layered-logic/infinity-mirror/docs/Market Analysis Report.md

---
title: Market Analysis Report
type: research
phase: 1
week: 1
date: 2026-04-06
status: complete
tags: [market, competitive, research]
---

# Market Analysis Report: The Infinity Mirror Venture
**Date:** April 6, 2026  
**Subject:** High-Rigor Assessment of Bespoke Infinity Mirrors & Illuminated Art Markets

---

## 1. Executive Summary
The market for infinity mirrors in 2026 is highly bifurcated. It is characterized by extreme price saturation at the commodity level and a growing "quality-first" recalibration at the artisanal and B2B levels. Recent market data indicates that while the "novelty" of the infinity effect has plateaued, its application as a **branding tool** and **wellness-oriented art piece** is expanding. To survive, a venture must move beyond the "maker" aesthetic to address specific 2026 pressures: protocol fragmentation (Matter/Thread), 2026 supply chain volatility, and intensifying "Right to Repair" legislation.

---

## 2. Market Segmentation & Strategic Projections

### **The "Dynamic LED" Pivot**
Industry data for 2026 confirms a decisive shift away from static glass neon and simple RGB strips.
* **Generative Art Demand:** According to the *2026 Art Trends Forecast*, collectors are prioritizing "Materiality" and "New Media" that feels organic. Addressable LEDs (WS2812B/ESP32) allow for non-repeating, generative patterns that static signage cannot replicate.
* **Atmospheric Wellness:** The **$18.4 Billion** smart lighting market now prioritizes "Circadian Integration." Static mirrors are viewed as "passive decor," whereas dynamic mirrors are sold as "active wellness" tools for focus and mood management.

### **Market Quadrants**
| Segment | Est. Price Range | Primary Materials | Key Technology |
| :--- | :--- | :--- | :--- |
| **Bespoke Luxury** | $800 – $5,000+ | Glass, Aluminum, Wood | High-Density LED, Concierge Support |
| **B2B Branding** | $250 – $1,200 | Acrylic, Metal, UV Print | Custom Firmware, SLA Reliability |
| **Sensory/Therapy** | $230 – $4,300 | High-Impact Acrylic | Simplified UI, Pulse-Width Modulation |
| **Lifestyle/Gaming** | $40 – $250 | 3D-Printed, Plastic | 2.4GHz Wi-Fi, App-Heavy |

---

## 3. Risk Assessment

### **A. Market Saturation & "Etsy Erosion"**
A cross-platform scrub of Etsy and Amazon reveals over **1,900 listings** for "Infinity Mirror Logos."
* **The Data:** Listings range from **$3.75 (Digital Files)** to **$7,860 (Large Scale Installations)**.
* **The Risk:** The $50–$120 price bracket is flooded with hobbyist-grade 3D-printed units. In this environment, a professional venture risks "Brand Bleed" if the industrial design does not immediately signal a $200+ value proposition through material weight and finish quality.

### **B. Technical Fragmenting & Hub Fatigue**
* **The Shift:** As of 2026, **Matter-over-Thread** has reached maturity. Apple and Google have largely withdrawn native support for non-Matter Wi-Fi accessories in their newest OS updates.
* **The Risk:** A product relying solely on a proprietary 2.4GHz Wi-Fi app is now classified as **"Technical Debt."** Consumers are increasingly rejecting "one-off" apps in favor of integrated Home Assistant or Matter-certified ecosystems.

### **C. Macro-Economic Discretionary Selectivity**
* **The Data:** The *2026 U.S. Art Market Report* notes that while high-income spending remains robust in the West (California/Washington), "Selectivity" has risen. The number of artists represented at auction dropped by nearly **20% in 2025**, indicating a flight to quality and established craftsmanship.
* **The Risk:** Mid-tier "discretionary" art ($150–$400) is highly vulnerable to current 2026 inflationary pressures compared to the "trophy" market or the $20 impulse market.

### **D. Regulatory & Compliance (FCC Part 15)**
* **The Reality:** Any addressable LED driver is an **unintentional radiator**.
* **The Risk:** FCC enforcement, though budget-constrained in 2026, is utilizing AI-driven monitoring to flag non-compliant electronic sellers. Commercial fines for non-certified intentional/unintentional radiators can exceed **$10,000 per violation**. This is a non-negotiable hurdle for B2B contracts.

### **E. Repairability Liability**
* **The Shift:** 2026/2027 **Right to Repair** legislation (notably the EU Directive and corresponding WA/CA bills) now mandates that electronics must be repairable using "standard tools and parts" for up to 7–10 years.
* **The Risk:** Products designed as "sealed units" are increasingly becoming illegal to sell in major markets. The venture’s "Modular/Toolless" design is not just a feature; it is a **legislative necessity**.

---

## Appendix A: Research Sources
1. **Agora Gallery:** *Top Art Trends for 2026 (Materiality & New Media Focus).*
2. **Merrill Lynch:** *2026 U.S. Art Market Report (Data on Regional Spending & Selectivity).*
3. **Gemini Made:** *2026 Signage Industry Trends (Shift to One-Stop Shops & Dimensional Signs).*
4. **Sunfire Testing:** *2026 FCC Certification Costs & Unintentional Radiator Guidelines.*
5. **Zbotic:** *Zigbee vs. Matter vs. Thread: 2026 Smart Home Protocol Guide.*
6. **Mordor Intelligence:** *Zigbee & Matter Market Share Analysis (2025-2031).*
7. **Taylor Wessing:** *New Repair Obligations for Manufacturers in 2026 (Legislative Brief).*
8. **Etsy Market Data:** *Current Pricing & Saturation Metrics for "Infinity Mirror Logo" Listings.*
9. **LaunchBoom Research:** *2026 Success Rates for Hardware Crowdfunding.*
10. **Waste Dive:** *2026 Update on State-Level Electronic Repairability Laws.*

---

## Appendix B: Product & Competitive Index

### I. Bespoke Luxury & High-End Art
* **6sigmainteriors:** Custom Aluminum Infinity Mirrors ($824.59+).
* **Light Energy Studio:** High-end casino and commercial installations.
* **Yayoi Kusama:** Immersive gallery benchmarks.
* **1stDibs:** Resale value index for Mid-Century and Art Deco Infinity Mirrors.
* **Yayoi Infinity:** Large-scale residential immersion mirrors ($2,000+).

### II. B2B Branding & Commercial
* **IDM Signs & Graphics:** 3D LED Optical Illusion Signs ($100 Deposit model).
* **Luckyneon:** Modular RGB Infinity Channel Letters.
* **Yijiao Sign:** Industrial-scale 3D Acrylic/Metal signage.
* **AOOS:** Custom 3D Tunnel Mirrors for Restaurant/Bar branding.
* **Litasign:** High-volume commercial infinity displays.

### III. Lifestyle & Gaming Decor
* **Maytrix Studio:** Octagon Smart Mirrors with Tuya integration ($222.00).
* **InfiniMini:** 6"x6" Desk Mirror competitor ($44.99).
* **Walmart:** Mass-market Hologram Infinity Mirrors ($89.99).
* **Etsy (Various):** UV-Printed Photo Infinity Boxes ($45.00–$65.00).
* **Gamer-Light:** Niche Twitch/YouTube set decor.

### IV. Sensory & Therapy
* **Enabling Devices:** Sensory Infinity Mirror with Gumball Switch ($230.95).
* **National Autism Resources:** High-durability clinical tunnels ($2,299+).
* **Westminster Tech:** Architectural-scale interactive sensory walls.
* **TFH Special Needs:** Cause-and-effect learning infinity mirrors.
* **Experia USA:** Full-scale Snoezelen-certified sensory room mirrors.

---

## Related

- [Index / MOC](../index.md)
- [Stakeholder Map](stakeholder-map.md) — customer archetypes (§3) cite this report's segments
- [BOM Breakdown](bom-breakdown-basic-6x6.md) — pricing strategy responds to the $50–120 saturation risk flagged here
- [Brand Positioning](brand-positioning.md) — positioning builds on the market bifurcation
- [Sustainability Audit](sustainability-audit.md) — right-to-repair legislation flagged here, validated there
- [Right-to-Repair Philosophy](right-to-repair-philosophy.md) — the pro-consumer posture response to §3.E regulatory context
- [Sprint Plan](../sprint_plan.md)
