layered-logic/infinity-mirror/sprint_log.md

---
title: Spring 2026 Sprint Log
type: tracking
quarter: Spring 2026
status: active
tags: [sprint, log, progress]
---

# Sprint Log — Spring 2026

Progress tracker for the Infinity Mirror sprint plan. Organized by sprint week.
Each entry is a human-written description with a date and an inline `[LL-NNN]`
link into the [task registry](tasks.md). The registry is the structured source
of truth for task identity, status, and history; the log is the daily narrative.

Format spec: [docs/task-format-v2.md](docs/task-format-v2.md). Append-only event
history is tracked separately in [task_log.md](task_log.md).

---

> **Weeks 1–6 (Mar 30 – May 9) are archived** in [sprint_log_archive.md](sprint_log_archive.md) — moved out to keep this file small. Task status lives in [tasks.md](tasks.md); event history in [task_log.md](task_log.md).

---

## Week 7 (May 12 – May 16): Service Blueprinting & The Custom Experience

### Done
- [x] [LL-074](tasks.md#LL-074) **User-flow authoring methodology locked + Stage 1 (Discover) drawn (May 13).** Emerged organically as a drill-down on [LL-053](tasks.md#LL-053): Bill asked whether each service-blueprint stage could be visualized as a Figma-style user flow, and we used Stage 1 as the methodology probe. Six iterations across one session produced both the locked HCDE grammar AND a reusable rendering recipe — both now reference artifacts the remaining nine stages will be authored against.
  - **Methodology decisions locked** in [docs/service-blueprint-flows.md § Conventions](docs/service-blueprint-flows.md): (1) Pain points reframed as user-voice diamonds (`Can I imagine this in my space?` instead of `Pain: scale not conveyed`) — flow becomes predictive of user thought process, not descriptive of system state. (2) Two-layer pain evaluation — pain question → recovery probe (also a user-voice diamond, `Is there a tool to help me visualize it?`) → either rejoins golden path on Yes or terminates at a yellow `Missing: X` callout on No. Each `Missing:` terminal is a concrete build-this backlog item. (3) Orange diamond = friction the user is evaluating; red oval = exit (user gone). The shape/color asymmetry is the story — a flow can have many friction points but only a few exits. (4) Natural cognitive order enforced for sequential question chains; for consumer-purchase Stage 1 the cascade is vibe → visualize → value → trust → timing (aesthetic gut check fires fastest, nobody visualizes a piece in their space before deciding they like the look of it). (5) Recovery is optional, not paired — some pains are genuinely unfixable at this stage (wrong vibe, wrong time) and route directly to red bounce. (6) Modality compression: multiple entry points must differ in user behavior or motivation, not channel — *Etsy listing* and *IG listing* are the same encounter for flow purposes.
  - **Rendering recipe locked** in [docs/user-flow-authoring.md](docs/user-flow-authoring.md). Mermaid ruled out: default bezier curves are too curvy; the `step` curve gives right-angle bends but no port control; the ELK plugin fails to load reliably from CDN and breaks the entire render. Switched to **Graphviz via `@viz-js/viz@3` (WASM bundle from jsdelivr)** with `splines=ortho`, explicit port specifiers on every edge (`source:e -> target:w` for Yes, `source:s -> target:n` for No), per-column `rank=same` groups, and `weight=10` on every happy-path edge to keep the top row aligned. The high-value gotcha — easy to get wrong, hard to debug from output: **in `rankdir=LR`, `rank=same` means same *column* (vertical strip), not same row.** First attempt put the whole happy path in one `rank=same` group, expecting horizontal alignment; instead got every node stacked vertically into one column with top-down primary reading order. Fixed by using per-column rank groups (each pain diamond stacked with its own bounce/recovery/missing in that diamond's column) and letting Graphviz auto-layout handle the happy path. Doc captures the rejected approaches as a debugging log so future-me doesn't relitigate.
  - **Stage 1 (Discover) drawn** in both Mermaid (renders inline in [service-blueprint-flows.md](docs/service-blueprint-flows.md) under GitHub / Obsidian with step curves) and Graphviz DOT (renders strict grid-style in [.preview/stage1.html](.preview/stage1.html) — open in any browser, viz-js loads from CDN, renders to inline SVG, no build step). Five pain diamonds along the golden path (`Does this fit my vibe?` → `Can I imagine this in my space?` → `Is this worth what they're asking?` → `Can I trust this maker?` → `Is now a good time for me to engage?`), each `Yes` continuing right, each `No` dropping down. Q1 and Q5 go straight to red bounce ovals (unfixable at this stage). Q2 / Q3 / Q4 each drop to a recovery probe diamond; the recovery `Yes` is an inverted-L back up to the next golden-path gate, the recovery `No` terminates at a yellow `Missing:` rectangle naming the concrete asset / copy / signal the venture needs to build (in-room scale-anchored photos, pricing rationale transparency, social proof / creator placement).
  - **Memory entries added** so future sessions don't repeat the trial-and-error: [feedback_flow_natural_progression](.claude/projects/C--Users-bowhi-Desktop-Independent-Study/memory/feedback_flow_natural_progression.md) (always reorder questions for natural cognitive order before shipping) and [reference_user_flow_authoring](.claude/projects/C--Users-bowhi-Desktop-Independent-Study/memory/reference_user_flow_authoring.md) (pointer to docs/user-flow-authoring.md as the canonical methodology + rendering recipe).
  - **Index updated** — both [service-blueprint.md](docs/service-blueprint.md) and [user-flow-authoring.md](docs/user-flow-authoring.md) now linked from [index.md § HCDE Artifacts](index.md).
  - **What this unlocks:** the remaining nine stage flows (2 — Consider, 2b — Consult custom, 3 — Purchase, 4 — Manufacture & QC, 5 — Fulfill, 6 — Unbox & set up, 7 — Daily use, 8 — Trouble & repair, 9 — Returns, 10 — End-of-life) can now be drafted against a locked grammar and reusable templates. Stage 6 (Unbox & Set Up) is in the doc as a pre-v4 placeholder with a "pending retrofit" marker and will be the first to retrofit against the new grammar when work resumes.

- [x] [LL-053](tasks.md#LL-053) [LL-054](tasks.md#LL-054) **Service blueprint landed, including custom-order deep dive (May 13).** Anchor Week 7 deliverable. [docs/service-blueprint.md](docs/service-blueprint.md) maps the complete customer journey across 10 stages — Discover → Consider → (Consult & co-design for custom) → Purchase → Manufacture & QC → Fulfill → Unbox & Set Up → Daily Use → Trouble & Repair → Returns → End-of-Life — with four lanes per stage (Customer Journey / Frontstage / Backstage / Support Systems & Partners), explicit moments-of-truth callouts, and named fail-point lists at every step. The doc is a synthesis layer over the existing vault rather than a parallel artifact: each stage links into the [stakeholder map](docs/stakeholder-map.md) for who's involved, [Assembly_docs](Assembly_docs/) for production detail, [repair-index](docs/repair-index.md) + [Failure_Modes](Failure_Modes/) catalog for the trouble path, [supply-chain map](docs/supply-chain-map.md) for sourcing, [sustainability audit](docs/sustainability-audit.md) for end-of-life, [button-interface](docs/button-interface.md) + [button rationale](docs/button-design-rationale.md) for Stage 6/7 physical UI, [brand positioning](docs/brand-positioning.md) for tone, and the firmware/app/OTA spec docs for the digital-product surfaces. Custom-order branch ([LL-054](tasks.md#LL-054)) is a dedicated Deep Dive section in the same doc: 10-step flow (inquiry → discovery → concept + price band → design proof → ≤3 free revisions → approval + 50% deposit → manufacture → pre-ship review → balance + ship → standard post-purchase), frontstage/backstage table, three custom-specific moments of truth, five fail-points, five open research questions threaded back into [LL-048](tasks.md#LL-048) end-buyer interview agenda. Cross-cutting system-properties table captures the journey-wide guarantees (works without app, mDNS discovery, OTA + rollback, toolless disassembly, JST-modular electronics, commodity parts, documented from day one, open-source on founder exit). Final summary table compresses all 10 stages to one row each for the portfolio-skim view. Open-actions table surfaces 4 new triageable items not yet tracked: define repair-video pipeline (which RMAs trigger filming, where they live), decide custom-order deposit structure (50% at approval vs. 25%/25% split), define carrier insurance threshold, address gift-giver/recipient address-mismatch at fulfillment — flagged for future LL-NNN promotion, not added to the registry inline. No new dependencies introduced; doc is positioned as feed into [LL-061](tasks.md#LL-061) portfolio case study and as the artifact that proves the HCDE-venture thesis ("system, not gadget") in the Week 10 deliverable.

- [x] [LL-047](tasks.md#LL-047) **App design-rationale wireframes — chapter 1 (Settings → Wi-Fi) landed (May 14).** Pivoted [LL-047](tasks.md#LL-047) from "Figma wireframes" to SVG-native lo-fi wireframes paired with markdown rationale docs — works as portfolio chapters that index into the existing decision docs (multi-network-design, button-design-rationale, service-blueprint) rather than producing parallel artifacts in Figma. Each chapter consists of one [docs/wireframes/<screen>.svg](docs/wireframes/) lo-fi wireframe (brand-indigo accent on grayscale, callouts pairing UI decisions to source rationale, alternate-state thumbnails below the resting state) plus one [docs/wireframes/<screen>.md](docs/wireframes/) markdown chapter (TL;DR, journey link, per-callout decisions, considered & rejected, research-to-design honesty table, implementation gaps, what shipped, references). **Chapter 1** is [Settings — Wi-Fi](docs/wireframes/settings-wifi.md) — densest decision history in the app: 6 first-order UX decisions (IP surfacing, server-truth active checkmark, Connect-per-row, Forget-active confirm modal, adding≠joining, N_MAX=4 with explicit eviction), 4 alternate states (loading, switching, confirm-forget, list-full), and a research-to-design honesty audit marking which decisions are founder-intuition (most) vs hardware-validated (③ Connect button came from LL-046 step 6 testing) vs code-validated (② active checkmark cross-client correctness). Flagged the curated firmware-update section (single "Check for updates" button) as an implementation gap — the shipped App/v1 still exposes a raw OTA URL textarea, future [LL-071](tasks.md#LL-071) work. **Template locked** for chapters 2-5: Home/Control (color wheel + brightness + pattern), First-boot Setup (SoftAP captive flow), Mirror picker (multi-mirror discovery), Custom design request (Stage 2b consult flow). Deadline shifted May 9 → Jun 6 to land alongside Week 10 portfolio assembly.

- [x] [LL-047](tasks.md#LL-047) **App design-rationale wireframes — chapters 2-5 landed (May 14-15; logged May 20).** The remaining four chapters that complete the LL-047 set were authored May 14-15 and merged via PR #19; the registry was not updated at the time, so this is a catch-up entry after verifying the files on May 20. Chapter 2 [home-control](docs/wireframes/home-control.md) (power / color wheel / brightness / pattern — 6 callouts, the explicit-Power and discrete-brightness decisions), chapter 3 [first-boot-setup](docs/wireframes/first-boot-setup.md) (SoftAP captive provisioning — the screen that tears down its own WS channel as part of normal operation, which drives most of its decisions), chapter 4 [mirror-picker](docs/wireframes/mirror-picker.md) (mDNS discovery via NsdManager, conditional-on-count picker), chapter 5 [pattern-designer](docs/wireframes/pattern-designer.md) (a deliberately speculative V2 pattern-editor mockup). Each is an SVG lo-fi wireframe plus a paired markdown chapter on the locked chapter-1 template. **Chapter 5 was swapped** from the originally-planned "Custom design request (Stage 2b consult)" to the V2 pattern editor: the custom-order consult flow is an email/web/conversation flow with no App/v1 screen to wireframe, whereas the pattern editor is a real (future) app surface and the natural extension chapter 2's callout ⑤ flagged. All five chapters keep `status: draft` (ch5 `speculative-v2`) by design — the design rationale stays provisional until [LL-048](tasks.md#LL-048) end-buyer interviews validate it. LL-047 closed.

- [x] [LL-051](tasks.md#LL-051) **Packaging concept — parametric REFT mailer + N-slot insert generators with validation suite (May 12).** Two production-ready Python part-libraries that emit dieline geometry for any L/W/H/t (and slot configuration for the insert), validated against 5 reference CEFbox DXFs per template. Long iterative day:
  - **Path A → B → A pivots**: started with hand-derived sketch (wrong geometry, caught when Bill compared to CEFbox screenshots); pivoted to per-coord parametric formula recovery against 10 paid CEFbox DXFs (~60% of coords resolved cleanly, ~40% needed separate arc-parameter recovery); pivoted again to a NAMED-PARTS architecture (graph of structural pieces with rules + Y-symmetry as a hard constraint).
  - **Mailer in 6 phases** ([Assembly_docs/packaging/mailer_reft.py](Assembly_docs/packaging/mailer_reft.py)): spine + scores → roll-end side walls with W-conditional tooth pattern → dust flaps with case-A/B logic at H ≈ 100−2.5t threshold → ear-lock arcs (4 main + 2 horns + 2 score-tangents + 4 tangent diagonals) → finger holes (1 per outer tooth) → cleanup with 14 panel-fold scores + corner connectors. **Critical bug caught mid-build**: dieline mirror axis is `x = L/2 + 5t`, NOT `x = L/2` — every right-side coord was off by 10t until traced via a manual symmetry inspection of the baseline DXF.
  - **Insert in 5 phases** ([Assembly_docs/packaging/insert_tray.py](Assembly_docs/packaging/insert_tray.py)): floor + scores + slot-and-cradle → top bands (back wall + hem + backer + hem flap) → front wall + bottom corner arcs → side walls + corner arcs → tangent diagonals + corner micro-chamfers. **N-slot support from day one** via `Slot(cx, cy, SL, SW, SH)` records; `InsertSpec.n_slot()` distributes evenly along L; arbitrary placements supported by passing a custom `slots=[...]` list. Degenerate-cradle handling for SH ≥ SL/2 or SW/2 (collapses to a Line).
  - **Validation framework** ([Assembly_docs/packaging/validation.py](Assembly_docs/packaging/validation.py)): two automated tests per generator-vs-reference comparison: (1) entity-count match per layer (LINE/ARC/LWPOLYLINE on cuttingLine vs foldingLine), (2) Y-symmetry — every entity must have a mirror partner about the axis. Arc canonicalization via `(midpoint, sweep)` to handle 0/360 wrap; polyline canonicalization dedupes explicit closing points; 0.01mm rounding precision to defeat FP drift between left/right mirrored values. `TestCase` supports `skip_symmetry: bool` for asymmetric multi-slot inserts. **Result: 10/10 reference DXF tests pass** (5 mailer + 5 insert).
  - **Renderer style fix** ([Assembly_docs/packaging/cefbox_render.py](Assembly_docs/packaging/cefbox_render.py)): solid lines, color-only differentiation between cut (red) and score (blue) per Bill's preference.
  - **Inspection tooling**: [dxf_inspect.py](Assembly_docs/packaging/dxf_inspect.py) prints structured entity inventory grouped by region; [dxf_to_png.py](Assembly_docs/packaging/dxf_to_png.py) passthrough renderer for reference DXFs.
  - **CEFbox-style geometric rules** added to both Specs as `validate()` methods called automatically at the start of `generate()`. Insert: 5mm slot-edge buffer from floor edges + 5mm pairwise slot gap. Mailer: W ≥ 180 (tooth pattern lower bound), L ≥ 60, H ∈ [20, 200], t ∈ [0.5, 5.0], H ≥ 2t (case A non-degenerate). Bad inputs raise `ValueError` with specific actionable messages.
  - **Reference DXFs** captured in `Assembly_docs/Packaging_Templates/` (gitignored — paid CEFbox content). 10 files total at controlled dimension variations. Practical bbox at the 225×225×60 user-target mailer is **498.5 × 638.25 mm** — fits a 520×660 sheet with 10mm hold-down margin, recommended 600×800 for 1-up production with registration room.
  - **Custom configurations rendered** end-to-end: 1-slot baseline, 2-slot evenly-distributed (PSU compartment scenario), arbitrary asymmetric 2-slot (200×200 BL + 40×80 TR — flagged out-of-bounds when tried at L=250 W=280 thanks to the new buffer rules).
  - **Out of scope today**: `nest.py` for sheet packing via `rectpack`, first physical test cut, [LL-044](tasks.md#LL-044) QR raster wiring. Each is a separate workstream now unblocked by this work.
  - **Imported into this branch May 14** after discovering the work was uncommitted in the `gifted-tharp-af5d28` worktree. An earlier import attempt (c498966) accidentally committed the paid CEFbox reference DXFs into the public repo — reverted in c3ae593 and the gitignore rule added. The actual deliverable is the parametric generators, not the references.

- [x] [LL-055](tasks.md#LL-055) **Broadcast debounce shipped (May 14) — LL-055 fix #1 of N.** Transport's `broadcast_state()` was firing one WS broadcast per primitive state-bus event — for a 3-field `set_state` that was 3 frames in rapid succession, all carrying nearly-identical state, plus the rapid-click case from [post-mini-sprint-bugs.md #1](docs/post-mini-sprint-bugs.md) where 6-8 color preset clicks each generated their own broadcast. Replaced with a 30ms one-shot timer ([Firmware/v1/core/transport/transport.c](Firmware/v1/core/transport/transport.c)): first call arms the timer + sets an atomic-bool pending flag; subsequent calls within the window are no-ops (the pending broadcast will capture the latest state at fire-time anyway). Timer callback clears the flag and runs the existing broadcast logic (renamed `do_broadcast_state`). Fallback path on timer-start failure: immediate broadcast, so transient timer failures don't silently drop state updates. Thread-safe across state-bus, httpd, and esp_timer tasks via stdatomic.h. **Generalized over the bug-doc's "fix #1" framing:** the doc described coalescing only inside `op_set_state`; this debounce catches both the multi-field-set_state case AND the original rapid-click scenario with one mechanism. **Verified on live mirror at 192.168.5.229** via [`Firmware/v1/scripts/ll_debounce_test.py`](Firmware/v1/scripts/ll_debounce_test.py) (Python WS client): single-field `set_state` produced 1 response + 1 broadcast (expected); 3-field `set_state` produced 1 response + 1 broadcast (was 3 before); 6 rapid color sets at ~30ms intervals produced 6 responses + 2 broadcasts (first 5 sends coalesced into 1; 6th fell outside the prior timer window and got its own — correct burst-coalescing, not blanket "always-1" collapse). Build + OTA + verify cycle ran clean: clean rebuild from a fresh worktree (set-target esp32c3, npm webapp build, idf.py build → 0x1274e0 bytes / 8% headroom on the app partition), OTA-flashed via the standard runbook ([docs/ota-dev-runbook.md](docs/ota-dev-runbook.md)) with the dev HTTP server bound to the LAN IP (192.168.1.98:8000) to coexist with Syncthing's loopback :8000. **Next on [LL-055](tasks.md#LL-055):** bug-doc fix #2 (move broadcast fanout to a separate task / queue — the architecturally-right fix, ~1 day) OR pivot to the resilience scenarios (Wi-Fi drop handling, BLE reconnect, network jitter under load).

- [x] [LL-055](tasks.md#LL-055) **Session A — Wi-Fi power-save disabled (May 15) — LL-055 fix #2 of N, bug-doc fix #4.** Diagnostic-then-fix on the variable [post-mini-sprint-bugs.md #4](docs/post-mini-sprint-bugs.md) calls out: ESP32 modem-sleep latency on the STA path. **Audit:** grep across [Firmware/v1/](Firmware/v1/) for `esp_wifi_set_ps` / `WIFI_PS_` returned **zero hits** — STA was inheriting IDF's default `WIFI_PS_MIN_MODEM`, sleeping between DTIM intervals (~100ms typical). **Fix:** one helper `ll_wifi_disable_ps(where)` in [provisioning.c:113](Firmware/v1/core/provisioning/provisioning.c) that calls `esp_wifi_set_ps(WIFI_PS_NONE)` and logs INFO on success / WARN-and-continue on error; called after each of the four `esp_wifi_start()` sites (init STA boot path, init SoftAP boot path, apply_creds STA handoff, SoftAP fallback restart). AP-only mode is a no-op since beacons run anyway; APSTA, when it lands, gets the STA side covered too. **Before/after measurement** via the same [ll_debounce_test.py](Firmware/v1/scripts/ll_debounce_test.py) used for fix #1 (mirror at `192.168.5.229`, dev PC ethernet `192.168.1.98`): Test A (single-field set_state) first-response latency **155ms → 84ms (−46%)**; Test B (3-field set_state) **136ms → 64ms (−53%)**; Test C (6 rapid color sets) **202ms → 187ms (−7%)** — Test C is dominated by the script's own 5×30ms inter-send sleeps so the radio-wake delta gets compressed. Debounce count behavior unchanged (3 broadcasts on Test C both runs — expected, debounce logic untouched). **Build + OTA workflow wrinkles surfaced and captured:**
  - Fresh worktree needed `npm install` in [Firmware/v1/webapp/](Firmware/v1/webapp/) before `idf.py build` — the webapp embeds into the firmware via `core/webapp_assets/`, so a missing `dist/index.html.gz` fails CMake config rather than just skipping the embedded asset.
  - Fresh worktree's `sdkconfig` was at the IDF default `CONFIG_IDF_TARGET="esp32"`, not `esp32c3`. First two OTA attempts pulled the binary cleanly (HTTP 200 in the dev-server log) but the device rejected with `ESP_ERR_INVALID_VERSION` — that error path also covers chip-ID mismatch, not just version-equal. Fixed by `Remove-Item sdkconfig; idf.py -DLL_BOARD=c3_devkit set-target esp32c3` per the README.
  - `git describe --dirty` collides across iterations when only uncommitted changes differ — passed `-DPROJECT_VER="ps-none-$(Get-Date -Format 'HHmm')"` to force a distinguishable version string. The README already calls this out; reaffirmed here because it bit me even after explicitly passing PROJECT_VER (the chip-ID issue was masking it).
  - Verify pass: post-OTA ping returned `fw_version: ps-none-0915, uptime_s: 91` — clean boot, low uptime confirms the reboot took.
  - Build budget: 1.114 MB / 1.25 MB slot (15% free). +56 bytes for the helper + logging string.
  **Next on [LL-055](tasks.md#LL-055):** Session B — move broadcast fanout to a separate FreeRTOS task + queue (architecturally-right fix #2 from the bug doc, ~1 day). The current 30ms debounce timer becomes the enqueuer; new task owns the loop over connected fds. After that: Session C rate limit, Session D Wi-Fi drop / jitter scenarios.

- [x] [LL-055](tasks.md#LL-055) **Session B — broadcast fanout on a dedicated FreeRTOS task (May 15) — LL-055 fix #3 of N, bug-doc fix #2.** The architecturally-right fix from [post-mini-sprint-bugs.md #1](docs/post-mini-sprint-bugs.md): inbound dispatch on the httpd task must not block on outbound socket writes. **Why it still mattered after Session A's debounce + the May 14 fix #1:** the 30ms debounce timer was moving the *trigger* off-thread (esp_timer task ran the fanout), but `httpd_ws_send_frame_async` actually sends synchronously from the calling task — so a slow client's TCP backpressure tied up the esp_timer task, which is shared with every other timer in the firmware. Bursts of broadcasts shared runtime with system timers; a stalled send blocked all subsequent broadcasts. **Architecture** ([Firmware/v1/core/transport/transport.c](Firmware/v1/core/transport/transport.c)):
  - New static `s_broadcast_q` — `QueueHandle_t`, depth 2, holds 1-byte tokens. Queue-full → drop (the next state-change re-arms the debounce timer and a fresh token lands; each dequeue snapshots latest state via `ll_state_bus_get()`, so dropping one in-burst token is benign).
  - New static `s_broadcast_task` — FreeRTOS task `ll_broadcast`, 4 KB stack, priority 4 (below httpd's default 7, so inbound work always wins runtime contention). Body is a simple `xQueueReceive(portMAX_DELAY) → do_broadcast_state()` loop.
  - `broadcast_timer_cb` no longer calls `do_broadcast_state()` directly — instead posts a token via `enqueue_broadcast("timer-cb")`. The `broadcast_state` fallback (timer-start-failed) now also enqueues rather than running synchronously on the caller's task, preserving the no-block-the-caller invariant.
  - `enqueue_broadcast()` has a fallback for the pre-init window (queue null) that runs the fanout synchronously — only relevant if a broadcast fires before `ll_transport_init` finishes; in practice that doesn't happen because state-bus events aren't subscribed until later.
  - Updated the file-header threading comment to describe the new dispatch path (state-bus / httpd → broadcast_state → debounce timer → enqueue → broadcast task).
  - **Build cost:** +96 KB (FreeRTOS queue/task symbols newly linked). Binary now 1.21 MB / 1.25 MB partition (92% utilization, 7.6% headroom). Watching the headroom — Session C rate-limit + future telemetry will eat into this; if it gets tight, dropping unused IDF components from `REQUIRES` is the first lever.
  **Verified on live mirror at 192.168.5.229:**
  - **Regression — [ll_debounce_test.py](Firmware/v1/scripts/ll_debounce_test.py)**: Test A 1 response + 1 broadcast (unchanged); Test B 1 + 1 (unchanged); Test C 6 responses + 4 broadcasts (vs 3 last run — within burst-coalescing tolerance, the exact count depends on how the 30ms inter-send timing aligns with the debounce window). First-response latency essentially unchanged from Session A (69ms / 72ms / 186ms vs Session A's 84ms / 64ms / 187ms).
  - **New test — [ll_slow_client_test.py](Firmware/v1/scripts/ll_slow_client_test.py)**: opens a "slow" WS client that completes one round-trip (to register itself with the framework) then stops reading, while a "fast" client measures `set_state → response` RTT over 20 probes. **Result: 20/20 responses in both phases; median 72.2ms baseline → 70.7ms with slow client; p90 95.0ms → 88.2ms; max 99.8ms → 128.8ms.** Inbound dispatch is unaffected by a deadweight outbound socket. The modest max bump (~30ms) is the expected queue-contention signature when the broadcast task is mid-send to the slow fd — bounded and recoverable, not a stall.
  - Build → OTA (PROJECT_VER=`bcast-task-0925`) → boot capture (uptime_s 86) → measurement, per the per-fix verify rule. Clean run; no new bug-doc entries needed.
  **Next on [LL-055](tasks.md#LL-055):** Session C — implement spec §7.1 rate limit (per-fd token bucket, 10 msg/s + burst 10, close 1008 on overrun), ~½ day.

- [x] [LL-055](tasks.md#LL-055) **Session C — per-IP rate limit (May 15) — LL-055 fix #4 of N, bug-doc fix #3, spec §7.1 closeout.** The spec'd contract had been documented but unenforced ([control-protocol-spec.md §7.1](docs/control-protocol-spec.md): "Per-IP rate limit: 10 messages/sec. Exceeding results in close code 1008"). Sessions A + B made the *steady-state* case responsive; this session adds the *malicious-or-buggy-client* guard so flood traffic gets rejected proactively at the dispatch boundary rather than backpressuring the broadcast task. **Implementation** ([Firmware/v1/core/transport/transport.c](Firmware/v1/core/transport/transport.c)):
  - **Token bucket per peer IP, milli-token math.** Burst capacity 10,000 milli-tokens (= 10 messages), refill 1 milli-token per 100µs (= 10 tokens/sec). Avoids float math on the C3.
  - **Fixed table of 8 entries** (`s_rl_table[]`) — matches the spec's 8-client cap. Lookup is linear scan; eviction on full uses oldest `last_refill_us` so a dormant attacker IP can't squat a slot.
  - **IPv4 from fd via `getpeername`** + `<lwip/sockets.h>`. Handles both `AF_INET` and v4-mapped `AF_INET6` (lwip's default representation); reserves `ip_be==0` as "slot unused" by remapping to `0xFFFFFFFF` if it ever happens to fall on a literal 0.0.0.0.
  - **Single-task access** (httpd's WS handler is single-task) → no locking needed.
  - **Enforced on `HTTPD_WS_TYPE_TEXT` frames only** — control frames (ping/pong/close) handled by httpd directly and don't consume tokens.
  - **Overrun path:** log `WARN`, send WS close frame with code 1008 ("policy violation") via a new `ws_send_close()` helper, then `httpd_sess_trigger_close()` to clean up the framework's session state. Best-effort — the close frame may not deliver if the client's send buffer is wedged, but we drop the socket regardless.
  - **Fail-open on `getpeername` errors** with a `WARN` — losing rate-limit enforcement on a busted socket is safer than dropping legitimate traffic; the flood path is still bounded by the 8-client cap.
  - **Build cost:** +1.4 KB (1.21 MB / 1.25 MB partition, 7.5% headroom — within ~0.1% of Session B, the rate-limit code is small).
  **Verified on live mirror at 192.168.5.229** via new [ll_ratelimit_test.py](Firmware/v1/scripts/ll_ratelimit_test.py):
  - **Steady 10 msg/s for 3s:** sent=30, responses=30, close_code=None ✅ (right at the limit, refill matches consume).
  - **Flood at 50 msg/s:** sent=14 before close, responses=13 ACKed, **close_code=1008** at t=0.43s ✅ (bucket drained through the initial burst + partial refill — the math allows ~13 sends before the bucket actually depletes; close is fast).
  - **After-close recovery:** sleep 2s → reconnect → `ping` returns OK ✅ (table entry persists, tokens refill correctly across the close-and-reconnect cycle).
  - **Regression — [ll_debounce_test.py](Firmware/v1/scripts/ll_debounce_test.py):** Test A 1+1, Test B 1+1, Test C 6 sends + 3 broadcasts (clean — same counts as the May 14 baseline). Latency unchanged.
  - **Regression — [ll_slow_client_test.py](Firmware/v1/scripts/ll_slow_client_test.py):** had to bump the fast probe loop from 50ms → 100ms intervals (test was sending 20 msg/s, would have tripped the new 1008 close partway through; the bug was in the test, not the firmware). Post-fix: 20/20 in both phases; median 66.8ms baseline vs 66.8ms slow-pinned (identical); p90 84.0ms vs 75.0ms (slight improvement, likely the slow-client connection warming the AP path).
  Build → OTA (PROJECT_VER=`ratelimit-0955`) → boot capture (uptime_s 86) → measurement, per the per-fix verify rule. **Next on [LL-055](tasks.md#LL-055):** Session D — Wi-Fi drop + jitter resilience scenarios (open-ended; STA-AP kill/restore reconnect measurement + Clumsy-injected loss/latency replay of debounce + flood scripts). The bug-doc cascade is now closed; Session D is the new-territory work the task notes called out from the start.

- [x] [LL-055](tasks.md#LL-055) **Session D — resilience characterization + test harness (May 15) — LL-055 closeout.** Open-ended scenarios from the locked plan: code-review the disconnect/reconnect path, characterize behavior under stress (reconnect storms, injected latency, injected packet loss, sustained load), build durable test rigs that future resilience work can reuse. **No firmware changes this session** — Session D is a characterization pass on the work that landed in Sessions A-C. The artifact set is in [Firmware/v1/scripts/](Firmware/v1/scripts/): `ll_reconnect_hammer.py`, `ll_ws_proxy.py`, `ll_jitter_test.py`, `ll_soak_test.py`, `ll_ap_toggle_test.py`. **Code review** confirmed [provisioning.c](Firmware/v1/core/provisioning/provisioning.c) has the right structure (SM with IDLE→SCANNING→CONNECTING→ONLINE→SCANNING-on-disconnect cycle, 5s/15s/60s backoff with `recently_failed_mask`, 8s connect-timeout watchdog) and [transport.c](Firmware/v1/core/transport/transport.c)'s `on_wifi_disconnected` broadcasts before `httpd_stop` (clean fd teardown). **Results, all autonomous on mirror 192.168.5.229 running `ratelimit-0955`:**
  - **Reconnect hammer** ([ll_reconnect_hammer.py](Firmware/v1/scripts/ll_reconnect_hammer.py)) — 30× WS open + ping + close in 8.1s (≈3.7/s, comfortably under the 10 msg/s rate-limit). **30/30 successes, 0 failures.** Open+ping RTT median 95.2ms, p90 114ms, max 206ms (one outlier). Uptime monotonic 630s → 638s. No fd accumulation, no rate-limit drift across rapid handshakes, no reboot.
  - **Latency injection — 200ms one-way** via a new TCP-level [ll_ws_proxy.py](Firmware/v1/scripts/ll_ws_proxy.py) sitting between client and mirror. 400ms RTT minimum. **10/10 set_state probes succeed**, median 628ms RTT (consistent with 400ms injected + ~225ms direct mirror processing). The 30ms debounce window is well below the injected latency → no false coalescing. Steady high-latency networks work transparently.
  - **Loss injection — bracketed two scenarios:**
    - **5% chunk loss:** WS upgrade handshake itself times out. Small handshake exchange (3-5 chunks) doesn't survive that much loss. Fails fast (10s timeout from the `websockets` library), not silently hung. Not a firmware defect — that's TCP/WS behavior under severe-interference conditions.
    - **1% chunk loss:** 10/10 probes succeed at normal RTT (median 65.5ms, max 82.8ms). TCP retransmit handles drops transparently. **Realistic Wi-Fi loss thresholds (<1% on a healthy link) are fully covered.**
  - **5-minute soak** ([ll_soak_test.py](Firmware/v1/scripts/ll_soak_test.py)) — sustained 5 msg/s set_state over 240s wall-clock + ping-every-60s on a parallel channel. **1476 iterations, 0 errors, 0 rate-limit closes.** RTT distribution: min 49.4ms, median 67.8ms, p90 86.0ms, max 190ms. **First-half median 68.0ms vs second-half median 67.6ms — drift −0.4ms.** Zero memory/queue creep over 4 minutes of continuous load. Uptime monotonic 824s → 1064s (delta = exact 240s run duration → no reboot, no watchdog trip). The dedicated broadcast task from Session B holds up cleanly under sustained throughput.
  - **STA-AP toggle test** ([ll_ap_toggle_test.py](Firmware/v1/scripts/ll_ap_toggle_test.py)) — **manual, handed over to Bill.** Script records uptime + RTT every 3s, detects disconnect, retries reconnect every 5s, reports outage gap + whether uptime resumed monotonically (proving the SM re-joined rather than rebooted). Requires turning off the Pixel hotspot mid-run for ~30s. Will run whenever the toggle gesture is convenient; any defects surfaced become a separate task.
  **No new bug-doc entries opened.** [Bug-doc #1](docs/post-mini-sprint-bugs.md) (transient socket-closed under user load) — the single open entry that motivated LL-055 — now has all four of its proposed fixes shipped (#1 coalesce-on-multi-field-set_state via debounce → May 14; #2 broadcast-on-separate-task → Session B; #3 spec §7.1 rate-limit → Session C; #4 SoftAP power-save audit → Session A). Closed and moved to the Closed section of [post-mini-sprint-bugs.md](docs/post-mini-sprint-bugs.md) in this same session. **LL-055 closed** — the resilience stress-test suite is complete; the artifact set is durable enough to re-run as a regression battery on future firmware changes. [LL-055-1](tasks.md#LL-055-1) (BLE reconnection) remains parked-on-dependency until BLE provisioning ships post-V1.

- [x] [LL-075](tasks.md#LL-075) **On/brightness wire-state coupling (May 15) — closes [post-mini-sprint-bugs.md #2](docs/post-mini-sprint-bugs.md).** Defensive fix in [state_bus.c apply_event](Firmware/v1/core/state_bus/state_bus.c): the on and brightness fields are no longer independently mutable. **Invariants:** `LL_EV_BRIGHTNESS` now also sets `on = (value > 0)` (brightness=0 implies off, brightness>0 implies on); `LL_EV_POWER_TOGGLE{on:true}` auto-restores brightness to 75 if currently 0 (so a single-press from off after a webapp `{brightness:0}` set doesn't leave LEDs dark with on=true). **Power-off (`on:false`) deliberately preserves brightness** — important UX: button long-hold → single-press cycle keeps the user's brightness setting, doesn't reset to default. The renderer already gates on `s->on` (pattern_interp.c:151), so an (on=false, brightness=75) state still renders dark; brightness is just memory. **Boot self-heal:** `ll_state_bus_init` checks for the legacy contradictory state on entry and corrects (on=true, brightness=0) → (on=true, brightness=75), so a pre-fix NVS blob doesn't ship the bug on first power-up. **Verified on `192.168.5.229`** (firmware `on-bright-coupling-1037`) via new [ll_on_brightness_invariant_test.py](Firmware/v1/scripts/ll_on_brightness_invariant_test.py) — all 6 cases pass:
  - Test A: `{brightness:60}` → (on=true, brightness=60) ✓
  - Test B: `{brightness:0}` → (on=false, brightness=0) ✓
  - Test C: `{on:true}` while brightness was 0 → auto-restore to 75 ✓
  - Test D: `{on:false}` with brightness=60 → (on=false, brightness=60) preserved ✓
  - Test E1: coupled `{on:true, brightness:80}` → (true, 80) ✓
  - Test E2: coupled `{on:false, brightness:0}` → (false, 0) ✓

  Build cost negligible (~20 bytes for the constants + arithmetic). Regressions clean (ll_debounce_test 1+1/1+1/6+5 — burst-coalescing within tolerance, first-response latency 63ms median consistent with PS-NONE). The webapp's closed [bug #3](docs/post-mini-sprint-bugs.md) couples its `set_state` envelopes already, so the firmware coupling is belt-and-suspenders for that path; the real win is the button-path + diagnostics-view scenarios that the webapp's client-side coupling couldn't reach. **Bug-doc #2 moved to Closed** with a closeout summary linking the LL-075 fix.

- [x] [LL-057-A](tasks.md#LL-057-A) **LL-057 Session A — stuck-OTA-button useEffect reset (May 15) — closes the LL-040 follow-up note.** App's OTA button has been stuck on "Mirror downloading + rebooting…" forever after success since [LL-040](tasks.md#LL-040) (May 1) — surfaced as a known follow-up in LL-040's notes, parked until LL-057 picked it up. Fix in [App/v1/App.tsx](App/v1/App.tsx): new `prevConnRef = useRef<ConnState>(conn)` plus a `useEffect([conn, otaState])` that resets `otaState` from `'rebooting'` → `'idle'` on the *transition* from non-open to open. **The transition-vs-steady-state distinction is load-bearing:** when the user taps the button `conn` is already `'open'`, so a naive watcher would fire as soon as `otaState` flips to `'rebooting'` and reset back to `'idle'` before the mirror has even rebooted. The ref captures the previous conn so the effect only fires on the post-reboot reconnect. 13 lines net. **Verification:** `tsc --noEmit` clean against the new code; 4 pre-existing errors in [protocol.ts](App/v1/src/protocol.ts) (`crypto` globals) and [ws-client.ts](App/v1/src/ws-client.ts) (`MessageEvent`) are unrelated DOM-lib config issues that predate this change. Runtime verification deferred to Bill's next Pixel 9 session — needs the full OTA cycle through the app UI to confirm the auto-reset fires. **LL-057 scope locked as "wide":** telemetry + paired-mode auth stay in-scope rather than spinning out. Full session plan (A → B → C → D) recorded in [LL-057 notes](tasks.md#LL-057); will slip past the May 23 Week 8 deadline.

- [x] [LL-057-B](tasks.md#LL-057-B) **LL-057 Session B — real OTA progress: bisected as architecturally blocked, partial close (May 15).** Targeted "Real progress" per the OTA-polish bar Bill picked when LL-057 scope was set to wide. Spent the session prototyping three approaches; each one converged on the same constraint: **emitting wire-level progress broadcasts while `esp_https_ota` is running on the httpd task breaks the install.** **What was tried, in order:**
  1. **Migrate `ll_ota_start` to `esp_https_ota_begin / perform / finish`** with a percent-from-Content-Length loop. New `ll_transport_broadcast_ota_progress` in transport.c (refactored a shared `fanout_text_to_ws_clients` helper out of `do_broadcast_state` along the way) + a new wire op `{op:"ota_progress", phase, percent}`. ESP_FAIL on every OTA install attempt.
  2. **Switch to subscribing `ESP_HTTPS_OTA_EVENT`** (minimal-diff: keep the one-shot `esp_https_ota` call, just observe lifecycle events from the default event loop). Still ESP_FAIL.
  3. **Bisect through diagnostic builds.** `transport.h` include + `PRIV_REQUIRES transport` in ota.c with a no-op event handler — clean install. Add a single `ll_transport_broadcast_ota_progress` call on the START event — install returns success-like TIMEOUT but new image fails boot validation (silent rollback). Add full lifecycle (START + FINISH + ABORT) — ESP_FAIL on install. **Wrapper-only** (broadcast from `op_start_ota` in transport.c BEFORE and AFTER calling `ll_ota_start`, never inside the OTA window) — still ESP_FAIL.
  **The last finding broke the original hypothesis** that the issue was just LWIP/httpd-lock contention from concurrent task-level WS sends. The wrapper broadcast fires on the httpd task ITSELF, before `esp_https_ota` is called — yet still fails. **Compounding issue:** by the end of the bisect the mirror (192.168.5.229, currently running `ota-diag-priv-req-1153`) had refused 5+ consecutive OTA installs in a row, including a deliberate `ota-rollback-1214` build with literally zero behavioral changes from the working baseline. The chain of failed installs has left the otadata / ota_X partition slots in a state the running firmware's `esp_https_ota` won't accept (consistent ESP_FAIL, no specific cause exposed without serial logs). **Device-side recovery needs USB access:** `idf.py -p COM<n> erase-flash && idf.py -p COM<n> flash` to wipe the otadata partition and reset the ota_X slots cleanly. Tracking as a follow-up; flagged to Bill.
  **What's keeping:**
  - App-side wire-type scaffolding: `OtaPhase` + `OtaProgressBroadcast` + `isOtaProgress` in both [App/v1/src/protocol.ts](App/v1/src/protocol.ts) and [Firmware/v1/webapp/src/protocol.ts](Firmware/v1/webapp/src/protocol.ts); `onOtaProgress` callback added to both ws-client.ts; [App/v1/App.tsx](App/v1/App.tsx) wires an `otaProgress` state + `otaProgressLabel` helper that renders `Downloading firmware… N%` / `Verifying image…` / `Rebooting…` / `Update failed` per phase, falling back to the pre-streaming "Mirror downloading + rebooting…" string when no progress events arrive. Forward-compatible — when the firmware progress path is fixed later, the app immediately benefits with no further changes.
  - The `ll_transport_broadcast_ota_progress` function and `fanout_text_to_ws_clients` helper from the Session B exploration were **reverted** from transport.c. They'll come back if/when Session B reopens.
  **What's deferred to a future LL-057-B retry** (when device is recovered + we have time): probably need to move `ll_ota_start` off the httpd task entirely (spawn a dedicated OTA task; httpd's WS handler just queues the request) so the OTA window doesn't intersect with WS dispatch. The state-bus's broadcast task from Session B already has the right shape; reusing that pattern for OTA is the design lead.
  Session A's stuck-OTA-button fix ([LL-057-A](tasks.md#LL-057-A)) still stands and is unaffected by this rollback. Tomorrow: pick up Session C (telemetry).

- [x] [LL-057-C](tasks.md#LL-057-C) **LL-057 Session C — telemetry MVP, end-to-end (May 15).** Built all three layers of the telemetry pipeline per [firmware-spec §4.10](docs/firmware-spec.md): server (Cloudflare Worker), client UI (app + webapp toggles), firmware emission (`core/telemetry/`). End-to-end runtime verify is gated on [LL-076](tasks.md#LL-076) — the mirror's OTA partitions are refusing all installs from this morning's Session B bisect chain — but every layer compiled/typechecked clean independently and the Worker is deployable on its own.

  **1. Cloudflare Worker at `telemetry.layeredlogic.cc/v1/beacon`** ([cloudflare-workers/telemetry/](cloudflare-workers/telemetry/)). New TypeScript project; Wrangler-deployable. POST handler validates a versioned beacon schema (`v=1`, device_id 6-hex, fw_version, uptime_s, heap_free_min, boot_reason, rssi, led_count, optional panic block) — rejects garbage with 400, tolerates forward-compat additions silently. Storage: KV with `beacon:<id>:<unix_ms>` 90-day TTL + a no-TTL `latest:<id>` pointer for O(1) "is device alive?" lookups. Also exposes `GET /v1/healthz` (liveness probe) and `GET /v1/latest/<id>` (admin lookup). [README](cloudflare-workers/telemetry/README.md) documents Bill's first-time deploy steps (kv create, route, dns) + curl mock-beacon tests. Privacy: opt-in, pseudonymous device_id only, no IP retention, no auth on POST for V1 (revisit when paired HMAC lands in [LL-057-D](tasks.md#LL-057-D)). Worker `tsc --noEmit` clean.
  **2. App + webapp settings toggles.** "Share anonymous diagnostics" Switch on [App.tsx](App/v1/App.tsx) Settings page (RN `Switch`, copy explains what's collected + what isn't) + matching checkbox panel on the [webapp settings.tsx](Firmware/v1/webapp/src/pages/settings.tsx). Both wired through the existing `set_state {telemetry_enabled: bool}` op — no new wire op needed. The `telemetry_enabled` field has been in `ll_state_t` + `DeviceState` since [LL-029](tasks.md#LL-029); this just surfaces it. App `tsc --noEmit` shows the same 4 pre-existing errors in protocol.ts/ws-client.ts (DOM lib config, unrelated, predate this work).
  **3. Firmware `core/telemetry/` module** ([Firmware/v1/core/telemetry/](Firmware/v1/core/telemetry/)). Builds the beacon JSON via cJSON, POSTs via `esp_http_client` with TLS verification through the new embedded Mozilla CA bundle (`CONFIG_MBEDTLS_CERTIFICATE_BUNDLE=y` + `_DEFAULT_FULL=y` in [sdkconfig.defaults](Firmware/v1/sdkconfig.defaults)). Cadence: 24h base ± 2h jitter via `esp_random` — first fire 1-5 min after first `LL_EV_WIFI_CONNECTED`, then every 22-26h. Gated on `state.telemetry_enabled` at fire-time (so toggling off mid-cycle stops the next POST without resetting the schedule). Panic capture v0: `esp_reset_reason() == ESP_RST_PANIC` at init flags `g_panic_pending`, cleared after first successful beacon — V1 only includes the reset reason, full `filename:line:task_name` capture (per the spec) deferred to a separate task since it needs an `esp_set_panic_handler` hook. Wired into `variants/standard/main.c` after OTA subscribe, before the SoftAP kick. RSSI gracefully degrades to 0 when not in STA mode (Worker accepts the sentinel; UI can treat 0 as "unknown").
  **Build cost:** firmware grew from ~1.16 MB → **1.23 MB / 1.25 MB partition (98.2% utilization, 1.8% headroom)**. Vast majority is the embedded CA bundle (~70 KB compressed). Flagged for follow-up trimming: `CONFIG_MBEDTLS_CERTIFICATE_BUNDLE_DEFAULT_CMN` (CommonName-only bundle) would halve the cost; CA-pin to CF's specific roots would slim further; or expand the OTA slot size in partitions.csv (breaks OTA-from-old-firmware compat).
  **End-to-end verified on the live mirror later same day** (after [LL-076](tasks.md#LL-076) USB recovery, ~13:40 → ~13:43). Bill deployed the Worker on the new `layeredlogic.workers.dev` account-wide subdomain (took two tries — global "telemetry" was taken). Real beacon arrived at `/v1/latest/b2332c` ~100s after toggling telemetry on: `fw_version=telemetry-fix-1342, uptime_s=103, heap_free_min=163268, boot_reason="OTHER", rssi=-72, led_count=66`. Two real bugs caught + fixed during E2E:
  - **CF Bot Fight Mode rejects library-default User-Agents** (HTTP 403, CF error 1010). Added explicit `User-Agent: ll-mirror/1 esp32c3` in [telemetry.c](Firmware/v1/core/telemetry/telemetry.c)'s `post_beacon()`. **Important catch for future code paths** — any `esp_http_client` POST to a CF-fronted endpoint without a real UA will hit this. Flagged for the production OTA path when `ota.layeredlogic.cc` lands.
  - **`telemetry_enabled` was silently dropped by `op_set_state`** in [transport.c](Firmware/v1/core/transport/transport.c). The field is in `ll_state_t`, the event exists in state_bus, but the WS dispatcher had no branch — so the app/webapp toggle was a no-op. Added the missing branch posting `LL_EV_TELEMETRY`. Pure WS-layer bug, not state_bus or NVS.
  - (Polish) Expanded `reset_reason_str()` for IDF 5.x's added enum values (`ESP_RST_USB / JTAG / EFUSE / PWR_GLITCH / CPU_LOCKUP`), previously all caught by "OTHER". Mirror now correctly reports `boot_reason="USB"` after `idf.py flash` resets.

  Custom domain `telemetry.layeredlogic.cc` was added in the CF dashboard but DNS hadn't propagated to my dev PC during the E2E test (resolved fine on Bill's side). The verification used the workers.dev URL directly; the custom domain works the same way and will pick up automatically once DNS propagates everywhere. Final firmware on-device: `telemetry-final-1346`. **LL-076 closed** (mirror recovered via USB erase-flash + reflash, re-provisioned via SoftAP captive flow, back at same DHCP lease 192.168.5.229).

- [x] [LL-043](tasks.md#LL-043) [LL-043-1](tasks.md#LL-043-1) **Cold outreach campaign engaged + first batch sent (May 14).** [LL-043](tasks.md#LL-043) ("contact list + outreach") had been carrying a stale in-progress status since Apr 28 with the contact list itself never compiled; today consolidated the campaign artifact at [docs/outreach-list.md](docs/outreach-list.md) and sent 5 cold messages against the daily-cadence target Bill set mid-batch (5/day going forward). **Sends:** Reed Kleinman / Smart Home Solver (`reed@smarthomesolver.com`) — Lane A, strongest reply odds; Matt Perks / DIY Perks (`diyperks@gmail.com`) — Lane B, 4.9M-sub story-aligned long shot; Robert Tait / The Hook Up (`smarthomehookup@gmail.com`) — Lane A, found via site contact button; Lewis / Everything Smart Home (form at everythingsmarthome.co.uk/contact) — Lane A, direct competitor coverage; Joe Barnard / BPS.space (`joe@bps.space`) — founder-philosophy lane (not audience-fit), driven by personal resonance with his "afraid to toss old projects" + "personal engineering projects rant" videos. Prototype photo attached to first four; skipped for Joe (founder-philosophy ask, photo would read as pitch sneak-in). **Tone calibration locked** after the first two sends — Bill's actual edits to my drafts established the pattern: cut spec lists to one anchor concept, drop academic taxonomies (no want/need/cool/problematic framework), no LLC signature on cold mail, peer-tone not aspirant. Memory saved as [feedback_cold_outreach_drafts.md](.claude/projects/C--Users-bowhi-Desktop-Independent-Study/memory/feedback_cold_outreach_drafts.md) so future drafts default to the tighter style; cadence captured in [project_outreach_cadence.md](.claude/projects/C--Users-bowhi-Desktop-Independent-Study/memory/project_outreach_cadence.md). **Spun out [LL-043-1](tasks.md#LL-043-1)** for the content-creator branch (originally folded under LL-043 which was scoped to end-buyer + cafes); script variants (streamer / smart-home / maker / press), n8n automation outline, and verified-contact research captured in the same doc. **Name correction surfaced:** my earlier "TheBitWit (Kevin Kennedy)" suggestion was a confabulation — channel doesn't exist; removed from Lane C and replaced with Optimum Tech. **Tomorrow's queue:** TechHut (Brandon Hopkins, `brandon@techhut.tv`), Hardware Haven (`info@hardwarehaven.media`, weaker fit), bitluni (Twitter/Mastodon DM — no email), plus 2 more to hit the daily cadence target.

### In Progress

### Blocked

---

## Week 8 (May 19 – May 23): Sustainability Deep Dive & Legal

### Done

- [x] [LL-043-1](tasks.md#LL-043-1) **Cold outreach — Monday queue drafted + staged (May 20).** The 5-target queue staged email-verified on May 15 is now drafted, ready for Bill to review and send. Each draft is a per-recipient subject + body tuned to its lane: **Hackaday** (`tips@hackaday.com`, Lane D press tip-line, describe-don't-pitch), **iFixit** (`press@ifixit.com`, Lane E, repairability as the lead), **Tested** (`tips@tested.com`, Lane B/D, the solo-build-it-all maker story), **Strange Parts / Scotty Allen** (`scotty@strangeparts.com`, Lane B indie-founder, peer conversation ask), **Hardware Canucks / Dmitry** (`dmitry@hardwarecanucks.com`, Lane C, ambient-lighting-for-setups framing). All drafts staged in [outreach-list.md § Drafted](docs/outreach-list.md#drafted--ready-to-send-wed-may-20-batch). Tone per the outreach memories: one-sentence project description, no spec flexes, no academic want/need/cool framing, no LLC signature, no em dashes, subjects under 8 words. Hedge openers ("realize you probably get a lot of these") on the two creator contacts since there's no verified personalization to cite without risking a confabulated reference. The Variant 3 press template's "documented publicly at {repo}" line was dropped: the codebase is closed-binary (open-source-on-founder-exit), so there's no public repo to link; press contacts get an offer to send docs instead. **Wed May 20 is a valid send day** (Mon–Thu morning window per [feedback_outreach_timing](.claude/projects/C--Users-bowhi-Desktop-Independent-Study/memory/feedback_outreach_timing.md)); sends are pending Bill's review and not yet moved to the Sent table.

- [x] [LL-049](tasks.md#LL-049) **Cafe / showcase-partner contact-list scaffold + outreach script (May 20).** LL-049 (overdue, was May 16) had its interview outline ready since [LL-032](tasks.md#LL-032) but no contact list. Built the scaffold: [outreach-list.md Lane F](docs/outreach-list.md) went from a four-bullet approach to a fillable candidate table (cafe / neighborhood / shows-art-now / familiarity / reach-via / sent / status) with the 5-7-venue sourcing method and the per-conversation data targets spelled out. The named venues stay Bill's to fill from a local Maps walk-through — Seattle cafe names are local knowledge, and guessing them risks a wrong name (the TheBitWit-confabulation lesson from the May 14 batch). New **Variant 4** cafe / showcase-partner script: an in-person spoken opener as the default channel (walk in at a quiet hour, ask for the manager) plus an email / Instagram-DM fallback, both tuned to the owner/manager audience — the ask is "tell me how you decide who goes on the walls," not "cover this," and both keep an explicit "I'm not selling anything" because a stranger asking about wall space reads as a sales pitch by default. Deadline shifted May 16 → May 30 to match the [LL-048](tasks.md#LL-048) end-buyer interview window. The interviews themselves stay pending: Bill conducts them impromptu against the LL-032 outline once the venue list is filled.

- [x] [LL-056](tasks.md#LL-056) **Terms of Service & Warranty policy drafted (May 20).** New 13-section policy at [docs/terms-of-service-and-warranty.md](docs/terms-of-service-and-warranty.md): terms of sale (standard + the custom-order flow with the 50% deposit), a repair-first limited warranty with RMA process and the 7-year parts commitment, returns/refunds (30-day standard window; custom-order deposit forfeiture + proprietary-design scrap rule), closed-binary firmware terms, custom-design buyer-IP attestation, limitation of liability, privacy, and WA governing law. Ships as a **draft, not legal advice** — a banner flags that it needs review against WA consumer law / Magnuson-Moss / FTC guidance by counsel before going live. The three open items were confirmed with Bill the same day: `support@layeredlogic.cc` as the contact email, a 1-year-from-ship warranty (statutory consumer-protection periods overriding where the law mandates), and 50/50 custom-order payment (50% deposit at approval, 50% balance at shipment). All `[CONFIRM]` markers removed from the doc; counsel review is the only remaining gate.

- [x] [LL-077](tasks.md#LL-077) **Mirror Assembly & Teardown Guide written (May 20).** New task — spun out as the operations-track prerequisite LL-042 had been blocked on since Week 4 (the repair guide needs a teardown procedure, and no procedural build/teardown doc existed). [docs/assembly-guide.md](docs/assembly-guide.md) covers tools, the per-unit parts inventory, the three sub-assemblies (frame / LED / controller), the 20-station manufacturing sequence (S01–S20), final assembly, and §7 — the teardown/access procedure the repair guide consumes. Authored from the station-details CSV, the `basic_housing/` scripts, the repair-design-decisions matrix, and the BOM. Open items flagged: assembly times pending the golden-sample build; the housing model is still dimensioned for the old STM8 board.

- [x] [LL-042](tasks.md#LL-042) **User Repair Guide written (May 20).** [docs/user-repair-guide.md](docs/user-repair-guide.md) — customer-facing, first-person LL voice: a repair-first intro, tools/safety, a symptom-finder decision tree, per-component repair procedures covering all 17 failure modes, the recessed-button recovery reference, a parts-sourcing table, and the RMA/contact path. The §2/§3 teardown steps build on LL-077 §7. [repair-index.md](docs/repair-index.md) §6 placeholder replaced with a live link. Surfaced one open item — the front/back panel labels in [acrylic-crack-scratch.md](Failure_Modes/acrylic-crack-scratch.md) appear inverted vs. how an infinity mirror physically works; flagged for reconciliation.

- [x] [LL-057-D](tasks.md#LL-057-D) **Paired-mode auth — Sessions D1–D4 done (May 20).** LL-057's last session, staged D1–D4. Scoping doc skipped — [firmware-security.md §5](docs/firmware-security.md) already locks the design (pre-shared user secret, HMAC-SHA256 envelope, no QR/DH/WPS). **D1:** new `core/auth/` module — `auth_logic.c` (pure-C, host-buildable: SHA-256, HMAC-SHA256, hex, constant-time compare, and the `,"hmac":`-last envelope canonicalization), `auth.c` (`ll_auth` NVS namespace + RAM secret cache + verify), `CMakeLists.txt`, and `tests/core/auth/test_auth_logic.c`. 21 host tests (SHA-256 + RFC 4231 HMAC known-answer vectors + envelope round-trips) all pass; clean `-Wall -Wextra -Wpedantic -Werror` build. The SHA-256/HMAC are vendored pure-C rather than `mbedtls/md.h` so the crypto is host-testable and serves as the byte-exact reference for the app's JS HMAC. **D2:** `core/auth` wired into `variants/standard/main.c` (`ll_auth_init` + `ll_auth_subscribe`) + the variant CMakeLists (`auth` listed last so IDF's `nvs.h` doesn't shadow `core/nvs/nvs.h`). Built clean for esp32c3 (2% partition headroom) and OTA-flashed to the live mirror — `fw_version` `telemetry-final-1346`→`cec5bd3-dirty`, clean boot with no rollback, WS `get_state` green (`auth_mode=open`, uptime 188s). **D3:** the paired-mode auth gate landed in [`transport.c`](Firmware/v1/core/transport/transport.c)'s `handle_envelope()` — HMAC verify, then `ts`/`req_id` presence, then the replay checks, all skipped wholesale in open mode so the live mirror's existing behavior is byte-identical to pre-LL-057-D. New `set_auth_mode` (open↔paired, persists or clears the secret) and `rotate_secret` (old-secret-confirmed in-place change) wire ops. SNTP dropped per Bill's call — with no wall clock, the absolute ±60s `ts` window is replaced by a per-socket monotonic-`ts` guard (8 slots, reset on each WS handshake) plus a 32-entry device-wide `req_id` dedup ring; both run only in paired mode, after a valid HMAC. New `ll_auth_secret_matches()` in `core/auth/` backs the `rotate_secret` confirmation. Built esp32c3 — **1% partition headroom** (16.6 KB free; the LL-057-C telemetry CA bundle is the bulk, flagged for trimming before more features land) — OTA-flashed `d3auth-1349`, clean boot. Verified on the live mirror via new [`ll_auth_test.py`](Firmware/v1/scripts/ll_auth_test.py): **16/16 checks** — open-mode regression (gate dormant), gate (unsigned → `auth_required`, signed accepted, tampered HMAC → `bad_hmac`), replay (duplicate `req_id` and below-last `ts` both → `stale_ts`), `rotate_secret` (old secret stops verifying, wrong `old_secret` → `bad_payload`), and the authenticated unpair. One test-script bug caught mid-verify: the `rpc` helper read unsolicited `{"op":"state"}` broadcasts as responses, desyncing the request/response stream after every state-changing op — fixed by skipping broadcast frames (firmware was correct). [`firmware-security.md`](docs/firmware-security.md) §5.4 rewritten to the recency-based replay model, with the residual replay window stated honestly; [`control-protocol-spec.md`](docs/control-protocol-spec.md) §3.1/§8 updated to match. Mirror left in open mode. **D4:** app-side paired-mode support. New [`hmac.ts`](App/v1/src/hmac.ts) vendors pure-TS SHA-256 + HMAC-SHA256 — Hermes has no dependable WebCrypto and signing can't pull a native dependency. [`ws-client.ts`](App/v1/src/ws-client.ts) gained `setSecret()`, `hmac`-last frame signing (`frameFor()` — the signed region is the envelope JSON minus its closing brace, matching `auth_logic.c`), and the `setAuthMode` / `rotateSecret` ops. [`App.tsx`](App/v1/App.tsx) gained a Settings → Pairing section (require / change / remove a passphrase) and a controls-screen unlock block: a paired mirror the app holds no secret for rejects `get_state`, which flips a `needsSecret` flag and swaps the controls for a passphrase prompt. The secret is in-memory only — not persisted, so a paired mirror re-prompts after an app restart (flagged as a V1 limitation, same posture as the un-persisted mirror URL). `tsc --noEmit` clean save for the 4 pre-existing DOM-lib errors (`crypto` / `MessageEvent`) that predate this work. `hmac.ts` verified byte-exact against Node's `crypto` over 8 cases (SHA-256 KATs, a realistic envelope region, the >64-byte hashed-key path, a Unicode secret + payload) — and since the device matched Python's HMAC in D3 and Python == Node == FIPS, the app's signatures will verify on the mirror. Runtime UI verification (the pairing screens on a real Pixel 9) is deferred to Bill's next session, per the LL-057-A precedent. **LL-057-D is complete (D1–D4), and with it the LL-057 parent** — sessions A, C, D done; B (real-time OTA progress) stays deferred as architecturally blocked ([LL-057-B](tasks.md#LL-057-B), forward-compat scaffolding already shipped app-side). LL-057 landed May 20, inside the Week 8 window — the predicted slip past May 23 didn't happen. LL-057 closed.

- [x] [LL-078](tasks.md#LL-078) **Webapp paired-mode support (May 20).** The webapp counterpart to [LL-057-D](tasks.md#LL-057-D) D4. D4 gave the *mobile app* a pairing UI, but the device-hosted webapp had none and couldn't sign frames — so the moment a user enabled paired mode, the webapp locked itself out. Bill flagged it: he could see `auth_mode: open` in the webapp's diagnostics but had no control to change it. Mirrored the D4 work into [Firmware/v1/webapp/](Firmware/v1/webapp/): a new vendored [`hmac.ts`](Firmware/v1/webapp/src/hmac.ts) (pure-TS SHA-256/HMAC — the webapp is served over plain HTTP, not a secure context, so `crypto.subtle` is unavailable, the same kind of constraint Hermes imposes on the app side); `hmac`-last frame signing + `setAuthMode`/`rotateSecret` in [`ws-client.ts`](Firmware/v1/webapp/src/ws-client.ts); a pairing panel (require / change / remove a passphrase) in [`settings.tsx`](Firmware/v1/webapp/src/pages/settings.tsx); and a needs-secret unlock screen in [`app.tsx`](Firmware/v1/webapp/src/app.tsx). The webapp **persists the secret in `localStorage`** — a deliberate divergence from the app's in-memory-only secret: localStorage works over plain HTTP, and a webpage gets reloaded far more often than an app restarts, so re-prompting every load would be painful. Webapp built clean (`tsc -b` + vite, 13.9 KB gzipped), embedded into firmware **`webauth-1444`**, OTA-flashed to the live mirror at 1% partition headroom. **Browser-verified end-to-end** against the real device-hosted webapp: the pairing panel renders; clicking through require-a-passphrase flips the device to `auth_mode: paired`; a signed `set_state` (color → red) is accepted by the paired device's gate; and a full page reload re-authenticates transparently from the persisted secret with no re-prompt. The `remove passphrase` action uses `window.confirm` (the same pattern as the existing factory-reset button) — fine for a real user, but it blocks browser automation, so the unpair leg was confirmed at the protocol level and the mirror left in open mode. [`firmware-security.md`](docs/firmware-security.md) §5.4's "webapp doesn't sign — known limitation" note was replaced with the now-accurate both-clients-sign description. Tracked as new task [LL-078](tasks.md#LL-078).

- [x] [LL-079](tasks.md#LL-079) **Proto SoftAP fallback when no saved network is reachable (May 20).** Demo-blocker fix — Bill hit it in a test session: on an unexpected network with none of the mirror's saved Wi-Fi networks in range, the device sat in the connection state machine's backoff loop indefinitely (no SoftAP, no reachable surface), and with no recessed button on the C3 proto there was no factory-reset escape hatch either — the app couldn't find the device and nothing was demoable. [`provisioning.c`](Firmware/v1/core/provisioning/provisioning.c) now layers the open `LL-Mirror-<MAC>` SoftAP onto the still-running STA (APSTA) after the SM fails ~2 backoff cycles (`ensure_ap_fallback_up()`, ~30s): the device is reachable at 192.168.4.1 — drivable over the AP or re-provisionable from /setup — while the STA side keeps scanning and reconnects if a saved network reappears. A STA drop while APSTA is suppressed from the downstream "offline" signal so the AP-side HTTP server survives. Deliberately overrides the locked "RF minimal / no broadcast without a gesture" stance — **authorized by Bill as a proto-only stopgap**; V2 (ships with prod) gates AP fallback behind a button gesture. Built `demofix-1714` (clean esp32c3, 1% partition headroom; host suite 140/140). **Flashed + verified on the live mirror:** the WebSocket OTA path failed — `ESP_FAIL` inside `esp_https_ota` *after* a successful download (the same otadata symptom as [LL-076](tasks.md#LL-076)) — so it was recovered via USB `idf.py flash` to COM3, which also rewrites `ota_data_initial.bin` and clears the otadata state. Clean boot confirmed: `fw_version: demofix-1714`, `uptime_s` 68, `get_state` green, STA reconnected to "IoT". **AP fallback then verified live on the hardware** — with no reachable saved network the device broadcasts its SoftAP as designed.

- [x] [LL-080](tasks.md#LL-080) **Single-button factory-reset combo (May 20).** Companion to LL-079 — the C3 proto has no recessed button (`LL_PIN_BUTTON_RESET = -1`), so the recessed 10s-hold factory reset is physically unreachable and a locked-out device had no recovery gesture. New `factory_combo_step()` recognizer in [`button_logic.c`](Firmware/v1/core/button/button_logic.c): the deliberately unlikely sequence **5s hold → short press → 5s hold**, each step required within a 3s gap or the sequence resets. [`button.c`](Firmware/v1/core/button/button.c) feeds it the same primary-button edge stream as the existing gesture machine and posts `LL_EV_FACTORY_RESET` on completion — the same event the recessed hold posts, so the pattern_interp red/green confirmation cue and the provisioning teardown fire unchanged. Normal primary gestures are suppressed once the combo is past its first hold, so the middle tap and final hold don't fire stray power toggles / colour changes. 8 new host tests in [`test_gesture.c`](Firmware/v1/tests/core/button/test_gesture.c); full suite 140/140, clean `-Werror` build. Shipped in the same `demofix-1714` USB flash as LL-079 (disjoint subsystem); clean boot verified on silicon. **The combo was then verified live on the hardware** — the 5s-hold / short-press / 5s-hold sequence triggers the factory reset. Known gap: no in-progress LED cue during the two 5s holds (the recessed hold has a blue-blink progress cue) — acceptable for a dev/proto escape hatch, flagged for V2.

- [x] [LL-081](tasks.md#LL-081) **LED count board-default stamp (May 20).** Bug Bill caught right after verifying [LL-080](tasks.md#LL-080): the single-button factory reset, exercised for the first time on the dev mirror, left it reporting `led_count: 32` — the 6×6 production value, wrong for the 12×12 / 66-LED prototype. Root cause is pre-existing — `state_bus_defaults.c` hardcodes `.led_count = 32` (it's pure-C, can't see `board.h`), and a factory reset resets live state to those compiled defaults; the C3 proto simply never had a factory-reset path before LL-080 to surface it. Fix in [`state_bus.c`](Firmware/v1/core/state_bus/state_bus.c): a `stamp_board_led_count()` helper writes `led_count` from `LL_LED_COUNT_DEFAULT` (board header — 66 for `c3_devkit`) on every path that seeds or resets `g_state`, so the count is always the board's hardware value regardless of NVS or the pure-C defaults — which also self-corrects a device whose NVS holds a stale count. Shipped `ledfix-1833`, OTA-flashed (the OTA succeeded this time — the otadata reset by the prior USB flash cleared the earlier `ESP_FAIL`); **verified on hardware, `get_state` reports `led_count: 66`.** Should have been caught when LL-080 landed — building a factory-reset trigger without checking the post-reset state on this board was the miss.

### In Progress

### Blocked

---

## Week 9 (May 26 – May 30): Marketing Storytelling & Assets

### Done

- [x] [LL-082](tasks.md#LL-082) **IM_SVG_Maker — custom-mirror fab-file generator landed (May 26).** New Python CLI at [Assembly_docs/IM_SVG_Maker/](Assembly_docs/IM_SVG_Maker/) that turns a monochrome black SVG (or a raster line-art image via the included potracer preprocessor) into the four fabrication files for one Kintsugi-style mirror tile: `laser.svg` + `laser.dxf` for the 150×150 mm acrylic cut (red-hairline stroke convention), and `plug.3mf` + `plug.stl` for the two-layer clear-PETG plug (3 mm inset that drops flush into the laser cutout, 1 mm base behind the mirror that bridges every island into one supporting piece). Pipeline is `svgelements → shapely → trimesh` with `manifold3d` for the union; all tunables in [variables.json](Assembly_docs/IM_SVG_Maker/variables.json). Architecture, geometry math, and every non-obvious decision are documented in [Assembly_docs/IM_SVG_Maker/PLAN.md](Assembly_docs/IM_SVG_Maker/PLAN.md) (kerf-as-mm-offset-not-scale, round joins everywhere, nozzle rounding via open-then-close, the `max(min + (N-1)*per_island, bridge_factor * gap/2)` base-offset formula). Demo runs on `demo_W_black.svg` (W extracted from the Washington Huskies halo) and on `fox.jpg` via the raster preprocessor both produce clean output — confirmed by [cut_lines_preview.png](Assembly_docs/IM_SVG_Maker/cut_lines_preview.png) and [fox_preview.png](Assembly_docs/IM_SVG_Maker/fox_preview.png); Bill confirmed the fox case looks correct in both the preview *and* the rendered STL, and the tool runs without a virtual environment (plain `pip install -e .` is sufficient).
  - **Position in the ordering / assembly flow.** This is the geometry-engine half of the custom-manufacturing track that runs parallel to the [LL-051](tasks.md#LL-051) packaging dielines. Intended user-facing pipeline: a customer arrives at **billwhite.me/infinity**, tests their logo against a live preview on the site, the site exports the agreed black SVG straight into IM_SVG_Maker, and the tool emits the four fab files into `out/<order>/`. Downstream the same per-order package can hand off to (a) the 3D printer queue (3MF straight into the slicer or a Bambu/Prusa farm API), (b) the laser controller (DXF or SVG into LightBurn / job queue), and eventually (c) the LL-051 packaging dieline generator parameterised on the order's mirror dimensions — so a single customer SVG fans out into laser job + print job + branded mailer dieline with zero per-order CAD work. Same automation pattern as the packaging side: parametric generators feeding queueable machine jobs from a single canonical input. The pipeline maps onto service-blueprint Stage 2b (custom consult) and Stage 4 (Manufacture & QC) cleanly.
  - **Same-day extensions:** rolled the two parked follow-ups into this session.
    - **Size-floor thresholds in the raster preprocessor.** New `raster_min_island_area_mm2` and `raster_min_feature_width_mm` in [variables.json](Assembly_docs/IM_SVG_Maker/variables.json), surfaced as `--min-island-area-mm2` / `--min-feature-width-mm` CLI flags on [scripts/raster_to_black_svg.py](Assembly_docs/IM_SVG_Maker/scripts/raster_to_black_svg.py). Default 0 = disabled, so existing runs are byte-identical. Decided to put these in the raster preprocessor (not the main pipeline) because that's where speckles and hairline-thin geometry actually enter the system — a hand-authored or color-extracted black SVG is already clean. First implementation tried "morphologically open everything below width" (erode then dilate); on the fox at width=2.5mm this *fractured* the islands at every thin neck and the count went 5 → 34 — the opposite of "drop thin junk." Switched to erosion-as-predicate: `island.buffer(-w/2)` empty → drop the whole island; otherwise keep the *unmodified* island. Clean drop-or-keep, no reshaping, no fracturing. Verified on fox.jpg: area floor of 20mm² drops 2 of 5 islands, width floor of 5mm wipes everything (the fox is all line work), the filtered SVG re-parses through the main pipeline (`load_cut_polygon`) cleanly. PLAN.md Alternatives section flipped from parked to done, plus a Learnings entry for the opening-vs-erosion call.
    - **Color-SVG → black-SVG converter.** New [im_svg_maker/color_select.py](Assembly_docs/IM_SVG_Maker/im_svg_maker/color_select.py) + CLI wrapper [scripts/color_svg_to_black.py](Assembly_docs/IM_SVG_Maker/scripts/color_svg_to_black.py). Originally framed as "out of scope here — that lives at billwhite.me/infinity," but a CLI version is exactly what the on-site tool will eventually wrap, and it's needed to push *existing* multi-color logos through the pipeline today without hand-recoloring. Uses svgelements' `SVG.parse(..., reify=True)` for CSS / inheritance / transform-resolved fill matching — solid fills only (gradients and `fill="none"` strokes are skipped, deliberately, as the "which color is the cut" UX problem only has a clean answer for solids). Two modes: list (no `--color`) prints distinct fills with element count + summed bbox area ranked by visual presence; extract (`--color "#hex"`, repeatable, with `--tolerance N` for fuzzy matching and `--invert` to drop a background) emits a flat black SVG with one `<path fill="#000000" fill-rule="evenodd"/>` per kept element, in the exact format `svg_parse.py` already reads via XOR. **End-to-end verification on `Washington_Huskies_logo.svg`:** list mode finds the two known fills (`#E8D3A2` gold halo, `#33006F` purple W) ranked by bbox area; `--color "#E8D3A2"` extracts the gold and the full pipeline produces a 100×68.88mm 1-island plug (matching the hand-extracted `demo_W_black.svg` baseline). Multi-color union (`--color "#E8D3A2" --color "#33006F"`) also produces a valid plug. Caught and fixed two small bugs during verification: a `≠` glyph in the CLI's "kept" status line crashed Windows cp1252 stdout (swapped to ASCII `NOT matching` / `matching` wording), and `pyproject.toml` was missing `potracer` + `Pillow` from `dependencies` even though `raster.py` imports both — added both.
  - **Repo state:** still untracked in git as of session end. Memory note at [project_im_svg_maker.md](.claude/projects/C--Users-bowhi-Desktop-Independent-Study/memory/project_im_svg_maker.md) updated to reflect the new color-tool surface and the printer/laser-queue handoff remaining as the only major parked follow-up.

- [x] [LL-083](tasks.md#LL-083) **Visualizer-port — chunk 1 of 6 (May 26): scoping doc + parity harness landed (red baseline).** Bill asked whether the IM_SVG_Maker preprocessing could land inside the existing [infinity_mirror_visualizer](https://github.com/bowbikes/infinity_mirror_visualizer) so users can upload a JPG (the format they actually have) instead of needing a pre-prepped SVG, with the 3D preview reflecting the *manufacturable* art (post-binarize, post-trace, post-size-floor, post-nozzle-round). Spun this out as its own multi-chunk task ([LL-083](tasks.md#LL-083)) with the full scoping doc in [Assembly_docs/IM_SVG_Maker/INTEGRATION_PLAN.md](Assembly_docs/IM_SVG_Maker/INTEGRATION_PLAN.md): boundary (JS port covers binarize/dilate/trace/color-pick/size-floors/nozzle-round; Python stays canonical for kerf/inset/base/extrude/laser-export, run at order time on Bill's machine), library choices (`potrace.js` for the same potracer algorithm family; `clipper-lib` for the exact `shapely.buffer(round_join)` equivalent; Canvas `ImageData` for binarize+dilate; Three.js `SVGLoader` already in the repo for path sampling; DOM `getComputedStyle` for fill resolution — no new lib needed there since the browser does CSS/inheritance natively), and a six-chunk plan each independently shippable.
  - **Chunk 1 — JS module skeleton + parity harness — done same day.**
    - **IM_SVG_Maker side (Independent_Study repo):** new [tests/fixtures/](Assembly_docs/IM_SVG_Maker/tests/fixtures/) with the 3 existing fixtures copied in (W, fox, Huskies); new [tools/regenerate_canonicals.py](Assembly_docs/IM_SVG_Maker/tools/regenerate_canonicals.py) runs the Python pipeline on each fixture and writes a sibling `.canonical.svg` (passthrough for already-black SVGs; raster pipeline for JPGs; color_select w/ `#E8D3A2` for the Huskies extract). Three canonicals generated cleanly (`5 islands, -0 thin, -0 small` for fox; `1 path kept` for Huskies; passthrough for the W).
    - **Visualizer side (separate `infinity_mirror_visualizer` repo, on Desktop):** added [`vitest`, `jsdom`, `clipper-lib`, `potrace`] to package.json (vitest as dev; the rest are runtime); enabled vitest in `vite.config.js` with `environment: 'jsdom'`; created `src/preprocess/{index,raster,colorSelect,manufacturability}.js` as pass-through stubs with API surfaces and JSDoc-typed signatures that match the Python CLI entries one-to-one (each carries an explicit `STATUS: chunk N stub` and `TODO chunk N: ...` markers for the upcoming work); created `scripts/sync-fixtures.mjs` that copies from `../Independent_Study/Assembly_docs/IM_SVG_Maker/tests/fixtures/` into `src/preprocess/__tests__/fixtures/` (no submodule, plain copy; `IM_SVG_MAKER_PATH` env var overrides the source path); created [src/preprocess/__tests__/parity.test.js](https://github.com/bowbikes/infinity_mirror_visualizer) with four metrics per fixture (existence, island count, total area within 2%, viewBox within 0.5mm) plus a `.todo` for the symmetric-difference check (chunk 5) and three `.todo` placeholders for the future-chunk fixtures (tiny_specks, hairline, nested_holes).
    - **`npm install` ran cleanly** (192 packages added, 11 vulns flagged by audit — punted, not blocking). `npm run sync-fixtures` copied the 6 files in. **`npm test` reports the intended red baseline: 5 failed / 7 passed / 6 todo across 18 tests.** Failures all carry concrete diff messages (`island count drift (actual=0 vs canonical=5)`, `area drift 100.0% (actual=0.0 vs canonical=2005200.1)`, `viewBox drift dw=1900 dh=1900 (actual={"x":0,"y":0,"w":100,"h":100} vs canonical={"x":0,"y":0,"w":2000,"h":2000})`). Passes are the three existence checks + the four self-passthrough demo_W_black checks (the passthrough stub trivially matches its own canonical). Todos are the symmetric-difference metric per fixture (chunk 5) and the three new fixtures (chunks 3 + 5).
  - **What this unlocks.** Chunk 2 (port `color_select.py`) is the next chunk; it'll turn the two Huskies failures green via DOM walk + `getComputedStyle(el).fill` matching — no math libs, mostly an XML walk, easiest of the modules. Then chunk 3 svg_parse helpers via Three.js SVGLoader, chunk 4 raster via potrace.js + Canvas, chunk 5 size-floors + nozzle-rounding via Clipper.js (closes all `.todo`s), chunk 6 UI wire-up.
  - **Repo state.** Both repos still untracked at session end. Independent_Study has new untracked: `Assembly_docs/IM_SVG_Maker/tests/`, `tools/regenerate_canonicals.py`, `INTEGRATION_PLAN.md`, plus the modified tasks.md/sprint_log.md/task_log.md from chunk 1's record-keeping pass. The sibling visualizer repo has modified package.json, vite.config.js + new package-lock.json + new `src/preprocess/`, `scripts/`, and the fixtures-mirror directory. Bill hasn't asked for either commit yet.

- [x] [LL-083](tasks.md#LL-083) **Visualizer-port — chunks 2-6 of 6, end-to-end (May 26 same session).** Continued the cross-repo work from the chunk-1 entry above and landed the remaining five chunks back-to-back. Each chunk leaves the unit-test suite green; final count is 37/37 active tests, zero todos, zero failures.
  - **Chunk 2 — `color_select.py` → `colorSelect.js`.** DOM walk + manual SVG-spec fill inheritance (inline `style` > attribute > parent inheritance > `#000000` default; `getComputedStyle` doesn't reliably resolve SVG fill under jsdom). Transform composition: leaf→root walk, reversed + joined as an SVG transform string, fed to `svgpath.transform()` (avoided `DOMMatrix` because jsdom doesn't ship it). Shape support for `<path>`, `<rect>`, `<circle>`, `<ellipse>`, `<polygon>`, `<polyline>` — each converts to a d-string before transform-baking. CSS Color Module Level 3 named-color table inlined (~150 entries) so no extra dep. New `svgpath` dep. Also fixed the parity test's `approxPathBboxArea` helper from "match every number in d-string" (broken — relative-command deltas lie about extent) to a proper endpoint-only walk via `SvgPath.abs().iterate()`. **Result:** all 4 Huskies tests green; counts went 5/7/6 → 3/9/6.
  - **Chunk 3 — `svg_parse.py` → `svgParse.js`.** Hybrid: Three.js `SVGLoader` does the curve flattening, clipper-lib's `pftEvenOdd` does the XOR/shell-hole-assembly (replaces Python's `shapely.symmetric_difference`). Three.js's `path.toShapes(false)` uses winding-direction heuristics rather than pure evenodd; using clipper-lib for the XOR gives byte-faithful parity on nested holes. New `nested_holes.svg` fixture (concentric arcs) — Python and JS both yield 2 islands (big disc-with-hole + inner solid disc) with theoretical areas matching within Bézier-sampling tolerance. Inverse helper `polygonsToSvg` round-trips polygons → SVG → polygons preserving structure. New `svgParse.test.js` covers W, nested_holes, Huskies-canonical, viewBox preservation, empty SVG handling, ring/polygon area helpers. **Result:** counts 3/9/6 → 3/18/6 (fox still red, chunk-4 territory).
  - **Chunk 4 — `raster.py` → `raster.js`.** Pipeline: Jimp grayscales + thresholds (`threshold({max})` matches Python's `arr < threshold`); a hand-rolled min-filter dilation (`dilateForeground`) spreads black pixels by `thicknessMm * pixelsPerMm` (foreground=0/background=255 means morphological dilation = min-filter, mirroring PIL's `MaxFilter` on the inverted binary); post-dilate bitmap re-serialized to PNG and passed to the npm `potrace` package (which can't consume Jimp instances directly — needs Buffer); potrace's single-`<path>`-many-subpaths output flows through `svgParse` for shell/hole assembly; `polygonsToSvg` re-emits one `<path>` per island matching `fox.canonical.svg`. Switched test input from broken jsdom `Blob` to `Uint8Array` (jsdom v24's Blob is missing `arrayBuffer()`/`stream()`); production `toBuffer()` covers Buffer / ArrayBuffer / Uint8Array / Blob / File. New `jimp` dep (explicit; was transitive). **Result:** all 3 fox tests green; counts 3/18/6 → 0/21/6.
  - **Chunk 5 — size floors + nozzle rounding → `manufacturability.js`.** Clipper-lib `ClipperOffset` with round joins = the `shapely.buffer(d, join_style='round')` equivalent. Order mirrors Python: nozzle round (open-then-close, `cut.buffer(-r).buffer(+r).buffer(+r).buffer(-r)`) → width floor (erosion-as-predicate, drop polygons whose `buffer(-w/2)` is empty — matches the May-26 IM_SVG_Maker decision) → area floor (`polygonArea < threshold`). All thresholds operate in SVG-unit space converted from mm via `longestSide / maxLogoDimMm` (matching `pixels_per_mm` in raster.py). Added `tiny_specks.svg` + `hairline.svg` fixtures. New `manufacturability.test.js` with 10 focused tests (area floor drops 4 specks but keeps the square, width floor drops the hairline but keeps the square, nozzle adds vertices to rounded square, threshold composition + warnings + idempotence). Symmetric-difference metric implemented in parity test via clipper-lib `ctXor`; tolerance set at **35% regression bound** (not strict-match — Python `svgelements` applies an implicit viewport-to-viewBox transform on top of the explicit matrix while JS `svgpath` bakes only the explicit; Python `potracer` vs npm `potrace` produce different vector approximations of the same binarized pixels; algorithm correctness is verified by the focused unit tests). The 3 future-chunk fixtures get passthrough parity checks instead of `.todo`s. **Result: 0 failed / 37 passed / 0 todo.** The full preprocessing pipeline is feature-complete.
  - **Chunk 6 — UI wire-up.** New [PreprocessPanel.jsx](https://github.com/bowbikes/infinity_mirror_visualizer) — self-contained section component the visualizer's `App.jsx` injects into `ControlsPanel` via a new `topSection` prop (less invasive than splitting the sidebar into two scrolling panels; ControlsPanel keeps its own panel chrome). State machine has three stops — `idle` (no file), `picking` (multi-color SVG awaiting color selection), `ready` (preprocessing complete; sliders re-run `applyManufacturability` against a cached intermediate SVG without re-tracing). File input accepts `.jpg/.jpeg/.png/.svg`; the dispatch branches: JPG → `preprocessRaster`; multi-fill SVG → `listColors` + color-swatch grid + `selectByColor` on pick; single-fill SVG → passthrough; all land in the intermediate. Threshold sliders: nozzle diameter (0–2mm), min island area (0–200 mm²), min feature width (0–5mm), max logo dim (50–150mm). Warnings + drop counts render inline. `npm run build` passes (1003 modules transformed in 5.83s; bundle ~713 KB gzipped). 37/37 unit tests still green after the UI work.
  - **Open follow-up — browser-runtime potrace verification.** Vite logs `module externalized for browser compatibility` warnings for `util`/`stream`/`fs`/`zlib`/`assert` imported by `potrace`'s transitive deps (`pngjs`, `gifwrap`, `strtok3`). The build doesn't fail but the JPG-trace path may hit a runtime stub in the browser. **Needs Bill to run `npm run dev`, upload a JPG, and confirm the trace produces a black SVG end-to-end.** If it breaks, the fix is either a vite Node-polyfill plugin (e.g. `vite-plugin-node-polyfills`) or swapping `potrace` for the pure-JS `potracer` package. Color-pick and manufacturability paths don't use potrace and should work regardless.
  - **What's next.** All six chunks of [LL-083](tasks.md#LL-083) are done. The remaining post-port follow-ups recorded in [INTEGRATION_PLAN.md](Assembly_docs/IM_SVG_Maker/INTEGRATION_PLAN.md): Netlify → Vercel migration (separate task; standard Vite preset, repoint Cloudflare DNS) and the new UX modes Bill mentioned (pending his enumeration so we can sanity-check module boundaries). Both repos still untracked in git at session end.

- [x] [LL-084](tasks.md#LL-084) **Visualizer cleanup pass + post-port bug fixes (May 26–27).** Continuation work after [LL-083](tasks.md#LL-083) shipped to Vercel. Bill asked for a broad code review of the visualizer; spun out 19 small tracked work items (some quick wins, some non-trivial perf/correctness), then iterated through several rounds of bug-fix pushes informed by what he saw live on the deploy. Final state: dog / cold-snowflake / cage / space-needle torture-tests all render correctly through the preprocessing pipeline; tests stayed 37/37 the whole way through; the Vercel deploy now serves the cleaned-up bundle from `main`.

  **Headline correctness wins** (each shipped as its own small commit):
  - **The merge-step bug in `SvgIcon`** that mattered most. `THREE.ShapeGeometry` produces INDEXED triangle buffers; the merge step concatenated `.position` arrays without expanding or remapping the indices, so every multi-island custom SVG (dog ring, snowflake, anything past one path) rendered as a garbage triangle salad. This was the cyan-triangle-spike artifact Bill kept seeing. Fix expands each indexed geometry into a flat triangle list before concatenating; single-geometry case still short-circuits.
  - **`SvgIcon` swapped from Three.js `path.toShapes(false)` to our `parseSvgToPolygons`** (clipper-lib `pftEvenOdd` XOR). Three.js's `toShapes` uses winding-direction heuristics that fail on multi-subpath SVGs whose author didn't follow the heuristic — dog and Huskies-halo–shaped art rendered as filled silhouettes instead of as rings. clipper XOR is winding-independent, so the outer+holes structure is correct.
  - **`listColors` default fill** changed from `#000000` to `null`. The snowflake's `fill:none` was declared via a `<style>` CSS class (`.cls-1`); my DOM-walk `resolveFill` didn't parse `<style>` blocks, so it fell through to the SVG spec default of `#000000` and reported the snowflake as a single-fill SVG, which routed it to fill passthrough where its stroke-only polylines became degenerate triangles. Null-fill SVGs now route through `strokesToBlackSvg` (vector stroke-to-fill via Clipper `etOpenRound`, preserving the source 1.92px stroke widths exactly) as intended.
  - **Browser-runtime fixes for the JPG-trace path.** Vite was externalizing potrace's transitive deps' Node modules to empty stubs (`util`/`stream`/`fs`/`zlib`/`assert`), so preprocessing died silently. Added `vite-plugin-node-polyfills` (scoped to non-test mode so vitest still uses real Node `path`/`fs` for fixture loading), plus a `define: { __dirname, __filename }` stub for the CJS globals the polyfill plugin doesn't synthesize. Build now emits zero externalization warnings; JPG and stroke-only-SVG paths actually run in the browser.

  **Security honesty.** Removed the client-side "cryptographic signature for tamper detection" theater in `exportUtils.js` — the hardcoded `INFINITY_MIRROR_V1` secret was baked into the JS bundle, so anyone with the page could re-sign any modified config. Swapped for a SHA-256 integrity checksum and corrected the copy in ExportModal + the export README ("catches accidental corruption, not tampering"). `validateImportedConfig` accepts legacy `signature` field name for back-compat. Manufacturer endpoint moved from a hardcoded placeholder URL to `import.meta.env.VITE_MANUFACTURER_ENDPOINT`; when unset, ExportModal hides the "Send to manufacturer" radio entirely so production can't silently POST to a fake endpoint.

  **UX cleanup.** Render mode collapsed from three (fill / outline / stroke) to one (flat fill matching the laser cut). Custom Art preprocessing panel gated on preset = "Custom Upload" so there's never both an unrelated upload box AND the preset dropdown visible at once; renders directly under the Icon section. File-input label replaced with a styled `<label>` + hidden input — the native "No file chosen" never appears, the label always shows the actual current filename. `mirrorSpacing` state renamed to `frameDepthMm` across App / ControlsPanel / Scene / Box / exportUtils so the state variable matches the user-visible slider label. Deleted a lot of dead files (empty `visualizer.js`, `test_svgs/`, `test-heart.svg`, `verify-export.html`, three overlapping doc files).

  **Performance.** Module-level SVG parse cache in `SvgIcon` so the N reflection layers each pay one parse cost, not N. `THREE.Color` scratch reuse in `ReflectionLayers` (was allocating per layer per render). `frameBounds` array stabilized via `useMemo`; per-layer `localFrameBounds` baked into the layer memo; SvgIcon wrapped in `React.memo` — camera-tick re-renders no longer rebuild geometry. Preprocessing chunk lazy-loaded via dynamic `import()` in PreprocessPanel — initial gzipped bundle dropped from **713 KB → 331 KB** for visitors who only browse the presets. SvgIcon dropped from 634 → ~330 lines (clip helpers + emissive intensity extracted to `src/utils/`).

  **Validation workflow.** Wired up the `mcp__Claude_Preview__*` browser-automation tools against the local dev server. Switched from "push and hope" to "spin up the local preview, programmatically inject each torture-test SVG via DataTransfer, screenshot, compare to expected, only push when renders match." Caught two of the three rendering bugs above this way before they shipped. The local-validation contract carries forward to [LL-085](tasks.md#LL-085).

  **Hosting moved to Vercel.** Bill set up the project pointing at `bowbikes/infinity_mirror_visualizer` main. Merged `bug_fixes` → `main` so production deploys carry the cleanup. Both branches kept in sync throughout; tests 37/37; build always clean.

  **Deferred.** `Rainier.svg` (an Inkscape mountain illustration: 1 path, 61 subpaths) produces ~348K triangles after evenodd XOR + triangulation; ShapeGeometry / earcut handles each polygon individually but at this density the renderer outputs visible dots rather than a solid fill. Polygon simplification (Douglas-Peucker or clipper's `CleanPolygons`) before triangulation would fix it. Bill called Rainier "the REAL torture test" and explicitly deferred. Not in scope of LL-084.

- [x] [LL-085](tasks.md#LL-085) **Visualizer controls UX pass — 16 commits, sidebar reworked top-to-bottom (May 27).** Opened with a survey of `ControlsPanel.jsx` + `PreprocessPanel.jsx` and a four-tier prioritized list (polish → PreprocessPanel collapse/debounce → modal wizard / presets / mobile drawer → small polish items); Bill picked tier 1, most of tier 2, all of tier 4. After those shipped he greenlit the big tier-3 items too, plus a couple of his own asks that surfaced from using the result.

  **Validation workflow held end-to-end.** Same `mcp__Claude_Preview__*` loop as LL-084: dev server live, programmatic DOM interaction, snapshot text + behavioral asserts, only push when the assertion passes. Tests stayed 37/37 through every commit; `npm run build` always clean. `main` and `bug_fixes` kept in sync via `git push home_pc <branch>` + ff-only merge per the established pattern.

  **Manufacturability + Custom Art tuning (Bill's specific asks):**
  - **f71a377** — Nozzle diameter became a six-button discrete picker `[off, 0.25, 0.40, 0.60, 0.80, 1.00]`. Min island area default = ⌈π·(d/2)² × 10⌉/10 mm². Min feature width default = nozzle diameter. Both follow the nozzle chip until the user moves them, at which point the override sticks. Yellow "the finished product will not be as fine as the rendered preview" warning under any threshold set to zero. `maxLogoDimMm` slider removed.
  - **d5ae16a** — **Edge Thickness now actually does something for custom SVGs** (it was previously dead for uploads — only affected preset shapes). The slider dilates the parsed polygons by `edgeThickness / 2` in scene-space via `offsetPolygons` (promoted from internal to a public preprocess export). Thin lines get thicker, solid shapes grow outward. Slider min lowered from 0.05 → 0. Thumbnail got a Hide/Show toggle.
  - **d396772** — Edge Thickness step 0.05 → 0.01 (finer dial-in); Edge Thickness × Scale interaction deliberately kept proportional (matches manufacturing reality: scaling up the cut makes the cut lines physically thicker); Frame Depth label respects the unit toggle (was always `mm` regardless of in/mm); Bloom Effect toggle moved out of the floating canvas overlay into Frame Controls next to Auto-orbit.

  **Tier 1 polish (4cf258d):** `Reset all` button at the top of the panel (snaps every control to DEFAULTS; custom-art uploads preserved); double-click any slider's label to reset just that slider; numeric input next to every slider (clamps to [min, max] on commit); Units chooser became a `mm | in` button toggle; hex color text inputs validate on blur with a red border on bad input.

  **Tier 2 PreprocessPanel (4851556):** Manufacturability tuners moved behind a default-closed `▸ Advanced (manufacturability)` toggle so the basic flow is upload → done. 150ms debounce on the manufacturability re-run effect (was running the full Clipper pipeline on every slider tick — instantly visible lag on dense art). Inline thumbnail of the processed black SVG at the top of the ready stage.

  **URL hash + named presets:**
  - **1907b91** — All config knobs serialize to `window.location.hash` as `#cfg=<base64-json>` via `history.replaceState` (no Back-button pollution). Restored once on mount via the `useState` lazy initializer so the encode-on-change effect can't clobber the inbound hash with default state. `Copy share link` button in the Export section flashes "Link copied!" for 1.5s.
  - **635e368** — `PresetsSection` at the top of the panel: inline naming input → saves the current `SHARED_KEYS` snapshot into `localStorage["imv:presets"]` as `{name, cfg, savedAt}[]`. Saved presets shown as name buttons with × delete affordances. Same-name save overwrites. Custom-art SVGs intentionally NOT included (too big to fit in a hash or preset, fast to re-upload).

  **Mobile drawer (ce05461):** `ControlsLayout.css` handles the responsive layout. Above 900px the panel is a normal 320px flex child (existing desktop layout); below 900px it becomes a fixed-position drawer pinned to the right edge, translated offscreen by default. Hamburger button in the top-right toggles. Dark scrim overlay with tap-to-close.

  **Tier 4 polish (b451db4):** Multi-color picker (toggle swatches with a ✓ marker, then `Apply (N colors)` button — single-tap-and-go was lossy for art whose cut spans several near-black fills). Auto-orbit checkbox folded into Frame Controls. Export note rewritten to "Bundles the configuration with a SHA-256 integrity hash for the manufacturer to verify against." Edge Thickness moved under a new "Appearance" subsection inside Icon Transform.

  **Custom Art modal wizard (840a8e0).** The crown jewel of this session. Pulled the upload + color-pick + manufacturability flow out of the sidebar into a `CustomArtModal` that wraps `PreprocessPanel`. Picking Custom Upload from the preset dropdown auto-opens the modal on the first pick. Sidebar gets a compact summary card (64x64 thumbnail + filename + Edit button) when art is uploaded, or a single "Upload custom art…" CTA when not. Modal stays mounted after first open (hidden via `display:none` while closed) so `PreprocessPanel`'s internal state — file, picked colors, slider positions, Advanced collapse — survives close+reopen. Hitting Edit puts the user back exactly where they left off without re-uploading.

  **Light + emission perceptual uniformity (Bill's biggest single ask):**
  - **8a46e4e** — Preload preprocess module on `PreprocessPanel` mount (was lazy on first file upload — moving it earlier lets the ~200 KB-gzipped import happen while the user is in the OS file picker). `Canvas frameloop="never"` while the Custom Art modal is open (Three.js continuous rendering was eating enough main-thread time that the OS file dialog lagged after clicking Choose file — a small but real issue Bill noticed). Preview caption text fixed to "black = illuminated segments, white = mirror base."
  - **a382470** — `Light Intensity` slider (0–3×, default 1.0, step 0.05) threads through Scene → Box → ReflectionLayers → SvgIcon and multiplies the per-hue emissive intensity. Joins the URL hash / presets / Reset all.
  - **8a8a08f** — **Replaced the six-constant hand-tuned Gaussian curve with a principled inverse-luminance formula** `emission = BASELINE / intrinsic_luminance^POWER` (POWER=1.0 gives mathematically exact perceived uniformity across the entire hue circle; BASELINE=3.4 tuned so default cyan emission matches the previous curve's output). Every hue lands at perceived=3.40 under this formula.

    Tried first to do the per-hue uniformity measurement programmatically — enabled `preserveDrawingBuffer: true` on the GL context, then iterated 64 hues, read canvas pixels, compute Rec.709 luminance — but the headless preview's `requestAnimationFrame` appears paused so the canvas readback returns whatever was last manually drawn (cleared red from my test), not Three.js's rendered output. After confirming this is a fundamental headless-mode limitation, switched strategies: derived the formula from first principles (inverse-luminance compensation with Rec.709 weights). Documented this in the commit message so the assumption is explicit. Visual verification by Bill in a real browser is the missing step.
  - **b739ebb** — Default `lightIntensity` 1.0 → 0.5 (the new uniform formula lands brighter than the old hand-tuned curve under bloom; 0.5 gives the previous overall feel as the baseline; slider still goes to 3.0).

  **Brand corner (f61a57b, 9b7ecaa):** `InfoPopover` pinned top-left with one-paragraph description + four-bullet how-to + "Built by Layered Logic — light that layers." footer linking to layeredlogic.cc. Italic Berkeley Mono per [`project_brand_locked_decisions.md`](https://github.com/bowbikes/Independent_Study/tree/master) brand decisions. Dismissable, closed state collapses to a small ⓘ button, dismissal sticky via `localStorage["imv:info-dismissed"]`. The initial Unicode ⓘ glyph rendered as a low-res emoji bitmap on Bill's machine; swapped for a hand-drawn inline SVG (outer circle + vertical stem + dot) — vector now, sharp at any DPR.

  **Stale-dev-server gotcha worth recording.** While testing the InfoPopover SVG-icon fix the dev server got into a state where Vite was serving a stale `App.jsx` without my `InfoPopover` import despite the on-disk file having it. `npm run build` was clean (proving it wasn't a code issue); `fetch('/src/App.jsx')` from the running page returned the old content. Resolved by `preview_stop` + `preview_start`. If this recurs, check the Vite cache first.

  **Notes carried forward for future iterations** (not in scope here): Bill should visually verify the emission uniformity by scrubbing hues with Bloom on; if bloom over-amplifies bright hues in practice, bump `POWER` above 1.0 (or expose it as a slider). The inverse-luminance formula and the Light Intensity slider give the right tunables.

### In Progress

### Blocked

---

## Week 10 (Jun 2 – Jun 6): Portfolio Construction

### Done

- [x] [LL-086](tasks.md#LL-086) **IM_SVG_Maker batch sheet-nesting + new input preprocessors (Jun 4).** Turned the single-tile fab engine into a batch-order workflow that maximizes each physical cut sheet: `tile_sheet.py` nests four `laser.dxf` tiles into a 2×2 grid on one 300×300 mm acrylic sheet (per-tile layers, `--gap`/`--sheet` params, `--squares-only` mode for blank frames, footprint-overhang warning). Processed two new logos for the first real multi-logo sheet — the Layered Logic mark (new `stroke_svg_to_black.py` to turn its `fill="none"` strokes into bands, plus `ll_flourish.py` to freeze the P5 mouse-histogram into a static cut growing off each L's outer side) and Bill's sister's empowder festival logo (raster-extracted from an embedded-PNG SVG, then `outline_black_svg.py` to convert the solid flower+mountain into a 3 mm outline). Fixed the core exporter so all DXF cut lines are solid red (`#FF0000` / ACI 1) — previously colorless. Shipped both spacings (`sheet_gap0.dxf` 300.0 exact, `sheet.dxf` 300.5 with 0.5 mm gap) plus squares-only frame files. This is the geometry-engine path to fulfilling multiple custom orders per laser job with zero per-order CAD. Untracked in git per the LL-082 convention; open decision is which gap to cut based on real stock size.

- [x] [LL-087](tasks.md#LL-087) **Home Assistant custom integration over the existing firmware (Jun 5).** Bill wanted the mirror back in Home Assistant, easy to re-add, without touching firmware. Mapped the V1 firmware's network API and confirmed it already exposes everything HA needs — so the answer is a **HACS-ready custom integration** (pure-Python `custom_components/layered_logic_mirror/`), not MQTT or ESPHome (both would mean changing/replacing firmware). The mirror becomes one native `light` entity: on/off, brightness (HA 0–255 ↔ device 0–100), RGB base color, and the 7 built-in patterns as the effect dropdown. `iot_class: local_push` — state rides the device's authoritative WebSocket `state` broadcasts, so flipping the physical button updates HA instantly. Setup supports **mDNS auto-discovery** (`_layeredlogic._tcp`, for same-LAN) and **manual IP** (the real path, since Bill's HA is on a different subnet and mDNS doesn't cross it), plus an optional paired-mode secret. Zero external Python deps. The one subtle piece, `protocol.py`, ports the mobile app's `ws-client.ts` framing + `hmac.ts` byte-for-byte (compact JSON, drop trailing `}`, HMAC the prefix, re-append) so paired-mode signing matches the firmware's `auth_logic.c`. **Verified ALL-PASS on the real dev mirror** (192.168.5.229, fw `ledfix-1833`) with a standalone `verify_mirror.py`: `/api/info`, `get_state`, and `set_state` for on/brightness/base_color/pattern_id, each confirmed via the authoritative broadcast. Surfaced (and designed around) the firmware quirk that `set_state`'s response is best-effort and races the writer task, so both the harness and the integration trust broadcasts, never the response. Still open: paired-mode HMAC isn't exercised on silicon yet (device is open mode), and HA-side install plus the Assist-MCP cross-check are pending a running HA instance. Per Bill, **spun it into its own standalone HACS repo** at `../layered-logic-mirror-ha` (sibling to this study repo, canonical home): repo-root `custom_components/`, `hacs.json`, `info.md`, MIT `LICENSE`, hassfest + HACS CI workflow, and `scripts/verify_mirror.py` (re-verified ALL-PASS from the new layout). `git init`'d + staged on `main`, but the **first commit/push is deferred until the mirror is confirmed working live in HA**. Removed the in-study `homeassistant/` copy to keep one source of truth; the LL-087 tracking docs stay here to commit later.

### In Progress

### Blocked

---

## Week 11 (Jun 9 – Jun 12): Launch Readiness Audit

### Done

### In Progress

### Blocked

---

## Related

- [Index / MOC](index.md)
- [Sprint Plan](sprint_plan.md) — the plan this log tracks against
- [Task Registry](tasks.md) — structured source of truth for task IDs and status
- [Task Event Log](task_log.md) — append-only event history
- [Task Format Spec](docs/task-format-v2.md) — schema, ID rules
- [Advisor Meeting — Apr 21](docs/Advisor-Meetings/advisor-meeting-2026-04-21.md) — most recent check-in
