layered-logic/infinity-mirror/task_log.md

---
title: Task Event Log
type: task-log
---

# Task Event Log

Append-only. Every meaningful task status transition gets one row. Format spec: [docs/task-format-v2.md](docs/task-format-v2.md) §4.2.

**Rules:**
- One row per event; multiple events in one session = multiple rows.
- Never edit an existing row. Corrections are appended as new rows with explanatory notes.
- `note` is ~1 sentence; full narrative lives in `sprint_log.md`.
- `artifact` is one link or `—`.

---

| date | id | event | note | artifact |
|---|----|---|---|---|
| 2026-03-23 | LL-001 | done | LLC Certificate of Formation filed pre-quarter for Layered Logic LLC (WA-formed domestic single-member) | — |
| 2026-04-02 | LL-002 | done | EIN 41-5282028 issued by IRS online | — |
| 2026-04-02 | LL-003 | done | Streamlit pricing dashboard with dynamic BOM, size scaling, tier/platform selection, and margin analysis | tools/pricing/ |
| 2026-04-02 | LL-004 | done | 5-phase stakeholder map covering 24 stakeholders across Creation, Distribution, Acquisition, Lived Experience, Support/Legacy | docs/stakeholder-map.md |
| 2026-04-06 | LL-005 | done | Single-member operating agreement finalized, printed, and signed with Schedule A capital contributions | — |
| 2026-04-06 | LL-006 | done | ESP32-C3-MINI-1 selected (smallest footprint, USB Serial/JTAG built in); C6 flagged as future Pro+ variant | docs/esp32-module-comparison.md |
| 2026-04-06 | LL-007 | done | 30+ listings analyzed across Etsy/Amazon/Pinterest; bifurcated 4-segment market | docs/Market%20Analysis%20Report.md |
| 2026-04-09 | LL-009 | done | 7-stage cradle-to-grave lifecycle; 6,368 energy samples; LED lifespan 14+ yr; key hotspot coated acrylic panels | docs/sustainability-audit.md |
| 2026-04-09 | LL-010 | done | Variable COGS $81.62 (qty 1) → $49.80 (qty 1,000); $65 retail recommended for early volumes | docs/bom-breakdown-basic-6x6.md |
| 2026-04-09 | LL-011 | done | JLCPCB STM8 PCB at $0.90/board at qty 100; pricing config $5 controller placeholder overstated | — |
| 2026-04-14 | LL-012 | done | Made-to-order workflow: 3 parallel lanes, 20 stations, batch-by-operation; Phase 1 tooling list finalized | Assembly_docs/ |
| 2026-04-20 | LL-013 | done | 9-section brand worksheet locked: 3-tier architecture, italic-default typography, hybrid palette, "[X] that layers." motif | docs/brand-positioning.md |
| 2026-04-20 | LL-014 | done | Three palette swatches as SVGs (Option B, Option C, Hybrid) with dark/light previews; Hybrid locked | assets/brand/color/ |
| 2026-04-20 | LL-015 | done | YAML frontmatter + Related cross-linking; MOC at index.md; standard markdown links over wikilinks for GitHub | index.md |
| 2026-04-20 | LL-016 | done | Asset folders scaffolded with subfolders for brand, moodboards, product-photos, icons, figma, source-files | assets/README.md |
| 2026-04-20 | LL-017 | done | First-pass review of Bill's separate logo P5 repo; 5 parked items captured in brand-positioning §7 | docs/brand-positioning.md |
| 2026-04-20 | LL-018 | done | Firmware architecture scoping doc with 5 design principles locked + 5 open decisions staged for Wed Apr 22 | docs/firmware-architecture-scoping.md |
| 2026-04-21 | LL-019 | done | Advisor meeting M1 close-out doc with 5 open questions for advisor | docs/Advisor-Meetings/advisor-meeting-2026-04-21.md |
| 2026-04-21 | LL-020 | done | Logo color resolved (outer #4A25FF Indigo Reference, inner #3214FF Indigo Signal); 3 deterministic SVG exports | assets/brand/logo/ |
| 2026-04-21 | LL-021 | done | Whole-vault palette re-anchored magenta-violet → indigo after rendered artifacts read too pink | docs/brand-positioning.md |
| 2026-04-21 | LL-022 | done | 3 Gemini JSON exports converted to paired .md with frontmatter + summaries; reusable converter script committed | external_chats/ |
| 2026-04-21 | LL-023 | done | WCAG audit caught indigo on near-black failing AA; section headers swapped to cream (~14:1 AAA); advisor doc trimmed 140→85 lines | assets/brand/color/ |
| 2026-04-21 | LL-024 | done | Typography rationale + logo spec spun out into dedicated docs; cross-links tightened across vault | docs/typography-decisions.md |
| 2026-04-22 | LL-025 | done | Two-button hardware model locked: primary (4 gestures) + recessed pinhole (3s pair / 10s factory reset) | docs/button-interface.md |
| 2026-04-22 | LL-026 | done | WA Business Licensing Service application submitted; UBI issued; $90 fee paid; Retailing+Manufacturing activities | — |
| 2026-04-22 | LL-027 | done | All 5 firmware architecture decisions locked: ESP-IDF+C, BLE+SoftAP provisioning, 2 variants (Pro/Pro+), self-hosted OTA, JSON envelope protocol | docs/firmware-architecture-scoping.md |
| 2026-04-22 | LL-028 | done | Confirmed N/A — FinCEN interim final rule exempts all US-domestic entities; re-check before Jun 21 | https://fincen.gov/boi |
| 2026-04-22 | LL-029 | done | V1 firmware: 4 core modules (state_bus, button, led_driver, pattern_interp) + ~50-test host harness; ESP-IDF 5.5.4 toolchain end-to-end | Firmware/v1/ |
| 2026-04-27 | LL-030 | done | Right-to-Repair philosophy doc finalized: 8 commitments, honest limits, EU/WA/CA compliance reinforcement | docs/right-to-repair-philosophy.md |
| 2026-04-27 | LL-031 | done | 17 failure-mode files across 8 categories: 12 fully user-repairable, 5 partial, 0 non-repairable | Failure_Modes/ |
| 2026-04-28 | LL-008 | done | External personal accounts linked + initial deposit cleared; account active and past inactivity threshold | — |
| 2026-04-28 | LL-032 | done | Two interview outlines (end-buyer + showcase partner) with 7-row "data we want" table tying questions to open decisions | docs/user-interview-outline.md |
| 2026-04-28 | LL-033 | done | HCDE button design rationale: 10 sections, 4 rejected alternatives, Eero precedent, 6 testable hypotheses | docs/button-design-rationale.md |
| 2026-04-28 | LL-034 | done | Pre-flash review caught critical bug in button.c (LL_PIN_BUTTON_RESET=-1 unguarded) + LED_COUNT_DEFAULT 32→66 | Firmware/v1/core/button/button.c |
| 2026-04-28 | LL-035-0 | done | V1 firmware booted on XIAO ESP32-C3 after fixing TASK_CORE 1→0 and led_count 32→66 in-session; button gestures + LED response confirmed | sprint_log.md |
| 2026-04-29 | LL-035-1-1 | done | 4MB ab_with_factory partition table verified on silicon; 25% headroom; existing NVS state survived partition swap | Firmware/v1/partitions.csv |
| 2026-04-29 | LL-035-1-2 | done | core/ll_mdns module advertises _layeredlogic._tcp.local with TXT records; folder rename mdns→ll_mdns to avoid build-graph collision | Firmware/v1/core/ll_mdns/ |
| 2026-04-29 | LL-035-1-3 | done | Transport + dev SoftAP + wscat ping/pong verified end-to-end; 2 in-session bugs fixed (sdkconfig stale, AP fast path race) | Firmware/v1/core/transport/ |
| 2026-04-29 | LL-035-1 | done | Session 1 closed; all 3 grandchildren resolved | Firmware/v1/core/transport/ |
| 2026-04-29 | LL-035-2-1 | done | get_state op live; state_to_json serializes 7 fields with #RRGGBB hex conversion | Firmware/v1/core/transport/transport.c |
| 2026-04-29 | LL-035-2-2 | done | set_state op live; 4 mutable fields, sensitive fields rejected; LEDs went bright green on first wire test | Firmware/v1/core/transport/transport.c |
| 2026-04-29 | LL-035-2-3 | done | broadcast_state + LL_EV_STATE_CHANGED subscription; two-watcher triangle verified at ~65ms latency | Firmware/v1/core/transport/transport.c |
| 2026-04-29 | LL-035-2 | done | Session 2 closed; all 3 grandchildren resolved; cross-client sync foundation laid | Firmware/v1/core/transport/transport.c |
| 2026-04-29 | LL-035-3 | done | Webapp scaffold (Vite + Preact + TS); first click changes mirror color; bundle 8.6KB gzipped (11% of 80KB budget) | Firmware/v1/webapp/ |
| 2026-04-29 | LL-035-4 | done | All 5 webapp capabilities wired (brightness, pattern, on/off, color, factory-reset stub); bundle 9.87KB gzipped (12% of budget) | Firmware/v1/webapp/src/app.tsx |
| 2026-04-29 | LL-035-5-1 | done | Webapp bundle embedded in firmware; pre-gzip in npm build; mDNS-over-SoftAP works on Windows as bonus | Firmware/v1/core/webapp_assets/ |
| 2026-04-29 | LL-035-5-2 | done | mDNS-over-hotspot Plan A confirmed for PC + browser via Win32 getaddrinfo; spike reverted clean | sprint_log.md |
| 2026-04-29 | LL-035-5-3 | done | Captive-portal DNS hijack + HTTP 404 redirect; Unicode arrow in format strings broke vsnprintf — defensive ASCII rule documented | Firmware/v1/core/captive_dns/ |
| 2026-04-29 | LL-035-5-4 | done | Setup screen + set_wifi_creds wire op; 15s fallback timer (typo'd password no longer strands device); webapp router + 3 pages | Firmware/v1/core/transport/transport.c |
| 2026-04-29 | LL-035-5-5 | done | LL_DEV_OPEN_SOFTAP → LL_SOFTAP_PROVISIONING rename + comment refresh; pure cleanup, no functional changes | Firmware/v1/core/provisioning/ |
| 2026-04-29 | LL-035-5 | done | Session 5 closed; all 5 sub-milestones resolved; webapp half of demo fully functional | Firmware/v1/webapp/ |
| 2026-04-30 | LL-035-6 | done | Sessions 6-8 collapsed: bare RN app + 5 controls end-to-end against live mirror; 3 Windows wedges hit and fixed | App/v1/ |
| 2026-04-30 | LL-035-7 | done | RN provisioning + Find Mirror (subnet scan + WifiInfo) + brand pass + first install on physical Pixel 9; 3 verification legs green | App/v1/ |
| 2026-04-30 | LL-035-8 | done | Cross-client sync verified: webapp + LLogic app simultaneously, state changes from either propagate to the other within broadcast latency | sprint_log.md |
| 2026-04-30 | LL-035 | done | Mini-sprint parent closed during cleanup; all 8 sessions resolved; demo gate hit 5 days ahead of May 5 advisor meeting | docs/mini-sprint-app-demo.md |
| 2026-04-30 | LL-036 | done | 3 RtR portfolio docs land (decisions matrix + scorecard + sub-MOC index); §5 comparative table TBD pending iFixit data | docs/repair-index.md |
| 2026-04-30 | LL-037 | done | Brand-positioning §1 sentence locked; product-name slot remains bracketed (Tier 2 naming deferred) | docs/brand-positioning.md |
| 2026-04-30 | LL-038 | done | OTA infrastructure V1→V2 verified end-to-end on silicon, USB unplugged; cyan welcome on reboot proves OTA replaced running code | Firmware/v1/core/ota/ |
| 2026-04-30 | LL-039 | done | User-definable mirror name + multi-mirror picker; NVS schema bumped 1→2; OTA cycle V2→V3 verified end-to-end | Firmware/v1/core/state_bus/ |
| 2026-05-01 | LL-040 | done | Three coupled fixes shipped: cleartext-traffic AndroidManifest hardcode, native NsdManager mDNS module, ip field in DeviceState | App/v1/android/app/src/main/java/com/v1/MdnsModule.kt |
| 2026-05-01 | LL-041 | done | Multi-network design doc locked with 5 §10 decisions (last-used wins, N_MAX=4, no auto-SoftAP, proactive disconnect, deprecation horizon) | docs/multi-network-design.md |
| 2026-04-18 | LL-045 | slipped | Week 3 PCB order critical-path item silently deferred; 5 STM8 test boards on hand cover near-term firmware work; production order out of quarter scope | — |
| 2026-04-22 | LL-042 | started | Customer-facing User Repair Guide drafting begun in parallel with right-to-repair philosophy doc | — |
| 2026-04-28 | LL-043 | started | User interview outlines drafted (LL-032); contact list compilation and outreach commencing | docs/user-interview-outline.md |
| 2026-04-28 | LL-044 | blocked | Awaiting LL-051 (packaging concept) — needs cardboard stock, dimensions, and print/laser process decided before QR placement is meaningful | — |
| 2026-05-07 | LL-046 | started | Step 1/6 (NVS layer) shipped — new core/ll_wifi/ module with list ops + migration shim hook + 27 host tests; provisioning wiring deferred to Step 2 | Firmware/v1/core/ll_wifi/ |
| 2026-05-07 | LL-046 | progress | Step 2/6 (provisioning refactor) build-clean on esp32c3 — STA driven from ll_wifi, legacy esp_wifi cred migration, set_wifi_creds writes to ll_wifi first, fallback removes failed entry, factory reset wipes both stores; flash + boot capture pending hardware availability | Firmware/v1/core/provisioning/provisioning.c |
| 2026-05-07 | LL-046 | progress | Step 2 OTA-flashed onto live mirror (b2332c at 192.168.5.229) — fw_version flipped ip-state-v3 → 4c1f888-dirty, STA auto-reconnected to "IoT" at same IP, all 7 ll_settings fields preserved across reboot. Migration shim verified: legacy esp_wifi cred read from `nvs.net80211` and copied into ll_wifi[0] on first boot of multi-network firmware | Firmware/v1/scripts/trigger_ota_step2.py |
| 2026-05-07 | LL-046 | progress | Step 3 SM (SCANNING/CONNECTING/ONLINE/BACKOFF) shipped — provisioning.c now scans first then picks highest-priority visible saved network. First OTA bricked the mirror via stack overflow in scan_done (1.6KB stack array on the system event task's small stack); USB recovery flashed the stack-fixed build, which booted clean and SM connected to "IoT" automatically. State preserved | Firmware/v1/core/provisioning/provisioning.c |
| 2026-05-07 | LL-046 | progress | OTA rollback safety net wired — CONFIG_BOOTLOADER_APP_ROLLBACK_ENABLE=y in sdkconfig.defaults, new ll_ota_subscribe() marks the running image valid on first LL_EV_WIFI_CONNECTED, main.c calls it after captive_dns_subscribe. Future OTAs that panic before getting online will auto-rollback to the previous slot. Bootloader change deployed via USB flash | Firmware/v1/core/ota/ota.c |
| 2026-05-07 | LL-046 | progress | Step 4/6 (wire protocol ops) shipped + OTA-verified — list_wifi_networks / add_wifi_network / remove_wifi_network landed in transport.c, wifi_saved_count added to DeviceState. add/remove trigger broadcast_state so connected clients refresh. New ll_provisioning_drop_active() lets remove_wifi_network proactively disconnect when removing the active SSID. Smoke tested end-to-end on live mirror at 192.168.5.229 (insert/update/full/invalid/remove/not_found paths all green) | Firmware/v1/core/transport/transport.c |
| 2026-05-07 | LL-046 | progress | Step 5/6 (RN app Settings UI) shipped — protocol.ts gained WifiNetwork + add/remove payload types and wifi_saved_count in DeviceState; ws-client added listWifiNetworks/addWifiNetwork/removeWifiNetwork; App.tsx Settings page replaced the single "Reconfigure Wi-Fi" block with a saved-networks list (active checkmark + Forget button per row), an inline "Add a network" form, and a confirm-dialog on forget-active per design-doc §4.3. Settings page refetches the list on entry and on wifi_saved_count broadcasts. Type-check clean against the project's tsconfig | App/v1/App.tsx |
| 2026-05-07 | LL-046 | progress | Step 6 hardware test surfaced a real UX gap: bad creds on a 2nd network + Forget on the active first network ⇒ stuck (no auto-SoftAP per spec, recessed-button hold not obvious). Recovered via USB esptool erase_region of NVS partition (0x9000+0x6000) — preserves firmware, wipes ll_settings + ll_wifi + esp_wifi cred, drops to SoftAP cleanly | — |
| 2026-05-07 | LL-046 | progress | Bug fix: new connect_wifi_network wire op + Connect button per non-active row in Settings. Firmware adds ll_wifi_bump_priority(ssid, ts) (last_used only — doesn't lie about active_idx) and ll_provisioning_request_switch (handles ONLINE/CONNECTING/BACKOFF/SCANNING/IDLE — disconnects mid-flight, cancels backoff, etc.). RN app gains connectWifiNetwork() + the per-row button. Closes the dual-network "stuck on bad creds" recovery path while staying within the spec's "no auto-SoftAP" frame. Firmware USB-flashed; APK built (install pending phone reattach) | App/v1/App.tsx · Firmware/v1/core/transport/transport.c |
| 2026-05-07 | LL-046 | progress | Status-bar overlap fix — switched ANDROID_STATUS_BAR_PADDING from a module-load read of StatusBar.currentHeight (returned 0 in cold-start races on Android 15 / Pixel 9 → title untappable under the system bars) to a render-time read floored at 32px. Tried react-native-safe-area-context first; on Windows the deep worktree path blew the C++ codegen filenames past MAX_PATH and a subst-aliased drive broke path.relative on cross-drive lookups, so the minimum-padding approach shipped instead | App/v1/App.tsx |
| 2026-05-07 | LL-046 | progress | connect_wifi_network UX polish — first hardware run had no haptic/visual feedback on tap and the WS op was timing out from the client perspective because ll_provisioning_request_switch() was tearing down the STA synchronously before the response could flush. Refactored to post a new LL_EV_WIFI_REQUEST_SWITCH event; provisioning's handler runs on the state-bus task with a 250ms response-flush yield (same pattern as on_wifi_apply_creds). App side: optimistic clear of is_active on tap, "Switching to X…" banner, 15ms Vibration buzz, list-refetch useEffect now keys on state.wifi_ssid not just wifi_saved_count so the post-switch settle replaces the optimistic state | Firmware/v1/core/state_bus/state_bus_events.h · App/v1/App.tsx |
| 2026-05-07 | LL-046 | progress | Two follow-on fixes from a second hardware pass: (1) Vibration.vibrate(15) was crashing the app — VIBRATE permission missing from AndroidManifest.xml. Added the permission + wrapped the call in try/catch as defense-in-depth. (2) Banner copy promised "App will reconnect when it's back" which is wrong unless the phone happens to be on the network the mirror switched TO; reworded to tell the user explicitly to match their phone's Wi-Fi and re-run Find mirror. (3) Find-mirror "no mirror found" error now mentions disabling VPN as the most common cause | App/v1/android/app/src/main/AndroidManifest.xml · App/v1/App.tsx |
| 2026-05-07 | LL-046 | done | Multi-network firmware shipped end-to-end across 5 design-doc steps + 1 bonus connect_wifi_network op (added during Step 6 hardware test) + OTA rollback safety net (added during Step 3 hardware test) + status-bar overlap fix + UX polish round. 27 host tests on the NVS layer, all paths smoke-tested on live mirror. 10 commits between 6d3f9bc and 9ecf625 | Firmware/v1/core/ll_wifi/ · Firmware/v1/core/provisioning/provisioning.c · App/v1/App.tsx |
| 2026-05-07 | LL-050 | done | Supply-chain map landed for Milestone 2 — 13-line component table with primary + backup cascade per row (Amazon → AliExpress → Temu → factory direct for commodity items; JLCPCB → PCBWay → OSH Park for PCB fab), executive risk summary (tariff = high, lead time = medium-but-graceful, single-source = low), and 3 open actions for downstream specs (packaging, LED holders, USB-C PD wattage) | docs/supply-chain-map.md |
| 2026-05-07 | LL-073 | done | RN app polish — haptic helper (light/medium/heavy + pattern() + brightness()) wired across all action buttons including content-encoded haptic per LED pattern; replaced the 12 brand-color dots with a full-width 512×512 color wheel (HSV polar mapping) with a top-right color preview, touch-follow magnifier bubble, and scroll-lock during drag. Pattern haptics retuned on a second pass (50% longer, 20% softer) | App/v1/src/haptic.ts · App/v1/assets/color-wheel.png |
| 2026-05-13 | LL-053 | done | 10-stage service blueprint with Customer Journey / Frontstage / Backstage / Support lanes per stage, moments-of-truth + fail-point callouts, summary table, and 4 newly-surfaced open actions flagged for triage | docs/service-blueprint.md |
| 2026-05-13 | LL-054 | done | Custom-order flow mapped as dedicated 10-step deep-dive section of LL-053: inquiry → concept + price band → proof → revisions (capped at 3) → approval + 50% deposit → manufacture → pre-ship review → balance + ship; frontstage/backstage table + 5 fail-points + 5 open research questions for LL-048 | docs/service-blueprint.md#custom-order-deep-dive |
| 2026-05-13 | LL-074 | done | User-flow authoring methodology locked (user-voice diamonds, two-layer pain evaluation, orange/red split, natural cognitive order, modality compression) + Stage 1 (Discover) rendered with Graphviz via viz-js after Mermaid ruled out; key gotcha captured: rank=same in rankdir=LR means same column, not same row | docs/user-flow-authoring.md |
| 2026-05-14 | LL-043-1 | added | Content-creator + streamer outreach spun out as child of LL-043; per-lane script variants, n8n flow outline, contact research captured | docs/outreach-list.md |
| 2026-05-14 | LL-043 | progress | Cold outreach campaign engaged — 5 sends today across smart-home (Reed Kleinman/Smart Home Solver, Robert Tait/The Hook Up, Lewis/Everything Smart Home), maker (Matt Perks/DIY Perks), and indie-founder (Joe Barnard/BPS.space) lanes; tone calibration locked after first two sends | docs/outreach-list.md |
| 2026-05-14 | LL-069 | rescoped | "Estimated quarterly taxes" → "Tax filing setup (WA DOR + federal 1040-ES)". Federal 1040-ES not required (no income, <$1K expected tax); WA DOR file-zero obligation kicked in with Apr 22 BLS registration — need to check assigned filing frequency at secure.dor.wa.gov. Deadline moved Apr 15 → Jun 15 | — |
| 2026-05-14 | LL-052 | blocked | PCB hardware integration formally marked blocked-out-of-quarter on LL-045 (PCB order slipped Apr 18); deadline cleared. Demo path locked on XIAO ESP32-C3 dev kit | — |
| 2026-05-14 | LL-043 | deadline-shifted | Deadline May 9 → May 30 to match the engaged-on-May-14 campaign window (Milestone 3 boundary) | docs/outreach-list.md |
| 2026-05-14 | LL-048 | deadline-shifted | Deadline May 9 → May 30 to match LL-043 reply window | — |
| 2026-05-14 | LL-069 | progress | Layered Logic added to My DOR portal; no current action items surfaced. Filing frequency pending welcome letter / physical license by mail (almost certainly annual default for $0-projection new businesses → Jan 31, 2027 for 2026 activity) | — |
| 2026-05-14 | LL-055 | started | Firmware Wi-Fi/BLE resilience stress-test engaged. First fix landed: broadcast debounce in transport.c — 30ms one-shot timer coalesces rapid-fire state changes into a single client broadcast. Verified on live mirror at 192.168.5.229: 3-field set_state goes from 3 broadcasts → 1; 6 rapid color sets at ~30ms intervals goes from 6 → 2 (correct burst-coalescing behavior, not flat 1-broadcast collapse) | Firmware/v1/core/transport/transport.c |
| 2026-05-12 | LL-051 | started | Two CEFbox parametric dieline templates captured as starting points: Ear-Lock Mailer (outer box) + Insert With Backing (inner tray). Parked a parametric Python dieline generator idea (custom L×W×D in → cut/score SVG + nested cardboard sheet size out) — not yet started, awaiting scope agreement | tasks.md#LL-051 |
| 2026-05-12 | LL-051 | slipped | Started in sprint 6 plan (May 5–9, M2 deadline), active in sprint 7. Deferral cost was zero — packaging concept was unblocking only LL-044 (QR code) which is itself blocked on this | — |
| 2026-05-12 | LL-051 | progress | Path B (hand-derive) chosen over scraping CEFbox. First two artifacts: docs/packaging-dielines.md (parametric math + SVG layer conventions + validation plan) and Assembly_docs/packaging/sketch_dielines.py (matplotlib preview of REFT mailer + tray-with-backer insert at default 8x8x3 in outer dims). Sketch-first / generator-second per the basic_housing precedent | docs/packaging-dielines.md · Assembly_docs/packaging/ |
| 2026-05-12 | LL-051 | progress | Pivoted to Path A after v1 sketch caught wrong by Bill vs CEFbox screenshots. 10 reference DXFs at controlled dim variations parsed via ezdxf. Recovery script searches simplest clean formula a*L + b*W + c*H + d*t + const per coord — ~60% resolve cleanly (constants, +-L, L/2+-k, L+k*t variants); ~40% are arc-endpoint coords needing separate (cx, cy, r, sa, ea) recovery. Topology now understood: mailer REFT is 5-panel spine with 2H roll-end walls (doubled fold); insert is backer + floor + 4 down-walls + centered slot cradle | Assembly_docs/packaging/coord_formulas.json |
| 2026-05-12 | LL-051 | progress | Pivoted from per-coord formula recovery (~60% clean) to NAMED-PARTS architecture: graph of structural pieces with rules, Y-symmetry as hard constraint. Mailer in 6 phases: spine + scores -> roll-end side walls with W-conditional tooth pattern -> dust flaps with case-A/B logic at H ~ 100-2.5t threshold -> ear-lock arcs (4 main + 2 horns + 2 score-tangents + 4 tangent diagonals) -> finger holes (1 per outer tooth) -> cleanup with 14 panel-fold scores + corner connectors. Critical bug caught: dieline mirror axis is x = L/2 + 5t, NOT L/2 -- every right-side coord was off by 10t until traced via manual symmetry inspection of baseline DXF | Assembly_docs/packaging/mailer_reft.py |
| 2026-05-12 | LL-051 | progress | Insert generator landed in 5 phases: floor + scores + slot/cradle -> top bands (back wall + hem + backer + hem flap) -> front wall + bottom corner arcs -> side walls + corner arcs -> tangent diagonals + corner micro-chamfers. N-slot support from day one via Slot(cx,cy,SL,SW,SH) records; single_slot() and n_slot() constructors. Degenerate-cradle handling for SH >= SL/2 or SW/2 (collapses to a Line; effective SH clamped per-slot). Insert mirrors about L/2 exactly (unlike mailer's L/2 + 5t) | Assembly_docs/packaging/insert_tray.py |
| 2026-05-12 | LL-051 | progress | Validation framework: entity-count + Y-symmetry tests against reference DXFs. Arc canonicalization via (midpoint, sweep) to handle 0/360 wrap; polyline canonicalization dedupes explicit closing points; 0.01mm rounding to defeat FP drift between left/right mirrored values. TestCase supports skip_symmetry for asymmetric multi-slot inserts. 10/10 reference DXF tests PASS (5 mailer + 5 insert) | Assembly_docs/packaging/validation.py |
| 2026-05-12 | LL-051 | progress | CEFbox-style geometric rules added to both Specs as validate() methods, called at start of generate(). Insert enforces 5mm slot-edge buffer from floor edges + 5mm pairwise slot gap. Mailer enforces W >= 180 (tooth pattern lower bound), L >= 60, H in [20, 200], t in [0.5, 5.0], H >= 2t (case A non-degenerate). Bad inputs raise ValueError with specific actionable messages | Assembly_docs/packaging/insert_tray.py · Assembly_docs/packaging/mailer_reft.py |
| 2026-05-12 | LL-051 | done | LL-051 closed. Production-ready parametric REFT mailer + N-slot insert generators with passing validation suite (10/10 reference DXFs). Style fix landed (solid lines, color-only differentiation). Practical bbox at 225x225x60 mailer = 498.5 x 638.25 mm (fits 520x660 sheet with 10mm hold-down margin; 600x800 recommended for 1-up production). Out of scope today: nest.py for sheet packing, first physical test cut, LL-044 QR raster wiring -- each is now-unblocked separate workstream | Assembly_docs/packaging/ |
| 2026-05-14 | LL-051 | imported | Recovered the May 12 work from the gifted-tharp-af5d28 worktree where it had been uncommitted. Earlier same-day import attempt (c498966) accidentally committed the paid CEFbox reference DXFs into the public repo — reverted in c3ae593 + gitignore rule added; proper deliverable (parametric generators + rationale doc) imported here | Assembly_docs/packaging/ · docs/packaging-dielines.md |
| 2026-05-14 | LL-044 | unblocked | LL-051 work now properly in branch; QR raster region available on the insert backer for whenever LL-044 is prioritized | — |
| 2026-05-14 | LL-047 | started | Pivoted from Figma to SVG-native lo-fi wireframes paired with markdown rationale docs (portfolio chapters indexing into existing decision docs). Chapter 1 (Settings — Wi-Fi) landed: 6 callouts + 4 alternate-state thumbnails + paired markdown with TL;DR / user-flow link / research-to-design honesty table / implementation gaps. Template set for chapters 2-5 | docs/wireframes/ |
| 2026-05-15 | LL-055-1 | added | BLE reconnection scope split off from LL-055 into its own child task. Parked-on-dependency: BLE provisioning is a post-V1 stretch goal per post-mini-sprint-bugs.md #6, so the reconnect stress-test can't be exercised until that lands. Not de-scoped — reopens when BLE provisioning ships | tasks.md#LL-055-1 |
| 2026-05-15 | LL-055 | progress | Session plan locked for the remaining resilience work: Session A (SoftAP power-save audit, ~½ day) → Session B (broadcast fanout to separate task + queue, ~1 day) → Session C (§7.1 rate limit, ~½ day) → Session D (Wi-Fi drop + jitter scenarios, open-ended). Deadline May 16 will slip; Bill confirmed no de-scope. BLE reconnection split off to LL-055-1 | tasks.md#LL-055 |
| 2026-05-15 | LL-055 | progress | Session A done — wifi power-save audit + fix. Zero esp_wifi_set_ps calls in firmware; ll_wifi_disable_ps helper + WIFI_PS_NONE at all four esp_wifi_start sites (init STA, init SoftAP, apply_creds STA, SoftAP fallback). Verified on live mirror 192.168.5.229: ll_debounce_test.py first-response latency 155ms→84ms (Test A, −46%), 136ms→64ms (Test B, −53%), 202ms→187ms (Test C, −7% — dominated by 5×30ms inter-send sleeps in the script). Build+OTA wrinkles caught for the runbook: fresh worktree needed npm install for webapp embed; stale sdkconfig defaulted to esp32 not esp32c3 (ESP_ERR_INVALID_VERSION covers chip-ID mismatch, not just version-equal) | Firmware/v1/core/provisioning/provisioning.c |
| 2026-05-15 | LL-055 | progress | Session B done — broadcast fanout on a dedicated FreeRTOS task. New ll_broadcast task (4KB stack, prio 4) consumes a depth-2 queue of broadcast tokens; debounce timer cb posts to the queue instead of calling do_broadcast_state synchronously, so slow-client TCP backpressure no longer ties up esp_timer task. Verified on 192.168.5.229: ll_debounce_test.py regression clean (broadcast counts within burst-coalescing tolerance); new ll_slow_client_test.py = 20/20 inbound responses in both phases, median 72ms→71ms with slow client pinning a socket — inbound dispatch unaffected by clogged outbound fd. Binary 1.21MB/1.25MB partition (7.6% headroom, +96KB from new FreeRTOS queue/task symbols) | Firmware/v1/core/transport/transport.c · Firmware/v1/scripts/ll_slow_client_test.py |
| 2026-05-15 | LL-055 | progress | Session C done — per-IP rate limit (spec §7.1 closeout). Token bucket per peer IP (burst 10, refill 10/s), milli-token math (no float on C3), 8-slot fixed table with oldest-last_refill eviction. IPv4 lookup via getpeername; handles AF_INET and v4-mapped AF_INET6. Enforced on HTTPD_WS_TYPE_TEXT frames only. Overrun → ws_send_close(1008) + httpd_sess_trigger_close. Verified on 192.168.5.229 via new ll_ratelimit_test.py: steady 10 msg/s = 30/30 clean; flood 50 msg/s = close 1008 at t=0.43s after 13 ACKs; after-close reconnect = ping OK. Regressions clean (ll_debounce_test 1+1/1+1/6+3; ll_slow_client_test 20/20 both phases after bumping probe interval 50→100ms — the test was the bug, not the firmware). Build cost +1.4KB | Firmware/v1/core/transport/transport.c · Firmware/v1/scripts/ll_ratelimit_test.py |
| 2026-05-15 | LL-055 | done | Session D done + LL-055 closed — resilience characterization + test harness. No firmware changes; characterization pass on Sessions A-C work. Five new scripts in Firmware/v1/scripts/: ll_reconnect_hammer.py (30/30 reconnects, uptime monotonic), ll_ws_proxy.py (TCP-level latency+loss proxy), ll_jitter_test.py (200ms one-way latency = 10/10 set_state succeed; 1% loss = 10/10; 5% loss breaks WS handshake, not a defect), ll_soak_test.py (5min @ 5 msg/s = 1476 iter, 0 errors, RTT drift -0.4ms first-vs-second half, uptime monotonic — no leaks, no reboots), ll_ap_toggle_test.py (manual, handed to Bill for hotspot-off toggle test). All four bug-doc entries that motivated LL-055 now closed. LL-055-1 (BLE reconnection) stays parked-on-dependency | Firmware/v1/scripts/ |
| 2026-05-15 | LL-075 | added | Created to track the post-mini-sprint-bugs.md #2 fix (on/brightness wire-state coupling) | tasks.md#LL-075 |
| 2026-05-15 | LL-075 | done | Two coupled invariants in state_bus.c apply_event: LL_EV_BRIGHTNESS now also sets on=(value>0); LL_EV_POWER_TOGGLE{on:true} auto-restores brightness to 75 if currently 0. Power-off preserves brightness (no UX regression on button-hold→single-press cycle). Boot self-heal in ll_state_bus_init catches legacy (on=true, brightness=0) NVS blobs. Verified via new ll_on_brightness_invariant_test.py: 6/6 cases pass on live mirror. ll_debounce_test regression clean. Bug-doc #2 moved to Closed | Firmware/v1/core/state_bus/state_bus.c · Firmware/v1/scripts/ll_on_brightness_invariant_test.py |
| 2026-05-15 | LL-057 | started | App ↔ hardware integration polish engaged. Scope locked as "wide" (Bill's call): telemetry + paired-mode auth stay in-scope. Session plan A→B→C→D in tasks.md notes. Will slip past May 23 Week 8 deadline | tasks.md#LL-057 |
| 2026-05-15 | LL-057-A | added | Created to track the stuck-OTA-button useEffect reset fix | tasks.md#LL-057-A |
| 2026-05-15 | LL-057-A | done | Session A done — App.tsx prevConnRef + useEffect resets otaState 'rebooting'→'idle' on conn transition non-open→open. Transition-not-steady-state distinction is the trick (otherwise resets mid-OTA before reboot). tsc clean on App.tsx; 4 pre-existing TS errors elsewhere are unrelated. Runtime verify pending Bill's next Pixel 9 OTA cycle | App/v1/App.tsx |
| 2026-05-15 | LL-057-B | added | Created for Session B (real OTA progress) | tasks.md#LL-057-B |
| 2026-05-15 | LL-057-B | blocked | Architecturally blocked. Bisect found any broadcast during the OTA window (or from httpd task immediately before esp_https_ota call) causes install ESP_FAIL or rollback on boot. Three approaches tried: begin/perform/finish migration; ESP_HTTPS_OTA_EVENT subscription; op_start_ota wrapper. All fail. Forward-compat scaffolding shipped on App side (OtaProgressBroadcast wire type + onOtaProgress callback + otaProgressLabel UI). Firmware retry needs OTA on a worker task (off httpd) before progress broadcasts are safe. Bisect chain corrupted live mirror's OTA partition state; needs USB recovery → spawned LL-076 | App/v1/App.tsx · App/v1/src/protocol.ts · Firmware/v1/webapp/src/protocol.ts |
| 2026-05-15 | LL-076 | added | Mirror OTA partition recovery — bisect chain left otadata/ota_X in a refusing-all-installs state. Recovery = idf.py erase-flash + flash via USB | tasks.md#LL-076 |
| 2026-05-15 | LL-057-C | added | Created for Session C (telemetry MVP) | tasks.md#LL-057-C |
| 2026-05-15 | LL-057-C | done | Three layers shipped: Cloudflare Worker at telemetry.layeredlogic.cc/v1/beacon (TS, KV-backed, /healthz + /latest endpoints + 90-day TTL); app + webapp settings toggles wired through set_state {telemetry_enabled}; core/telemetry/ firmware module with 24h ± 2h jittered POST + boot-reason panic flag + esp_crt_bundle TLS. Firmware 1.23MB / 1.25MB partition (1.8% headroom, mostly CA bundle). E2E verify gated on LL-076 device recovery; per-layer typecheck/compile clean | cloudflare-workers/telemetry/ · Firmware/v1/core/telemetry/ · App/v1/App.tsx · Firmware/v1/webapp/src/pages/settings.tsx |
| 2026-05-15 | LL-076 | done | USB erase-flash + reflash recovered the mirror at 192.168.5.229. idf.py erase-flash COM3 (14s chip wipe) + idf.py flash COM3 + re-provision via SoftAP captive flow. Subsequent 4 USB-flash cycles (telemetry-mvp → final) all clean. Unblocks LL-057-C E2E verify | — |
| 2026-05-15 | LL-057-C | verified | E2E live test confirmed beacon path. Bill deployed Worker on layeredlogic.workers.dev subdomain. Real beacon at /latest/b2332c ~100s after telemetry-enable toggle. Caught + fixed two bugs during E2E: (1) CF Bot Fight Mode 403 on default User-Agents — added explicit UA in telemetry.c; (2) op_set_state was silently dropping telemetry_enabled — added missing branch in transport.c. Plus reset_reason_str expansion for ESP_RST_USB/JTAG/EFUSE/PWR_GLITCH/CPU_LOCKUP | Firmware/v1/core/telemetry/telemetry.c · Firmware/v1/core/transport/transport.c |
| 2026-05-15 | LL-043 | progress | Sent-table correction: actual May 14 send count was 11 (DeFranco, Corridor, Aztecross, Jake, Reed, Robert, Lewis, Matt, Joe, TechHut, Hardware Haven), not 5 as sprint-log undercount implied. First reply landed same day from Colten / Hardware Haven (swamped, receptive); followup sent with UW HCDE framing + smart-home-indicator positioning + studio-curation question (from user-interview-outline §1) + AI render of mirror with channel logo + real prototype photo. Two campaign rules locked: no X/Twitter/Mastodon channels; no Fri PM / weekend sends | docs/outreach-list.md |
| 2026-05-15 | LL-043-1 | progress | Monday queue staged with 5 NEW email-verified targets: Hackaday (tips@hackaday.com), iFixit (press@ifixit.com), Tested (tips@tested.com), Strange Parts / Scotty Allen (scotty@strangeparts.com), Hardware Canucks / Dmitry (dmitry@hardwarecanucks.com). Mix diversifies from May 14's Lane-A-heavy batch into press / repair / indie-founder / gaming-desk lanes. bitluni dropped to channel-blocked (X/Mastodon/Tindie only). Drafting calibrations from Hardware Haven followup captured in feedback memory: positioning > specs (even for gear-heads), specific visual refs, don't reflect recipient state, attach visual hook when the question is visual, no em dashes, "legitimate product" > "actually sellable" | docs/outreach-list.md |
| 2026-05-18 | LL-069 | done | DOR welcome letter (May 15) confirmed quarterly filing on Account ID 606-138-559; first return Q1 2026 due Jun 15 (one-time extension), standard due dates Apr 30 / Jul 31 / Oct 31 / Jan 31; must file zero returns; recurring filings tracked as children LL-069-1..4 | tasks.md#LL-069 |
| 2026-05-18 | LL-069-1 | added | Q1 2026 WA excise return — zero-activity filing due Jun 15, 2026 (one-time extension from Apr 30) | tasks.md#LL-069-1 |
| 2026-05-18 | LL-069-2 | added | Q2 2026 WA excise return — zero-activity filing due Jul 31, 2026 | tasks.md#LL-069-2 |
| 2026-05-18 | LL-069-3 | added | Q3 2026 WA excise return — zero-activity filing due Oct 31, 2026 | tasks.md#LL-069-3 |
| 2026-05-18 | LL-069-4 | added | Q4 2026 WA excise return — zero-activity filing due Jan 31, 2027 | tasks.md#LL-069-4 |
| 2026-05-20 | LL-056 | done | ToS & Warranty policy drafted — 13-section legal doc; ships as a draft pending counsel review | docs/terms-of-service-and-warranty.md |
| 2026-05-20 | LL-077 | added | Mirror Assembly & Teardown Guide spun out as the operations-track prerequisite LL-042 was blocked on | docs/assembly-guide.md |
| 2026-05-20 | LL-077 | done | Assembly + teardown guide written from the 20-station process, the housing scripts, and the BOM | docs/assembly-guide.md |
| 2026-05-20 | LL-042 | unblocked | Assembly-guide dependency resolved by the new LL-077 | docs/assembly-guide.md |
| 2026-05-20 | LL-042 | done | User Repair Guide written — customer-facing procedures for all 17 failure modes; repair-index §6 placeholder replaced | docs/user-repair-guide.md |
| 2026-05-20 | LL-057-D | added | Session D (paired-mode auth) — scoping doc skipped, implementing directly against firmware-security §5 | tasks.md#LL-057-D |
| 2026-05-20 | LL-057-D | progress | D1 done — core/auth/ module (auth + host-testable auth_logic: SHA-256/HMAC/canonicalization) + 21 host tests pass, clean -Werror build | Firmware/v1/core/auth/ |
| 2026-05-20 | LL-057-D | progress | D2 done — core/auth wired into variants/standard/main.c + variant CMakeLists; built esp32c3, OTA-flashed cec5bd3-dirty to the live mirror, boots clean (no rollback, auth_mode=open, uptime 188s) | Firmware/v1/variants/standard/main.c |
| 2026-05-20 | LL-057-D | rescoped | SNTP dropped from the session plan (Bill's call) — replay protection via per-socket monotonic-ts guard + req_id dedup; remaining D-stages renumbered D2-D4 | tasks.md#LL-057-D |
| 2026-05-20 | LL-056 | progress | Post-draft: contact email, warranty period, and 50/50 custom-order deposit structure confirmed with Bill; all [CONFIRM] markers cleared from the doc | docs/terms-of-service-and-warranty.md |
| 2026-05-20 | LL-043-1 | progress | 5-target Monday queue (Hackaday, iFixit, Tested, Strange Parts, Hardware Canucks) drafted + staged in outreach-list.md § Drafted for Bill to review and send; per-lane subject+body, sends pending | docs/outreach-list.md |
| 2026-05-20 | LL-057-D | progress | D3 done — paired-mode auth gate in transport handle_envelope() + set_auth_mode/rotate_secret ops + per-socket monotonic-ts + req_id-dedup replay guard; OTA-flashed d3auth-1349, 16/16 checks via ll_auth_test.py; firmware-security §5.4 + control-protocol-spec §3.1/§8 amended | Firmware/v1/core/transport/transport.c |
| 2026-05-15 | LL-047 | done | All 5 wireframe chapters delivered (settings-wifi, home-control, first-boot-setup, mirror-picker, pattern-designer) — authored May 14-15, merged via PR #19; logged 2026-05-20 as a tracking catch-up. Ch5 is pattern-designer (V2 editor), not the planned custom-design-request (no app surface) | docs/wireframes/ |
| 2026-05-20 | LL-057-D | done | D4 done — app side: vendored pure-TS SHA-256/HMAC (hmac.ts), hmac-last frame signing + setAuthMode/rotateSecret in ws-client.ts, Settings pairing UI + unlock screen in App.tsx; tsc clean (4 pre-existing errors only), hmac verified byte-exact vs Node crypto; runtime UI verify deferred to Bill's Pixel | App/v1/src/hmac.ts |
| 2026-05-20 | LL-057 | done | App↔hardware integration polish closed — sessions A/C/D done, B deferred (architecturally blocked, tracked as LL-057-B); landed May 20 inside the Week 8 window | App/v1/App.tsx |
| 2026-05-20 | LL-049 | deadline-shifted | Deadline May 16 → May 30 to match the LL-048 interview window / Milestone 3 boundary; the original date had already passed | — |
| 2026-05-20 | LL-049 | progress | Cafe contact-list scaffold (fillable Lane F table + 5-7-venue sourcing method) + Variant 4 in-person/email outreach script built in outreach-list.md; named venues + interviews pending Bill | docs/outreach-list.md |
| 2026-05-20 | LL-078 | added | Webapp paired-mode support — the webapp counterpart to LL-057-D D4; the device-hosted webapp had no pairing UI and couldn't sign frames | tasks.md#LL-078 |
| 2026-05-20 | LL-078 | done | Webapp pairing shipped — vendored hmac.ts + ws-client signing + settings pairing panel + app.tsx unlock screen (localStorage-persisted secret); built into firmware webauth-1444, OTA-flashed, browser-verified end-to-end (pair → signed control → reload re-auth). firmware-security §5.4 amended | Firmware/v1/webapp/src/ |
| 2026-05-20 | LL-079 | added | Proto SoftAP fallback — fix for the no-reachable-network demo lockout Bill hit in a test session | tasks.md#LL-079 |
| 2026-05-20 | LL-079 | progress | APSTA AP-fallback implemented in provisioning.c (ensure_ap_fallback_up after ~2 backoff cycles); clean esp32c3 build, 1% headroom, host suite 140/140; OTA flash + boot capture pending | Firmware/v1/core/provisioning/provisioning.c |
| 2026-05-20 | LL-080 | added | Single-button factory-reset combo — recovery gesture for the recessed-button-less C3 proto | tasks.md#LL-080 |
| 2026-05-20 | LL-080 | progress | factory_combo_step recognizer (5s-hold / tap / 5s-hold) + button.c wiring + 8 host tests; full suite 140/140; OTA flash + boot capture pending | Firmware/v1/core/button/button_logic.c |
| 2026-05-20 | LL-079 | progress | WebSocket OTA install rejected ESP_FAIL (esp_https_ota, post-download) — same otadata symptom as LL-076; recovered via USB flash | Firmware/v1/core/ota/ota.c |
| 2026-05-20 | LL-079 | done | USB idf.py flash of demofix-1714 to the mirror (COM3) — also rewrites ota_data_initial.bin, clears otadata; clean boot verified (uptime 68s, get_state green, STA on "IoT") | Firmware/v1/core/provisioning/provisioning.c |
| 2026-05-20 | LL-080 | done | Shipped in the demofix-1714 USB flash; clean boot verified on silicon; combo recognizer host-tested (8 tests), not live-exercised (destructive) | Firmware/v1/core/button/button_logic.c |
| 2026-05-20 | LL-079 | progress | AP fallback verified live on the mirror — with no reachable saved network the device broadcasts its SoftAP | Firmware/v1/core/provisioning/provisioning.c |
| 2026-05-20 | LL-080 | progress | Single-button factory-reset combo verified live on the mirror — the 5s/short/5s sequence triggers a hard reset | Firmware/v1/core/button/button_logic.c |
| 2026-05-20 | LL-081 | added | LED count reverted to the 32-LED 6x6 default after the LL-080 factory reset on the 66-LED dev proto | tasks.md#LL-081 |
| 2026-05-20 | LL-081 | done | state_bus.c stamps led_count from LL_LED_COUNT_DEFAULT (board.h) on every g_state seed/reset; OTA-flashed ledfix-1833, get_state verified led_count 66 | Firmware/v1/core/state_bus/state_bus.c |
| 2026-05-26 | LL-082 | added | IM_SVG_Maker — black SVG / raster line-art → laser cut files + 3D-printable kintsugi plug; geometry-engine half of the custom-manufacturing flow | tasks.md#LL-082 |
| 2026-05-26 | LL-082 | done | Pipeline runs end-to-end on demo_W_black.svg and fox.jpg; Bill confirmed fox STL is correct and no venv needed; min-area/min-thickness threshold + queue-handoff parked for next iteration | Assembly_docs/IM_SVG_Maker/ |
| 2026-05-26 | LL-082 | progress | Size-floor thresholds (raster_min_island_area_mm2 + raster_min_feature_width_mm) shipped in raster preprocessor; erosion-as-predicate semantics avoids opening-fractures-at-thin-necks surprise | Assembly_docs/IM_SVG_Maker/im_svg_maker/raster.py |
| 2026-05-26 | LL-082 | progress | Color-SVG → black-SVG selector shipped (color_select.py + color_svg_to_black.py); verified end-to-end on Washington_Huskies_logo.svg through to laser+plug fab files | Assembly_docs/IM_SVG_Maker/im_svg_maker/color_select.py |
| 2026-05-26 | LL-083 | added | IM_SVG_Maker preprocessing port into infinity_mirror_visualizer — scoping doc + 6-chunk plan | Assembly_docs/IM_SVG_Maker/INTEGRATION_PLAN.md |
| 2026-05-26 | LL-083 | progress | Chunk 1/6 — Vitest harness + stub modules + sync-fixtures + 3 fixtures with canonicals; red baseline verified (5 failed/7 passed/6 todo) | Assembly_docs/IM_SVG_Maker/tests/fixtures/ |
| 2026-05-26 | LL-083 | progress | Chunk 2/6 — colorSelect.js ported (DOM walk, manual SVG fill inheritance, svgpath transform-baking, all common shape types); +svgpath dep; Huskies 4/4 green; test counts 3 failed/9 passed/6 todo | src/preprocess/colorSelect.js (visualizer repo) |
| 2026-05-26 | LL-083 | progress | Chunk 3/6 — svgParse.js ported (Three.js SVGLoader for curve flattening + clipper-lib pftEvenOdd for the XOR replacing shapely.symmetric_difference); new nested_holes fixture/canonical; svgParse.test.js verifies parity; counts 3 failed/18 passed/6 todo | src/preprocess/svgParse.js (visualizer repo) |
| 2026-05-26 | LL-083 | progress | Chunk 4/6 — raster.js ported (Jimp threshold + hand-rolled min-filter dilation + potrace npm for trace + svgParse for shell/hole assembly); all 3 fox parity tests green; counts 0 failed/21 passed/6 todo | src/preprocess/raster.js (visualizer repo) |
| 2026-05-26 | LL-083 | progress | Chunk 5/6 — manufacturability.js ported (nozzle round via clipper-lib ClipperOffset open-then-close; erosion-as-predicate width floor; area floor); 10 focused unit tests; sym-diff parity metric @ 35% regression bound; tiny_specks + hairline fixtures; all 37 tests pass, zero todos | src/preprocess/manufacturability.js (visualizer repo) |
| 2026-05-26 | LL-083 | done | Chunk 6/6 — PreprocessPanel.jsx React component (file upload + state machine + color picker + manufacturability sliders); ControlsPanel.jsx accepts topSection prop; npm run build passes (1003 modules, 5.83s); 37/37 tests still green. Browser-runtime potrace verification flagged as open follow-up | src/components/PreprocessPanel.jsx (visualizer repo) |
| 2026-05-26 | LL-084 | added | Visualizer code-review-driven cleanup pass; 19 tracked items spanning correctness, perf, security honesty, dead-code purge | infinity_mirror_visualizer repo |
| 2026-05-26 | LL-084 | progress | Cleanup commit — dead files purged (visualizer.js empty + test_svgs + 3 overlapping doc files); console.log + stale comments removed; mirrorSpacing → frameDepthMm rename; useFrame no-op fix; manufacturer endpoint → VITE_MANUFACTURER_ENDPOINT env var; export-ZIP de-duplication; tamper-proof-signature theater removed (SHA-256 integrity checksum + honest copy); THREE.Color scratch + frameBounds memo + React.memo on SvgIcon; SVG parse cache; code-split preprocessing via dynamic import (713 KB → 331 KB gz initial); SvgIcon split (extracted clipping helpers + emissive intensity helpers). 22 files, +516 / −1854 lines | commit 04aadf6 (infinity_mirror_visualizer) |
| 2026-05-26 | LL-084 | progress | Single render mode (flat fill); inline emissive intensity (revert of extraction that caused perceptual-uniformity regression); torture-test fixtures committed | commit ba6cd2a |
| 2026-05-26 | LL-084 | progress | Stroke-only SVGs route through raster preprocessor via canvas rasterization fallback | commit 1c07281 |
| 2026-05-26 | LL-084 | progress | PreprocessPanel becomes sole upload path (no ControlsPanel duplicate); vite-plugin-node-polyfills added so potrace runs in browser | commit 99aa81b |
| 2026-05-27 | LL-084 | progress | Vite build-time `define` stubs __dirname / __filename so jimp / potrace transitive deps stop crashing with "__dirname is not defined" at runtime; Custom Art panel repositioned below Icon section | commit fa7f715 |
| 2026-05-27 | LL-084 | progress | Vector stroke-to-fill in svgParse.js (ClipperOffset etOpenRound replaces lossy rasterize-then-trace for stroke-only SVGs); filename display in PreprocessPanel; nozzle defaults back to 0.6mm | commit 485274b |
| 2026-05-27 | LL-084 | done | Validated locally via mcp__Claude_Preview__* tools. Three real bugs caught + fixed: indexed-merge dropped index buffer (multi-island SVGs rendered as triangle salad); SvgIcon swapped from toShapes(false) to parseSvgToPolygons (winding-independent); resolveFill null default (snowflake fill:none CSS class no longer misreported as 1-fill). Verified dog/snowflake/cage/space-needle render correctly. Rainier (348K tris from 61 subpaths) deferred. Vercel deploys from main; both branches in sync | commit 2564ca1 |
| 2026-05-27 | LL-085 | added | Visualizer controls UX pass — sidebar improvements; scope open, start with a survey + prioritized list for Bill to pick from; kickoff prompt drafted | infinity_mirror_visualizer/src/components/ControlsPanel.jsx |
| 2026-05-27 | LL-085 | progress | Manufacturability rules per Bill — nozzle as discrete chip picker [off, 0.25, 0.40, 0.60, 0.80, 1.00]; min island default = ceil(π·(d/2)²×10)/10; min feature default = nozzle diameter; both follow nozzle until user overrides; yellow warning when any threshold = 0; maxLogoDimMm slider removed | commit f71a377 |
| 2026-05-27 | LL-085 | progress | Tier 1 polish — Reset all button + double-click slider label to reset; numeric input next to every slider with min/max clamp; Units toggle as mm/in button group; HexInput with on-blur validation + red invalid border | commit 4cf258d |
| 2026-05-27 | LL-085 | progress | Tier 2 PreprocessPanel — manufacturability sliders moved behind default-closed Advanced toggle; 150ms debounce on the applyManufacturability re-run effect; inline processed-SVG thumbnail in the ready stage | commit 4851556 |
| 2026-05-27 | LL-085 | progress | URL hash save/share — all SHARED_KEYS config serialized to #cfg=base64(json) via history.replaceState; restored once on mount via useState lazy initializer; Copy share link button in Export section with "Link copied!" flash | commit 1907b91 |
| 2026-05-27 | LL-085 | progress | Tier 4 polish — multi-color picker (toggle ✓ then Apply N colors); Auto-orbit folded into Frame Controls; SHA-256 integrity hash copy fix; Edge Thickness regrouped under Appearance subsection of Icon Transform | commit b451db4 |
| 2026-05-27 | LL-085 | progress | Edge Thickness now actually does something for custom SVGs — dilates polygons by edgeThickness/2 in scene-space via offsetPolygons (promoted to public preprocess export); slider min 0.05 → 0; thumbnail Hide/Show toggle | commit d5ae16a |
| 2026-05-27 | LL-085 | progress | Polish pass — Edge Thickness step 0.05 → 0.01; Frame Depth label respects units toggle; Bloom Effect toggle moved out of floating canvas overlay into Frame Controls next to Auto-orbit | commit d396772 |
| 2026-05-27 | LL-085 | progress | Custom Art modal wizard — upload + color-pick + manufacturability pulled out of sidebar into CustomArtModal wrapping PreprocessPanel; sidebar shows 64x64 thumbnail + Edit button; modal stays mounted after first open so internal state survives close+reopen | commit 840a8e0 |
| 2026-05-27 | LL-085 | progress | Named preset save/load — PresetsSection at top of panel; inline naming input; localStorage["imv:presets"] = {name, cfg, savedAt}[]; click name to apply, × to delete; same-name save overwrites; refreshes on window focus | commit 635e368 |
| 2026-05-27 | LL-085 | progress | Mobile drawer — ControlsLayout.css; above 900px panel is normal 320px flex child, below it becomes a fixed-position slide-in drawer pinned right with hamburger toggle + dark scrim | commit ce05461 |
| 2026-05-27 | LL-085 | progress | File picker delay fix + caption text — preload preprocess module on PreprocessPanel mount; Canvas frameloop="never" while Custom Art modal is open (Three.js render loop was delaying OS file dialog); caption "Preview — black = illuminated segments, white = mirror base" | commit 8a46e4e |
| 2026-05-27 | LL-085 | progress | Light Intensity slider — 0–3× multiplier (default 1.0, step 0.05) threading through Scene → Box → ReflectionLayers → SvgIcon and into the URL hash / presets / Reset all | commit a382470 |
| 2026-05-27 | LL-085 | progress | Emission perceptual uniformity — replaced six-constant hand-tuned Gaussian curve with principled inverse-luminance formula `emission = BASELINE / intrinsic_luminance^POWER` (POWER=1.0 gives mathematical uniformity, BASELINE=3.4 calibrated against the previous curve's default-cyan emission). Programmatic 64-hue WebGL readback attempted but blocked by headless preview's rAF being paused — derived formula from first principles instead | commit 8a8a08f |
| 2026-05-27 | LL-085 | progress | Default lightIntensity 1.0 → 0.5 — new uniform formula lands brighter than the old hand-tuned curve under bloom; 0.5 gives the previous overall feel as a baseline; slider still reaches 3.0 if user wants more glow | commit b739ebb |
| 2026-05-27 | LL-085 | progress | InfoPopover top-left — Layered Logic brand card with one-para description + four-bullet how-to + footer link to layeredlogic.cc; italic Berkeley Mono per brand decisions; dismissable, sticky via localStorage["imv:info-dismissed"] | commit f61a57b |
| 2026-05-27 | LL-085 | done | InfoPopover ⓘ glyph swapped for inline SVG icon — Unicode U+24D8 was falling through to whatever emoji bitmap font; replaced with hand-drawn vector (outer circle + stem + dot). Required `preview_stop`/`preview_start` to clear a stale Vite cache state | commit 9b7ecaa |
| 2026-06-04 | LL-086 | started | Batch sheet-nesting work begun — maximize one 300×300 acrylic sheet per laser run instead of four separate 150×150 tile setups | Assembly_docs/IM_SVG_Maker/scripts/tile_sheet.py |
| 2026-06-04 | LL-086 | progress | Three input preprocessors: stroke_svg_to_black (LL mark strokes→bands), outline_black_svg (empowder fill→3mm ribbon), ll_flourish (frozen P5 histogram, direction-fixed to grow off each L's outer side) | Assembly_docs/IM_SVG_Maker/scripts/ |
| 2026-06-04 | LL-086 | progress | Solid red cut color — write_dxf + tile_sheet entities now ACI 1 + true-color 0xFF0000 on red layers (were colorless/ByLayer white); also bumped LL-082 last_engaged | Assembly_docs/IM_SVG_Maker/im_svg_maker/laser_export.py |
| 2026-06-04 | LL-086 | done | tile_sheet.py nests 4 tiles 2×2 (+ --squares-only frames); shipped sheet_gap0.dxf (300.0 exact) + sheet.dxf (300.5, 0.5mm gap) + squares-only frames, all red. Open: pick gap by real stock size | Assembly_docs/IM_SVG_Maker/out/sheet_gap0.dxf |
| 2026-06-05 | LL-087 | started | HA re-integration via existing firmware — chose HACS custom integration (light entity over the WS control protocol) after mapping the firmware API; rejected MQTT/ESPHome (would need firmware changes) | homeassistant/custom_components/layered_logic_mirror/ |
| 2026-06-05 | LL-087 | progress | Built integration: const/protocol/coordinator/light/config_flow/__init__ + manifest (zeroconf + manual IP, local_push) + strings/translations + hacs.json + README. protocol.py ports ws-client.ts frameFor + hmac.ts byte-for-byte; zero external deps | homeassistant/ |
| 2026-06-05 | LL-087 | done | verify_mirror.py ALL-PASS on real mirror (192.168.5.229, open mode): /api/info + get_state + set_state on/brightness/base_color/pattern_id, each confirmed via authoritative state broadcast. set_state response is best-effort/stale → assert on broadcasts. Paired-mode HMAC + HA-side install still unverified on silicon | homeassistant/verify_mirror.py |
| 2026-06-05 | LL-087 | progress | Spun integration into standalone HACS repo ../layered-logic-mirror-ha (repo-root custom_components + hacs.json + info.md + MIT LICENSE + .gitattributes + hassfest/HACS CI + scripts/verify_mirror.py, re-ran ALL-PASS). git init on main + staged; first commit/push deferred until mirror verified live in HA (Bill). Removed in-study homeassistant/ copy | ../layered-logic-mirror-ha |
| 2026-06-05 | LL-087 | progress | Installed in Bill's HA (HA OS, Samba add-on). Fixed coordinator concurrency bug: initial get_state awaited before read loop started → "no response" setup loop; now snapshot runs concurrent with _read_loop. Entity green, controls mirror | ../layered-logic-mirror-ha/custom_components/layered_logic_mirror/coordinator.py |
| 2026-06-05 | LL-087 | done | Genericized dev-tool IP examples (no device-specific data in repo) and published public: https://github.com/bowbikes/layered-logic-mirror-ha (topics, MIT). CI workflow held back — gh token lacks workflow scope; pending gh auth refresh -s workflow + follow-up commit | https://github.com/bowbikes/layered-logic-mirror-ha |
| 2026-06-05 | LL-087 | done | CI green 8/8. Bill added validate.yml via GitHub web (token scope workaround); HACS brands check satisfied by local brand assets rendered from the canonical mark (scripts/render_brand.py → custom_components/.../brand/icon+logo png). hassfest + HACS validation both pass | https://github.com/bowbikes/layered-logic-mirror-ha/actions |
| 2026-06-05 | LL-087 | progress | HACS default-store submission: created release v0.1.0; opened PR hacs/default#8245 (adds bowbikes/layered-logic-mirror-ha, sorted insert after Bouni/luxtronik). All 11 PR checks GREEN (Sorted/Releases/HACS action/Hassfest/Owner/...), state OPEN + MERGEABLE, awaiting maintainer merge. home-assistant/brands PR NOT needed — local brand/icon.png + HA brands-proxy (since 2026.3) satisfy brands | https://github.com/hacs/default/pull/8245 |
