layered-logic/infinity-mirror/docs/service-blueprint.md

---
title: Service Blueprint
type: hcde-artifact
phase: 3
week: 7
date: 2026-05-13
status: draft
tags: [hcde, service-blueprint, customer-journey, custom-order, operations]
---

# Service Blueprint — Layered Logic Infinity Mirror

**Prepared by:** William White, Founder & Lead Designer
**Date:** May 13, 2026
**Scope:** End-to-end customer journey from first impression to end-of-life, including the bespoke custom-order branch ([LL-054](../tasks.md#LL-054)).

---

## What this document is
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
