layered-logic/infinity-mirror/App/v1/assets/color-wheel.png

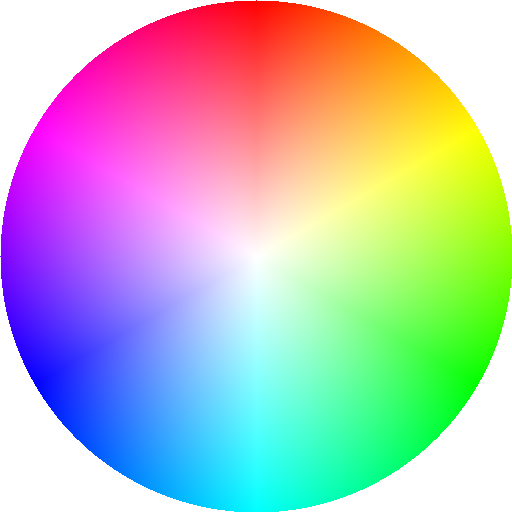
App/v1/assets/color-wheel.png
