layered-logic/infinity-mirror/Assembly_docs/basic_housing/housing_layout_v1.png

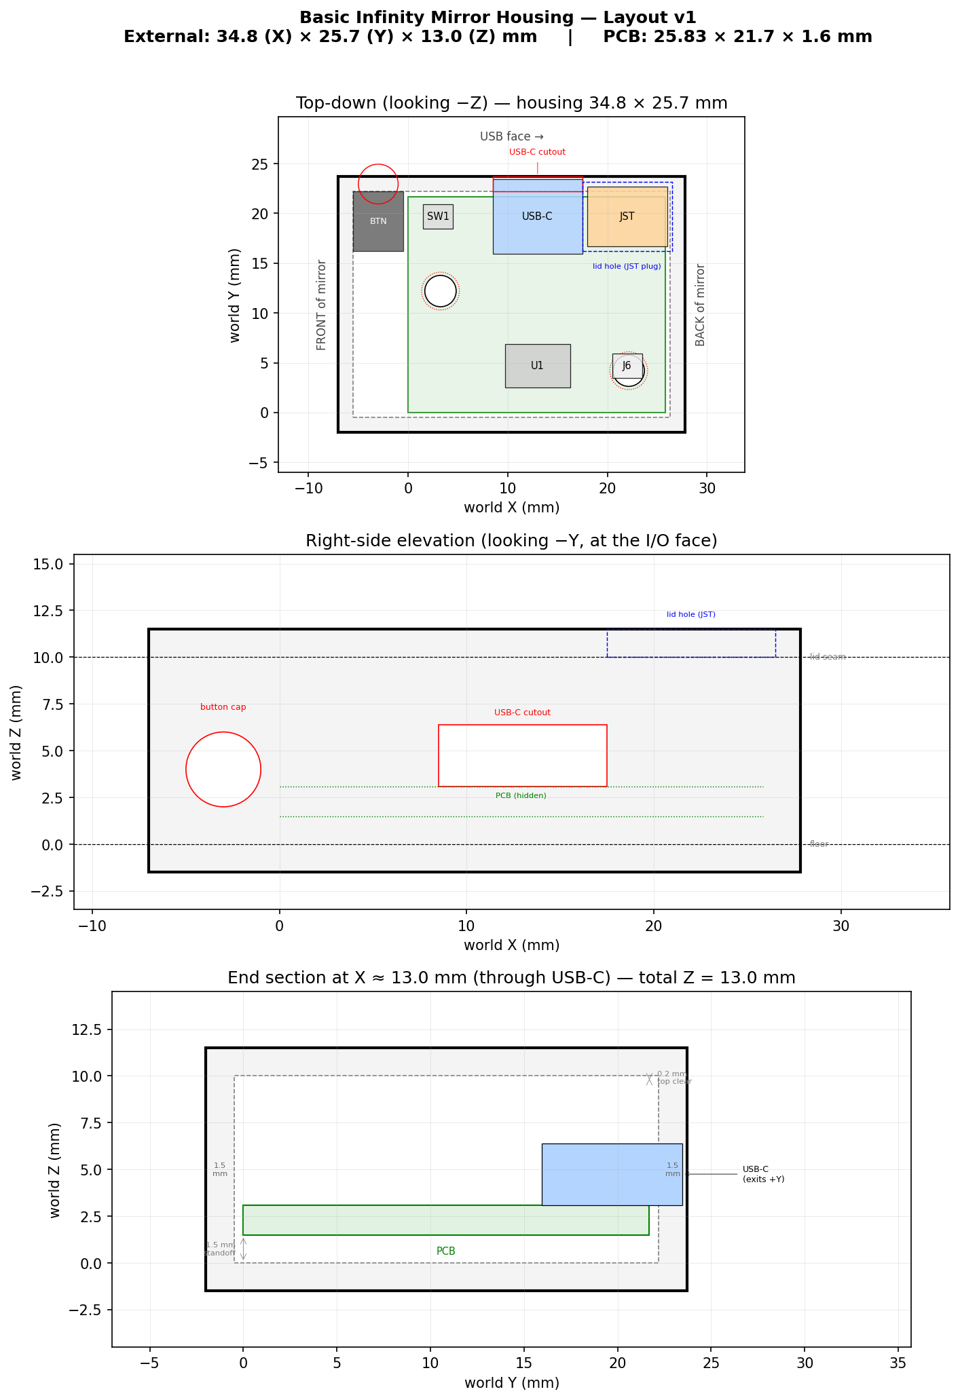
Assembly_docs/basic_housing/housing_layout_v1.png
