layered-logic/infinity-mirror/Assembly_docs/IM_SVG_Maker/cut_lines_preview.png

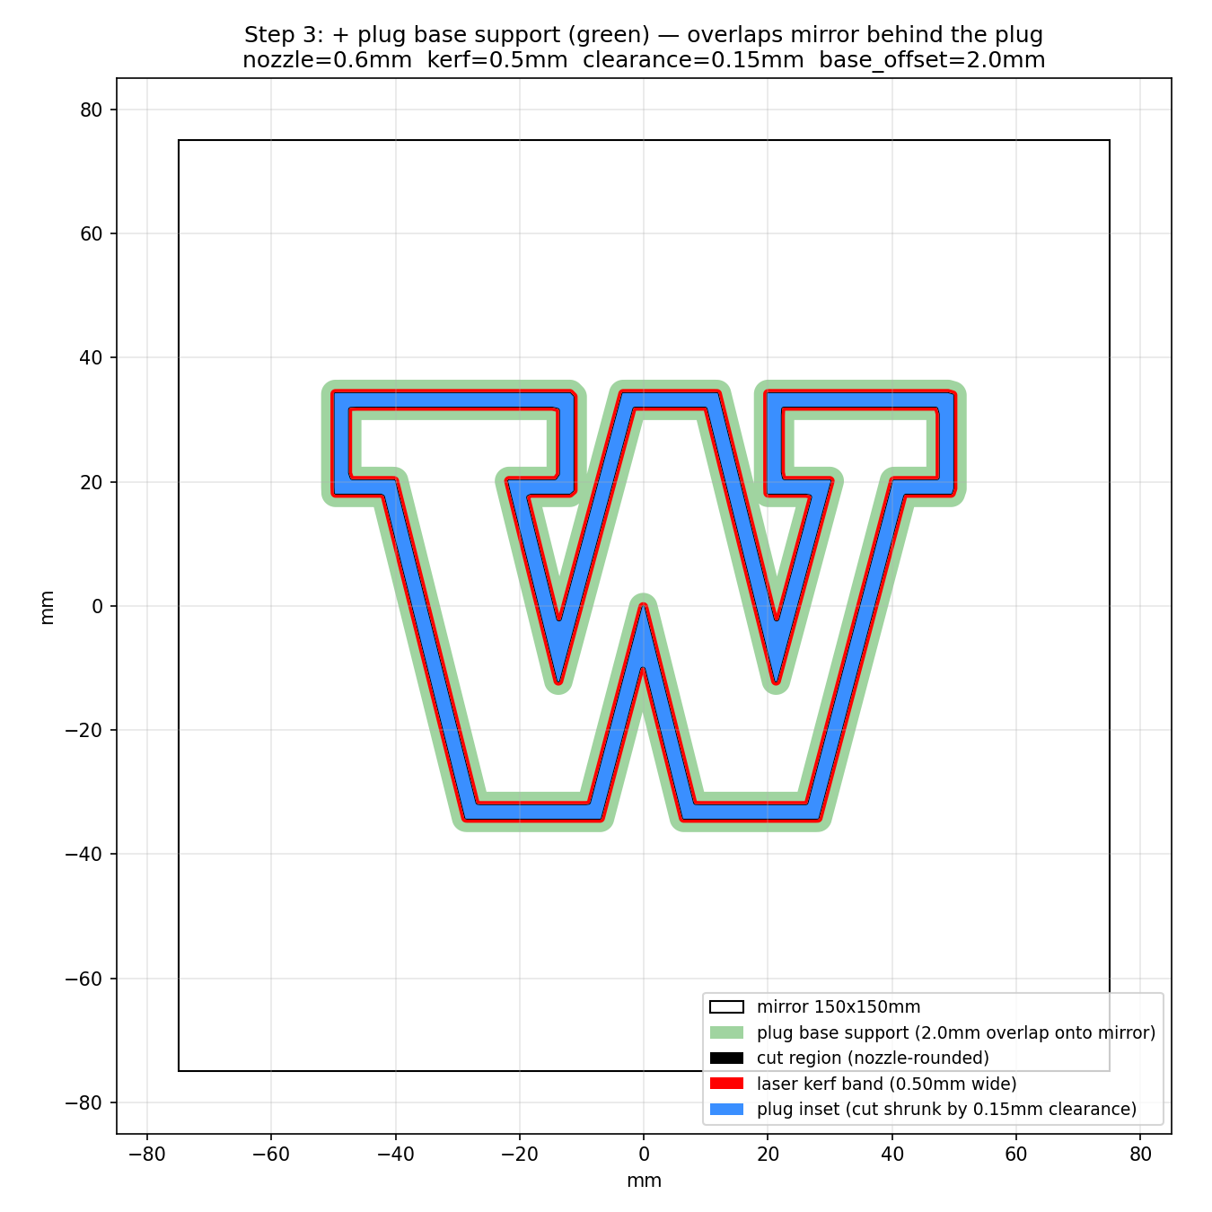
Assembly_docs/IM_SVG_Maker/cut_lines_preview.png
