layered-logic/infinity-mirror/Assembly_docs/IM_SVG_Maker/fox_preview.png

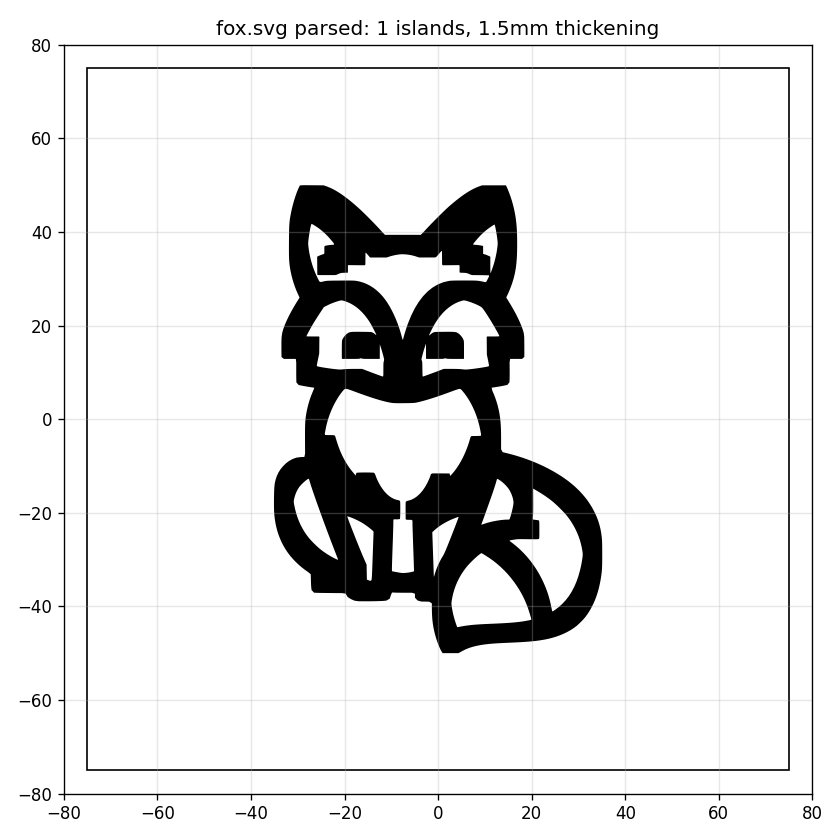
Assembly_docs/IM_SVG_Maker/fox_preview.png
