layered-logic/infinity-mirror/Assembly_docs/IM_SVG_Maker/inputs/Empowder/empowder_outline_4mm_preview.png

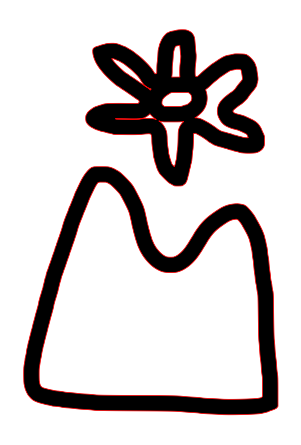
Assembly_docs/IM_SVG_Maker/inputs/Empowder/empowder_outline_4mm_preview.png
