layered-logic/infinity-mirror/Assembly_docs/IM_SVG_Maker/inputs/Empowder/extracted_0.png

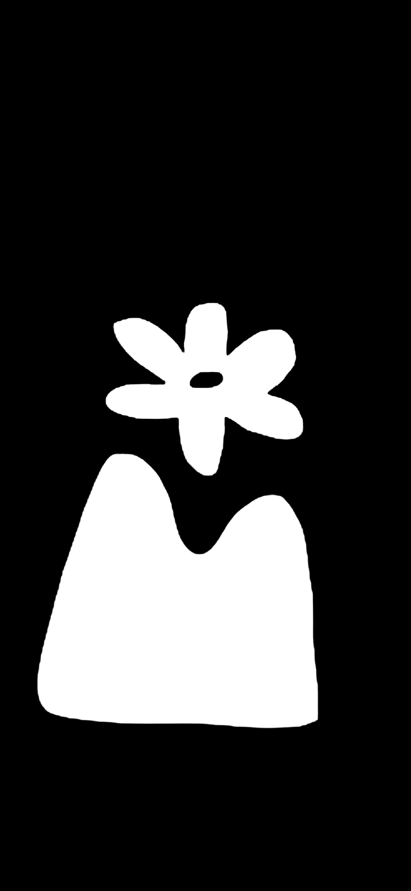
Assembly_docs/IM_SVG_Maker/inputs/Empowder/extracted_0.png
