layered-logic/infinity-mirror/Assembly_docs/IM_SVG_Maker/inputs/LayeredLogic/flourish_direction_compare.png

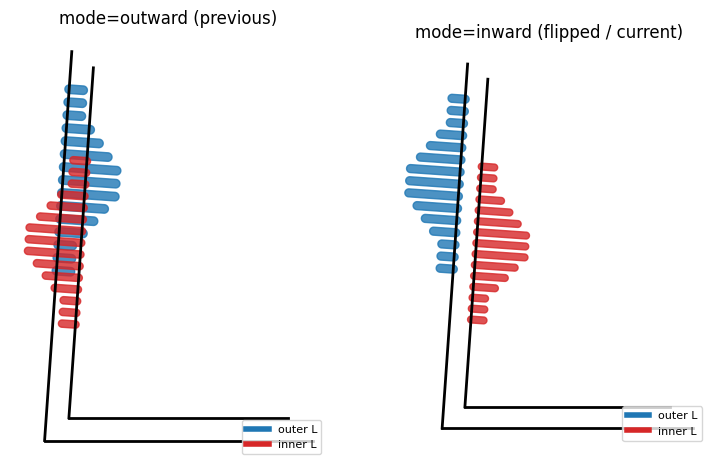
Assembly_docs/IM_SVG_Maker/inputs/LayeredLogic/flourish_direction_compare.png
