layered-logic/infinity-mirror/Assembly_docs/IM_SVG_Maker/inputs/LayeredLogic/ll_flourish_60_same_preview.png

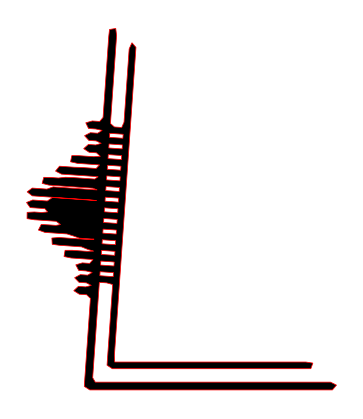
Assembly_docs/IM_SVG_Maker/inputs/LayeredLogic/ll_flourish_60_same_preview.png
