layered-logic/infinity-mirror/Assembly_docs/packaging/compare_baseline.png

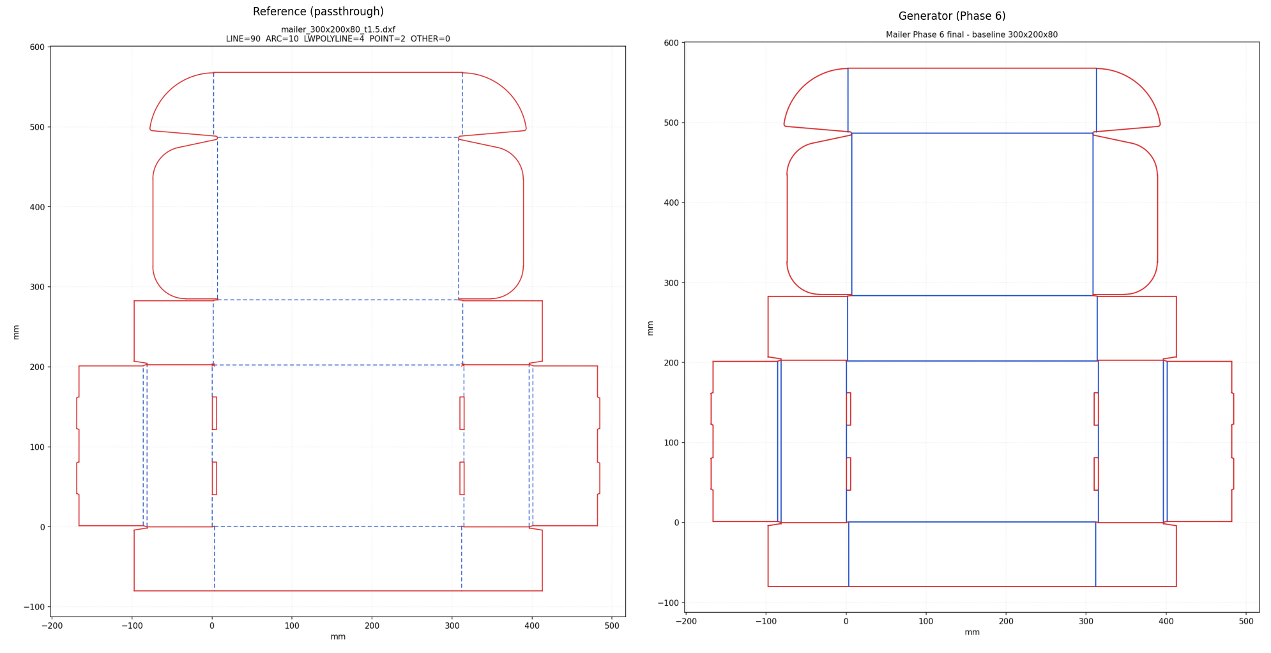
Assembly_docs/packaging/compare_baseline.png
