layered-logic/infinity-mirror/Assembly_docs/packaging/gen_insert_1slot_300x200x80.png

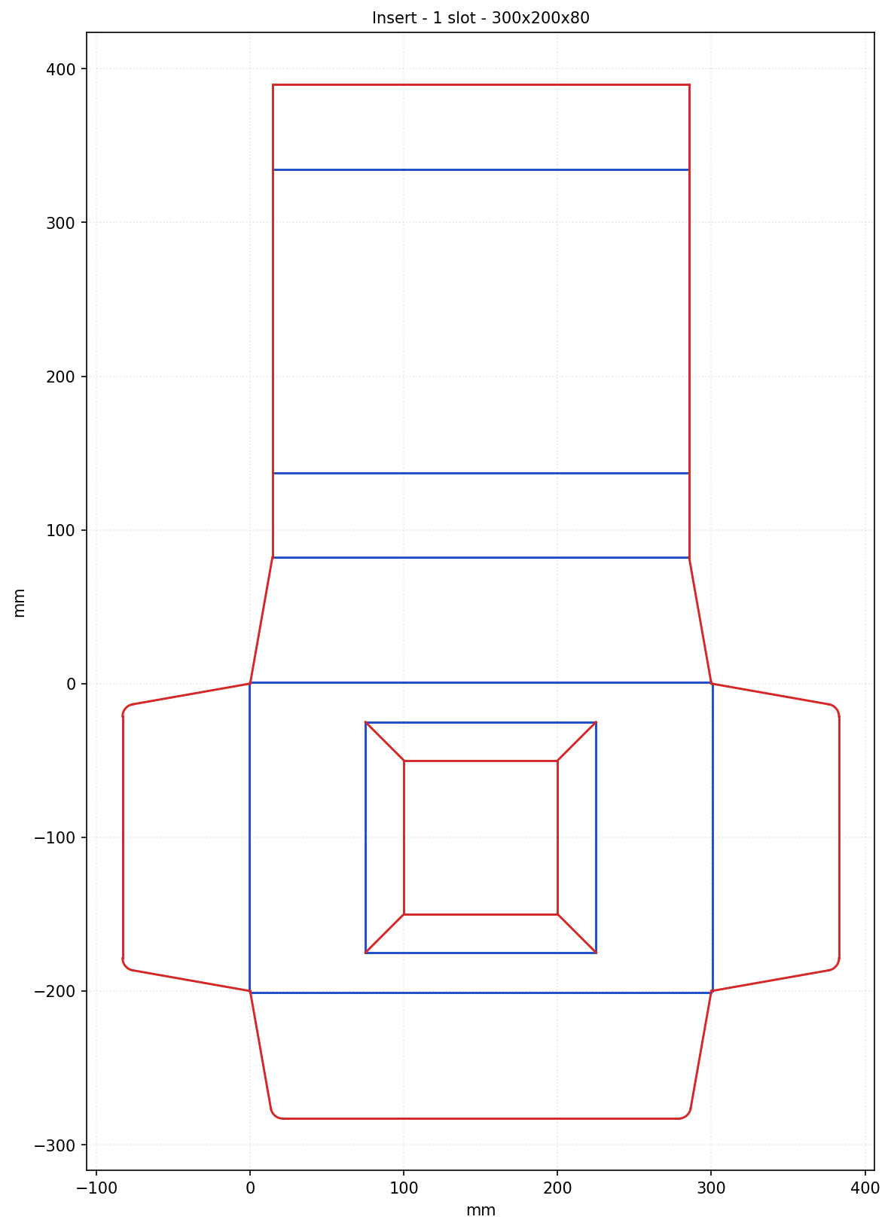
Assembly_docs/packaging/gen_insert_1slot_300x200x80.png
