layered-logic/infinity-mirror/Assembly_docs/packaging/gen_insert_2slot_300x200x80.png

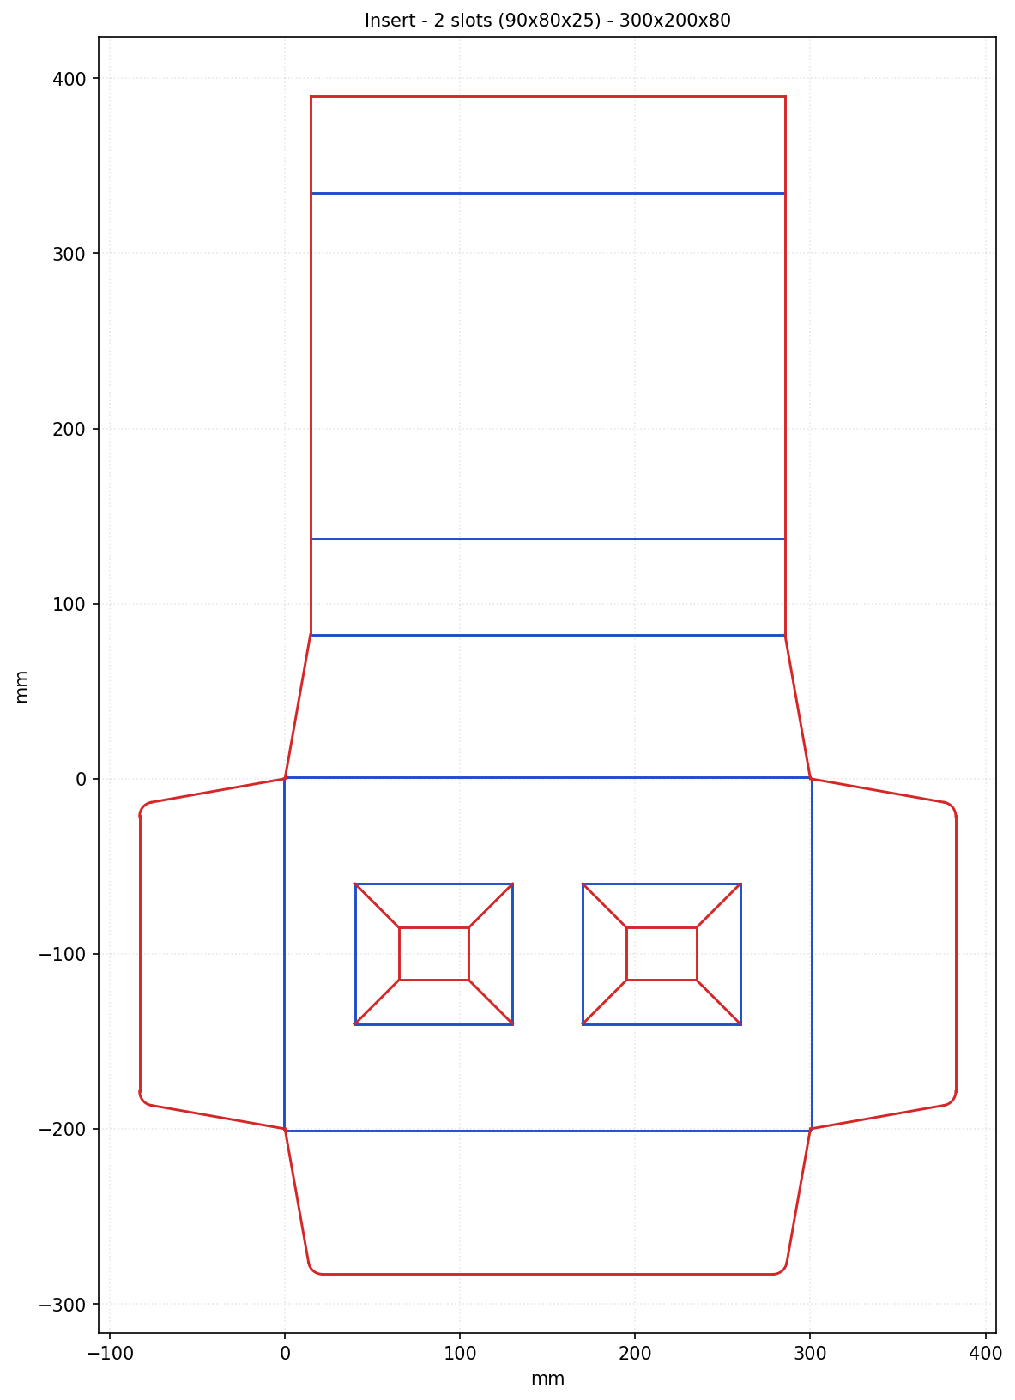
Assembly_docs/packaging/gen_insert_2slot_300x200x80.png
