layered-logic/infinity-mirror/Assembly_docs/packaging/gen_insert_asym_2slot.png

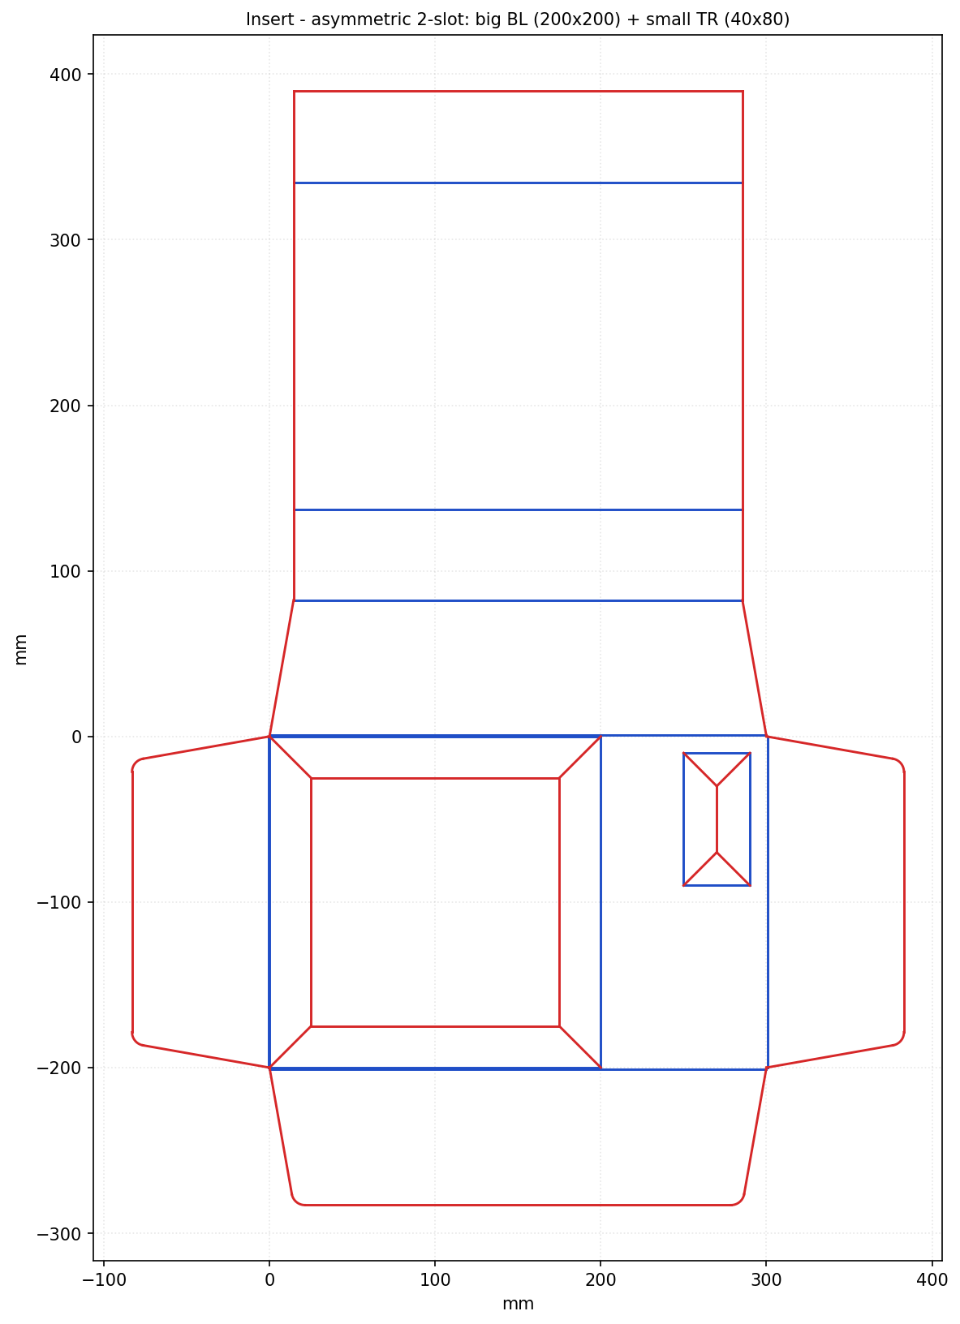
Assembly_docs/packaging/gen_insert_asym_2slot.png
