layered-logic/infinity-mirror/Assembly_docs/packaging/gen_insert_asym_2slot_250x280.png

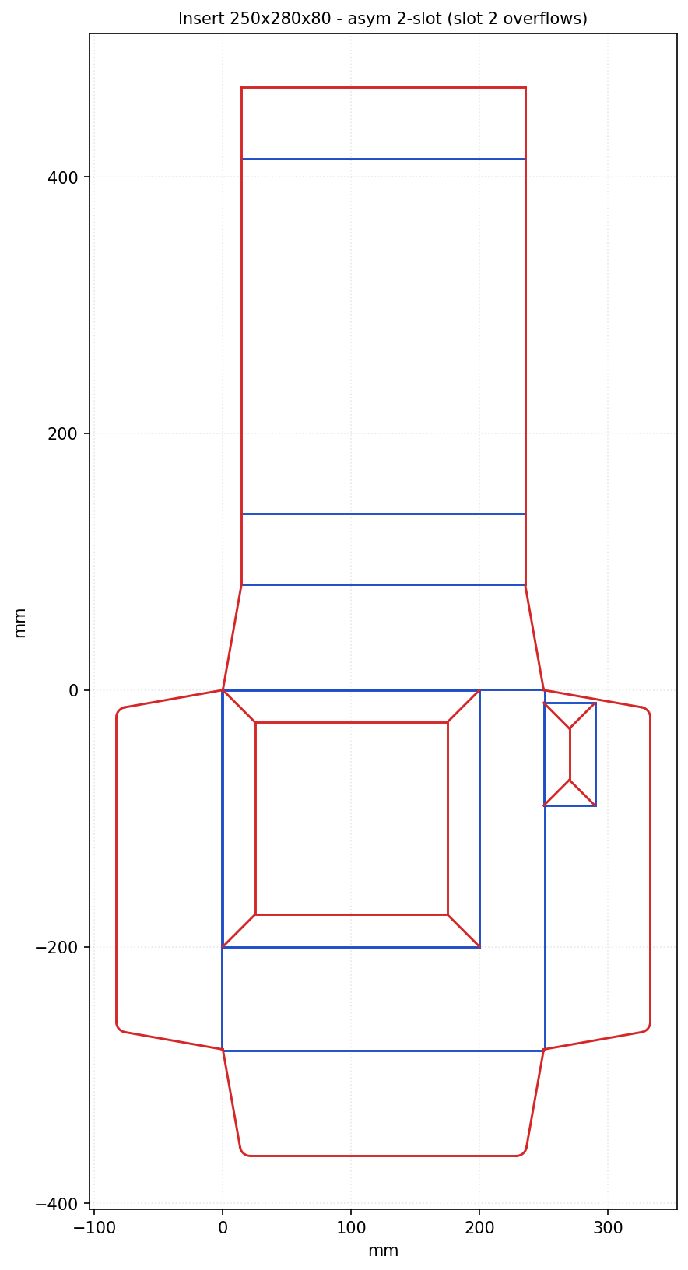
Assembly_docs/packaging/gen_insert_asym_2slot_250x280.png
