layered-logic/infinity-mirror/Assembly_docs/packaging/gen_insert_phase3_300x200x80.png

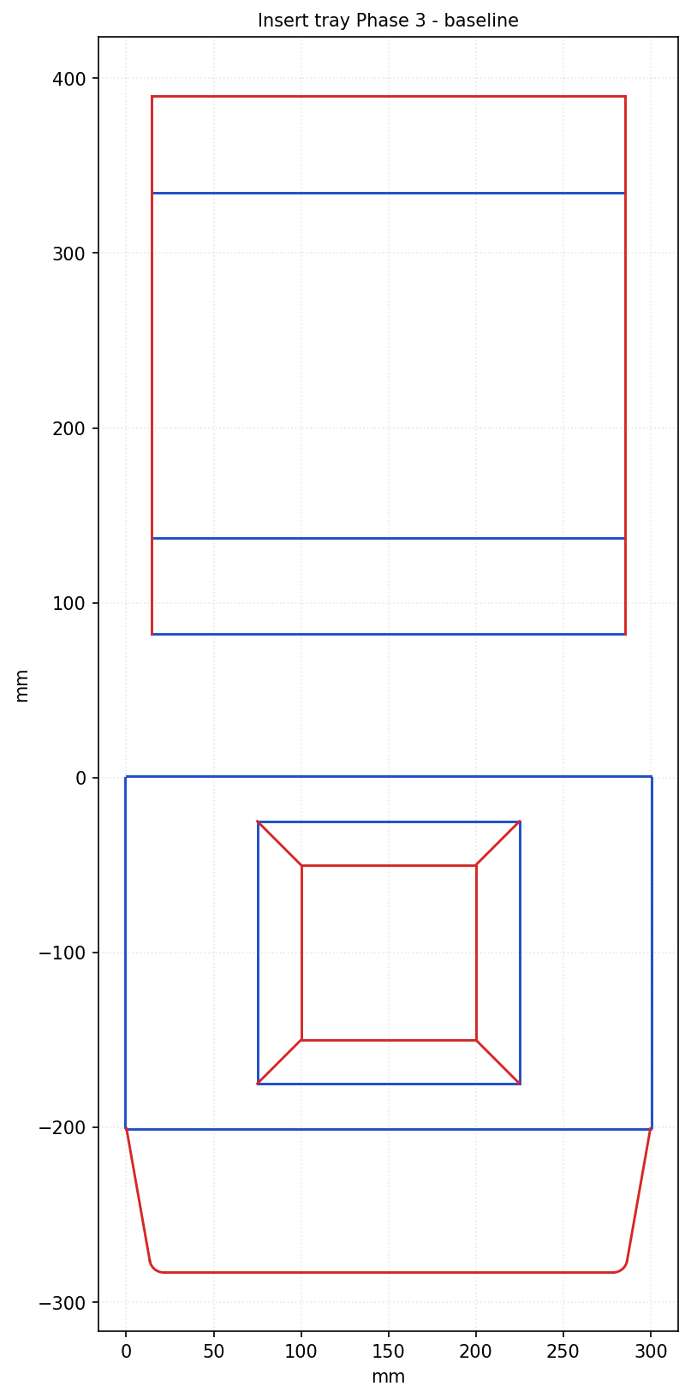
Assembly_docs/packaging/gen_insert_phase3_300x200x80.png
