layered-logic/infinity-mirror/Assembly_docs/packaging/gen_mailer_phase3_225x225x60.png

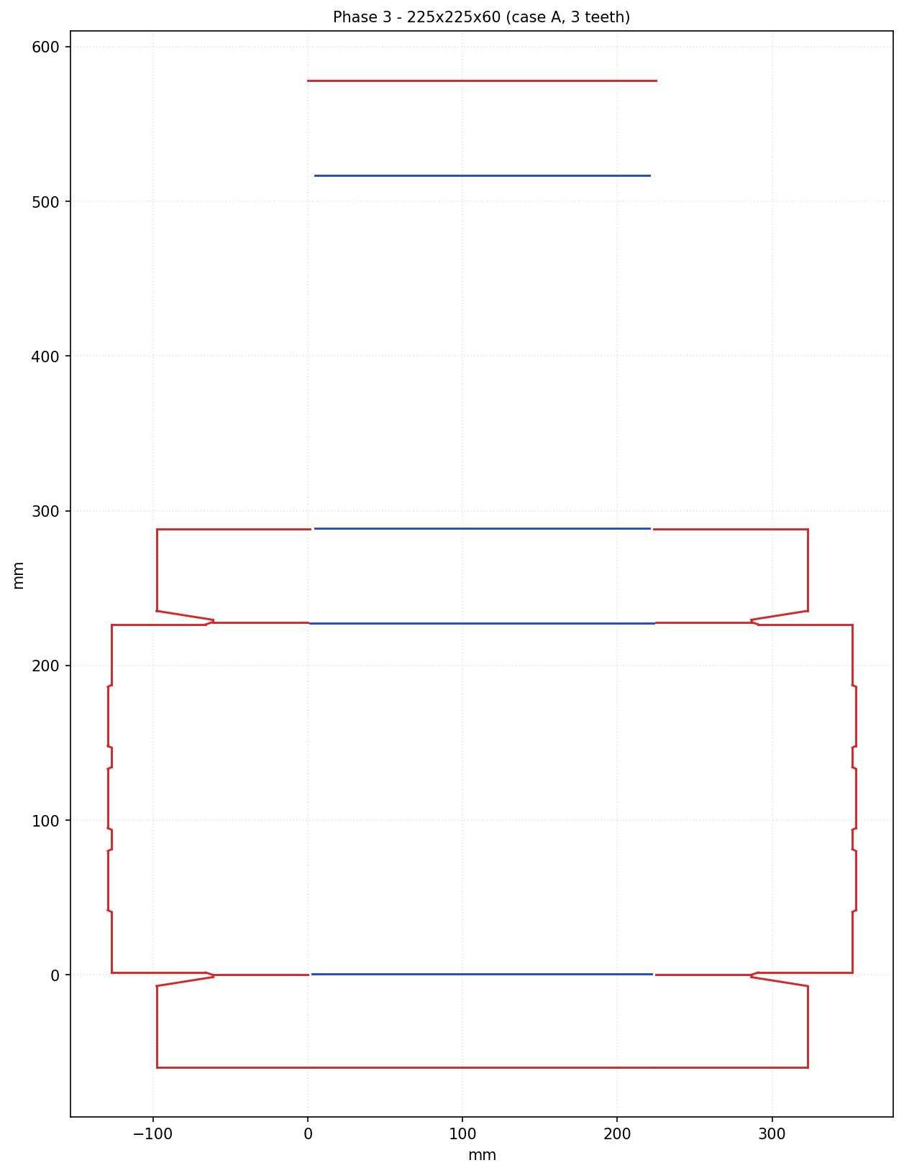
Assembly_docs/packaging/gen_mailer_phase3_225x225x60.png
