layered-logic/infinity-mirror/Assembly_docs/packaging/gen_mailer_phase4_225x225x60.png

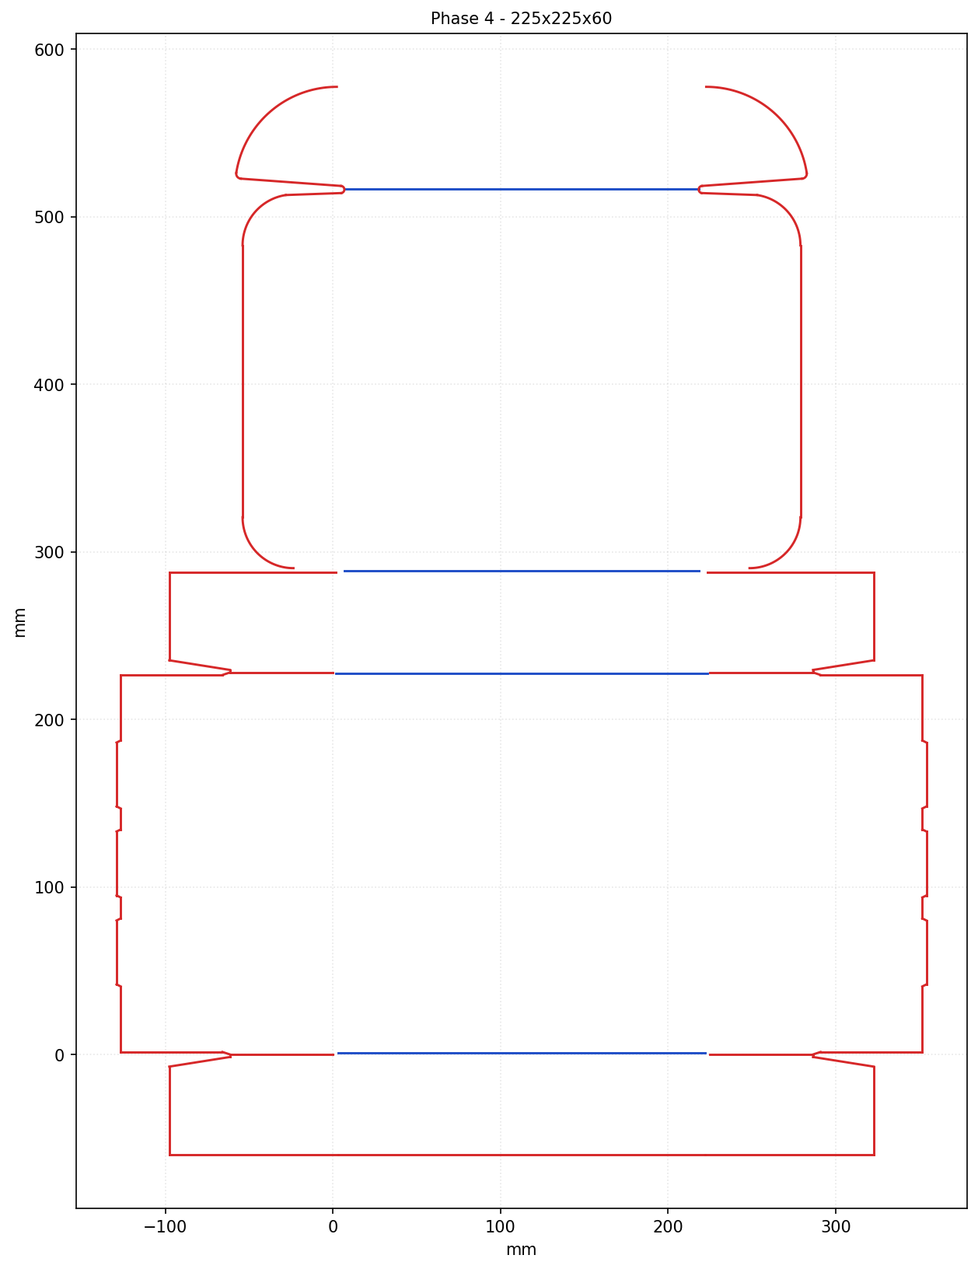
Assembly_docs/packaging/gen_mailer_phase4_225x225x60.png
