layered-logic/infinity-mirror/Assembly_docs/packaging/gen_mailer_phase4_300x200x80.png

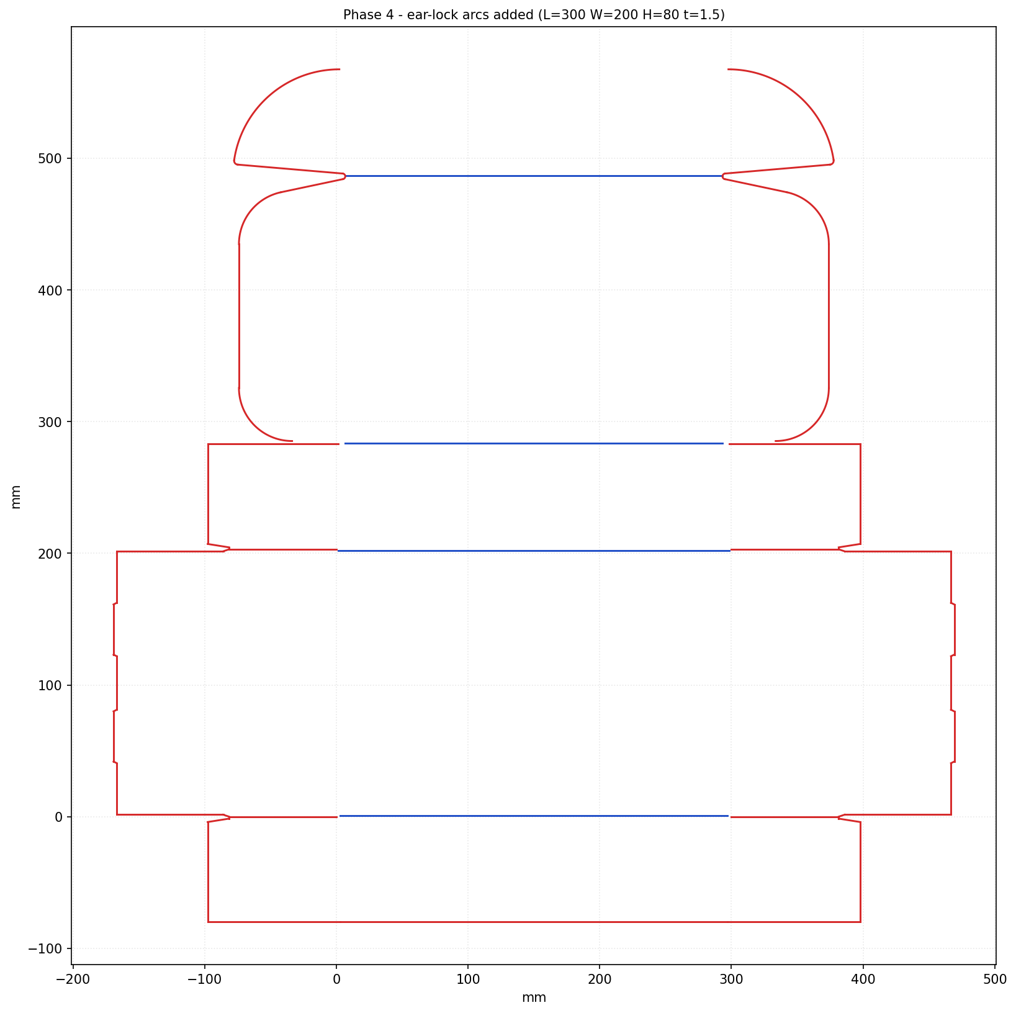
Assembly_docs/packaging/gen_mailer_phase4_300x200x80.png
