layered-logic/infinity-mirror/Assembly_docs/packaging/gen_mailer_phase5_225x225x60.png

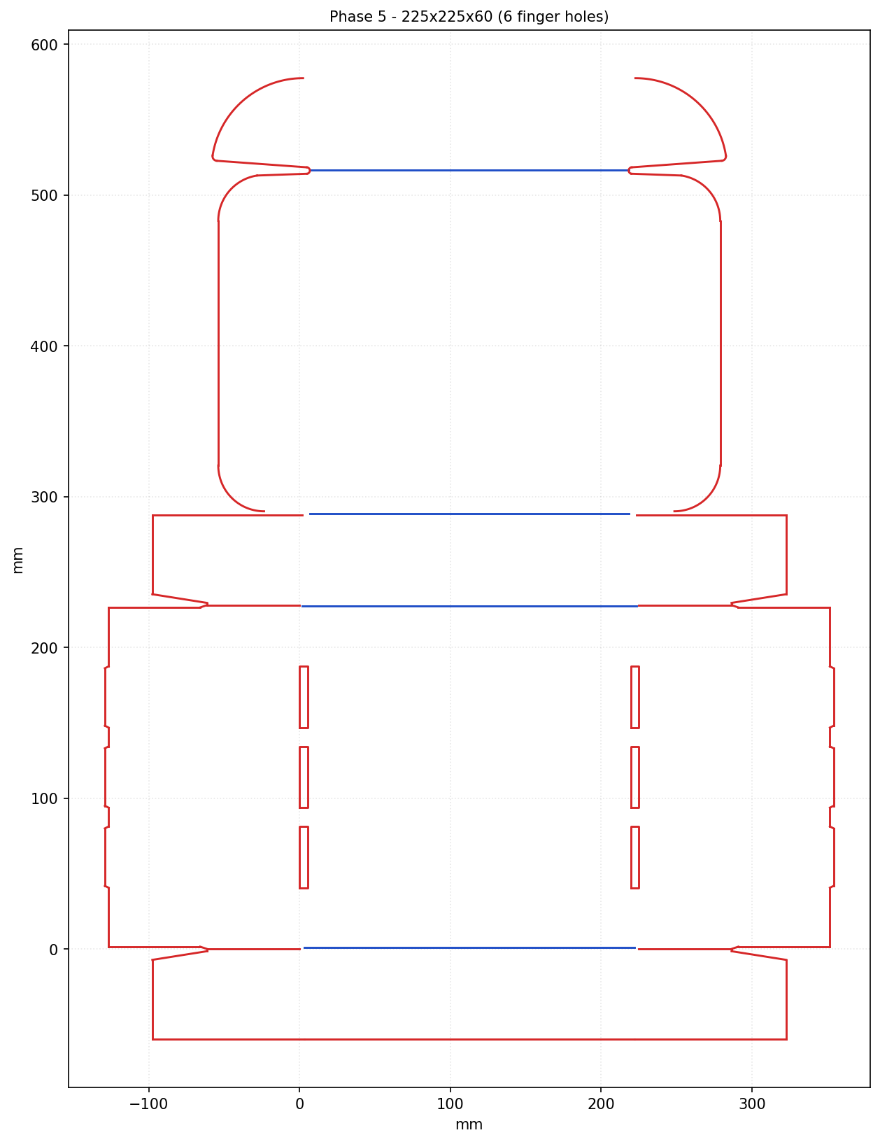
Assembly_docs/packaging/gen_mailer_phase5_225x225x60.png
