layered-logic/infinity-mirror/Assembly_docs/packaging/gen_mailer_phase5_300x200x120.png

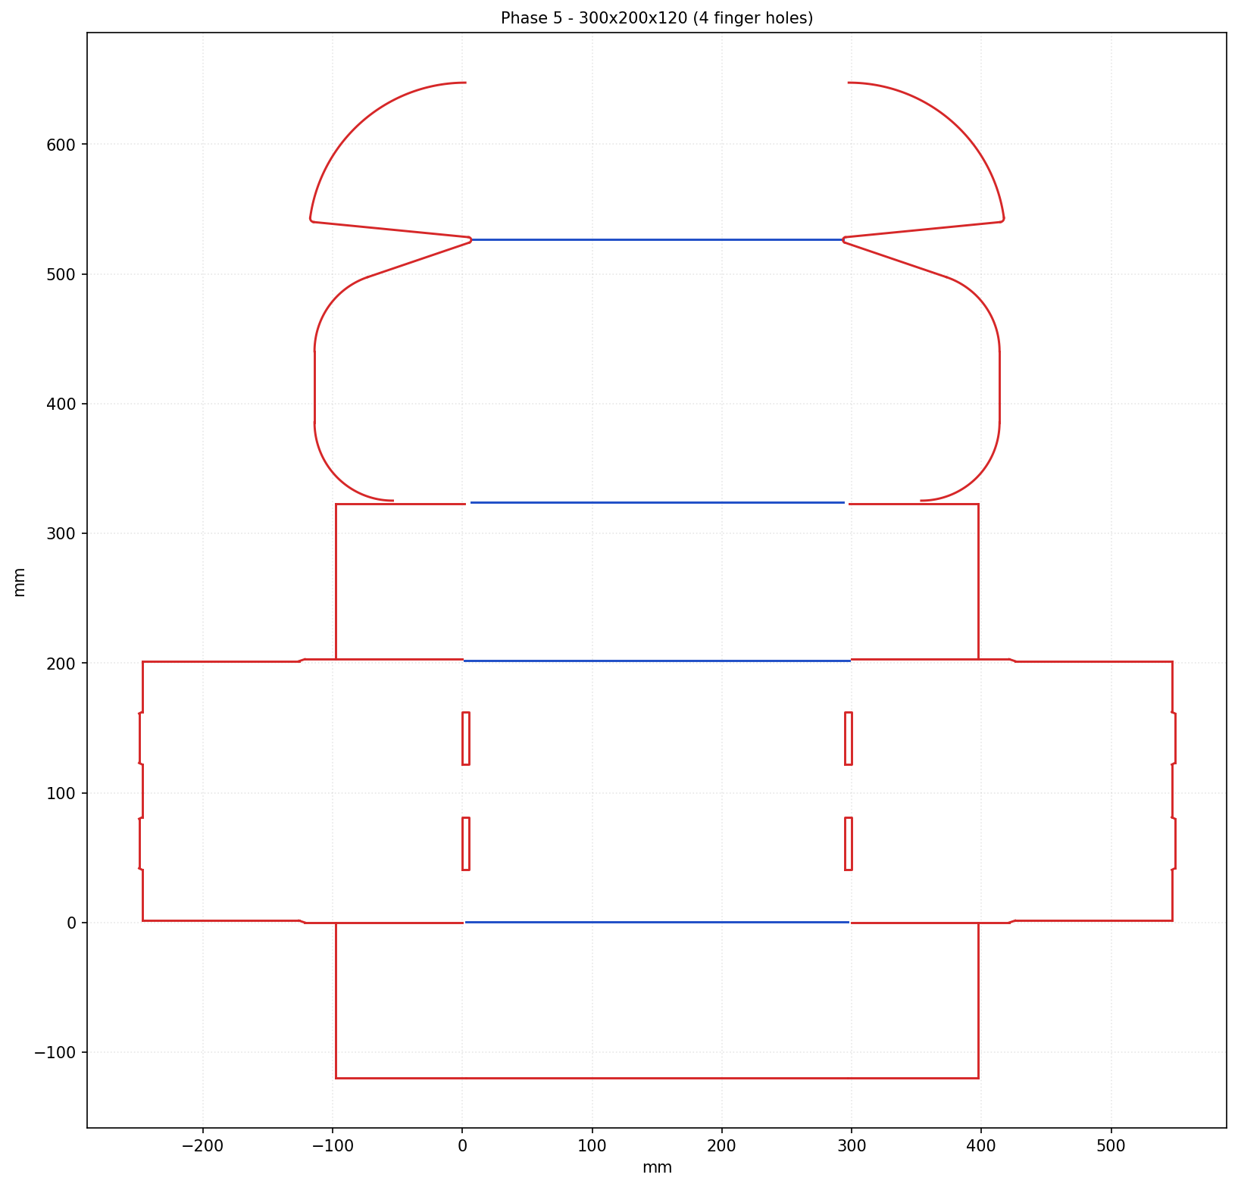
Assembly_docs/packaging/gen_mailer_phase5_300x200x120.png
