layered-logic/infinity-mirror/Assembly_docs/packaging/gen_mailer_phase6_225x225x60.png

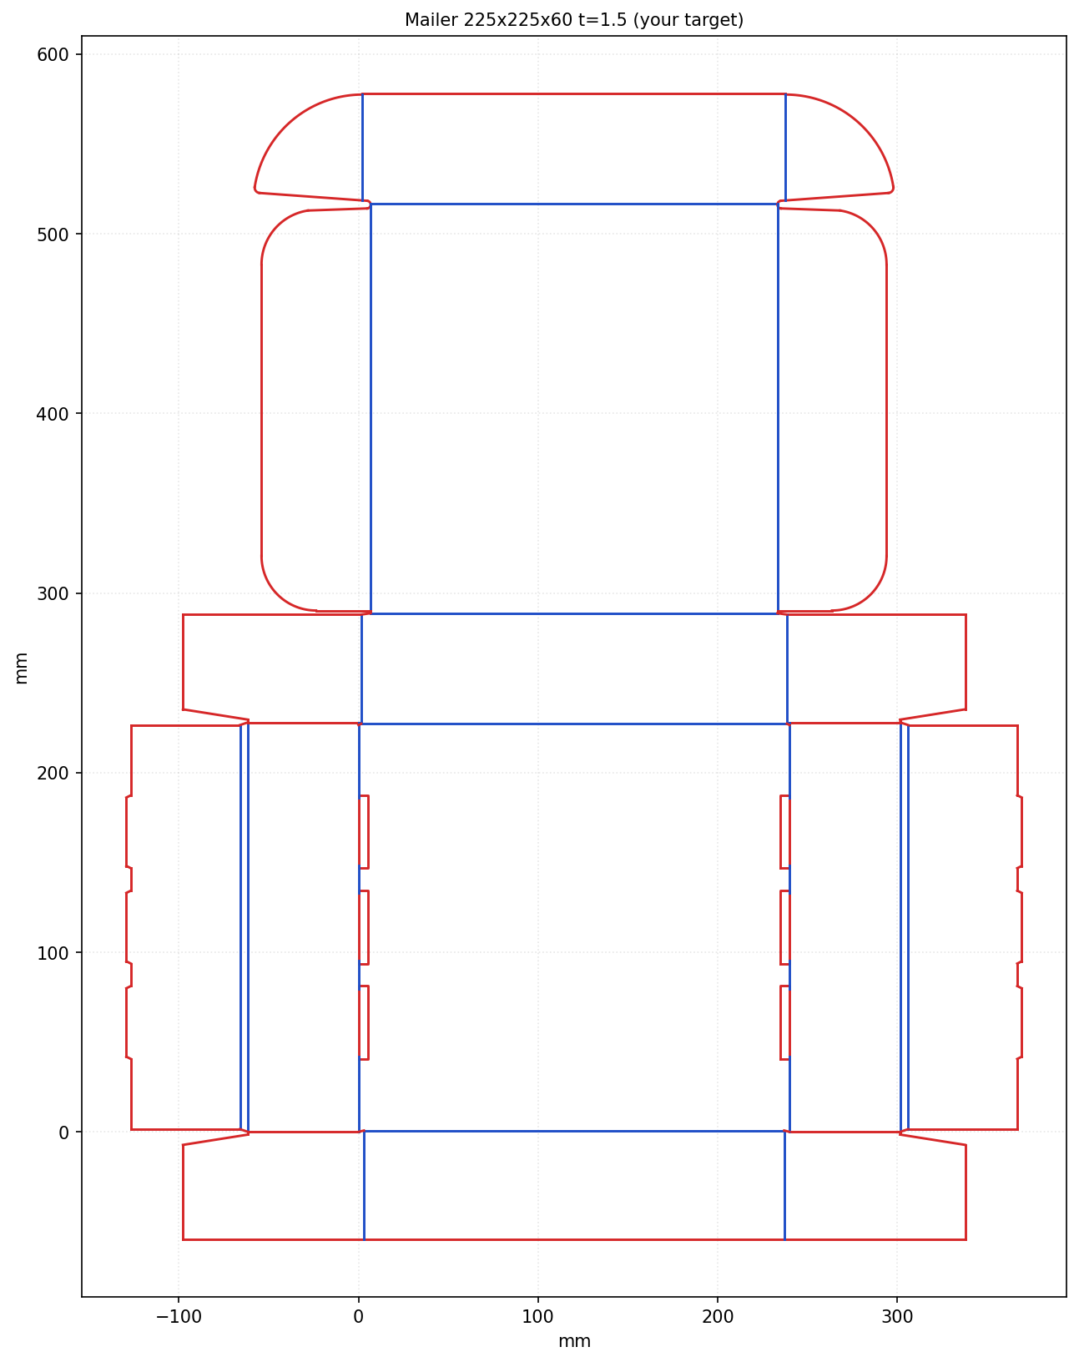
Assembly_docs/packaging/gen_mailer_phase6_225x225x60.png
