layered-logic/infinity-mirror/Assembly_docs/packaging/gen_mailer_phase6_300x200x80_t3.png

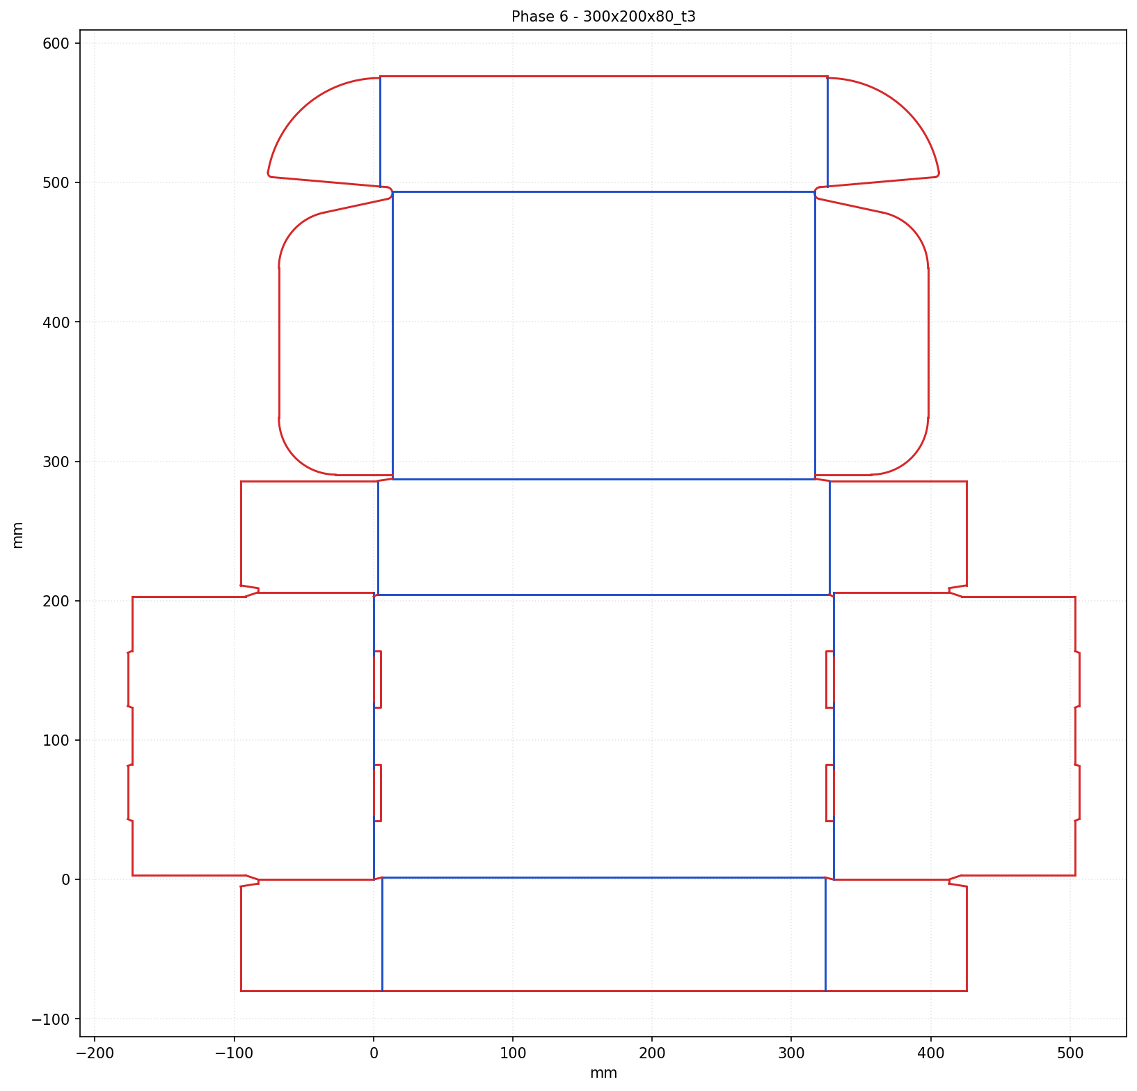
Assembly_docs/packaging/gen_mailer_phase6_300x200x80_t3.png
