layered-logic/infinity-mirror/Assembly_docs/packaging/generated_mailer_225x225x60_t1.5.png

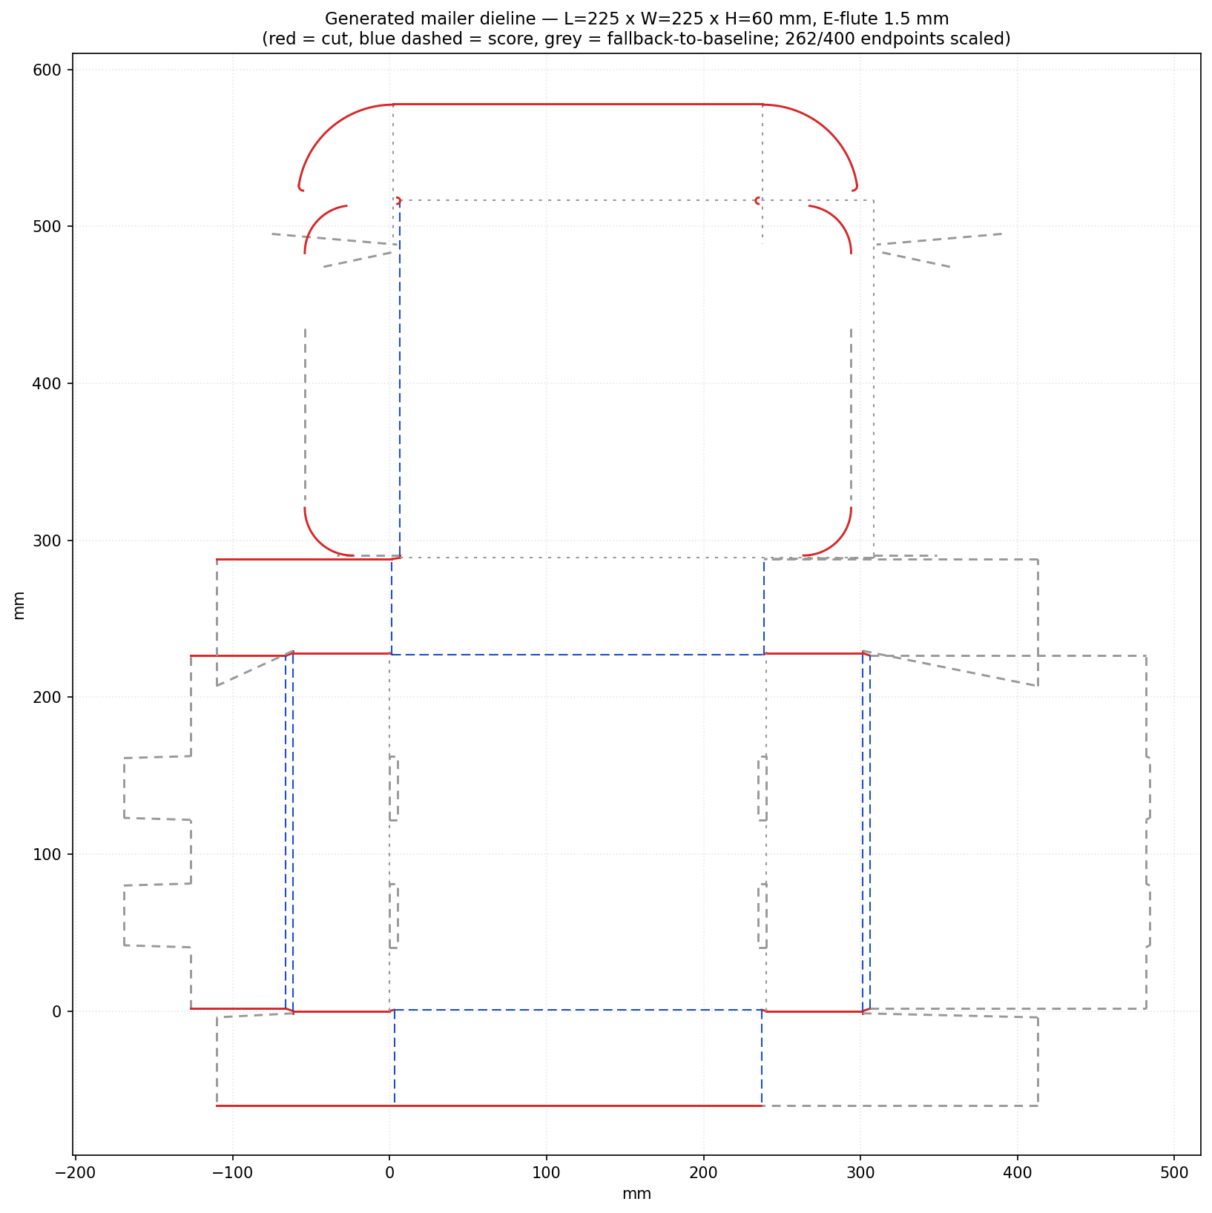
Assembly_docs/packaging/generated_mailer_225x225x60_t1.5.png
