layered-logic/infinity-mirror/Assembly_docs/packaging/passthrough_insert_300x200x80_t1.5_slot200x100x50_IH30.png

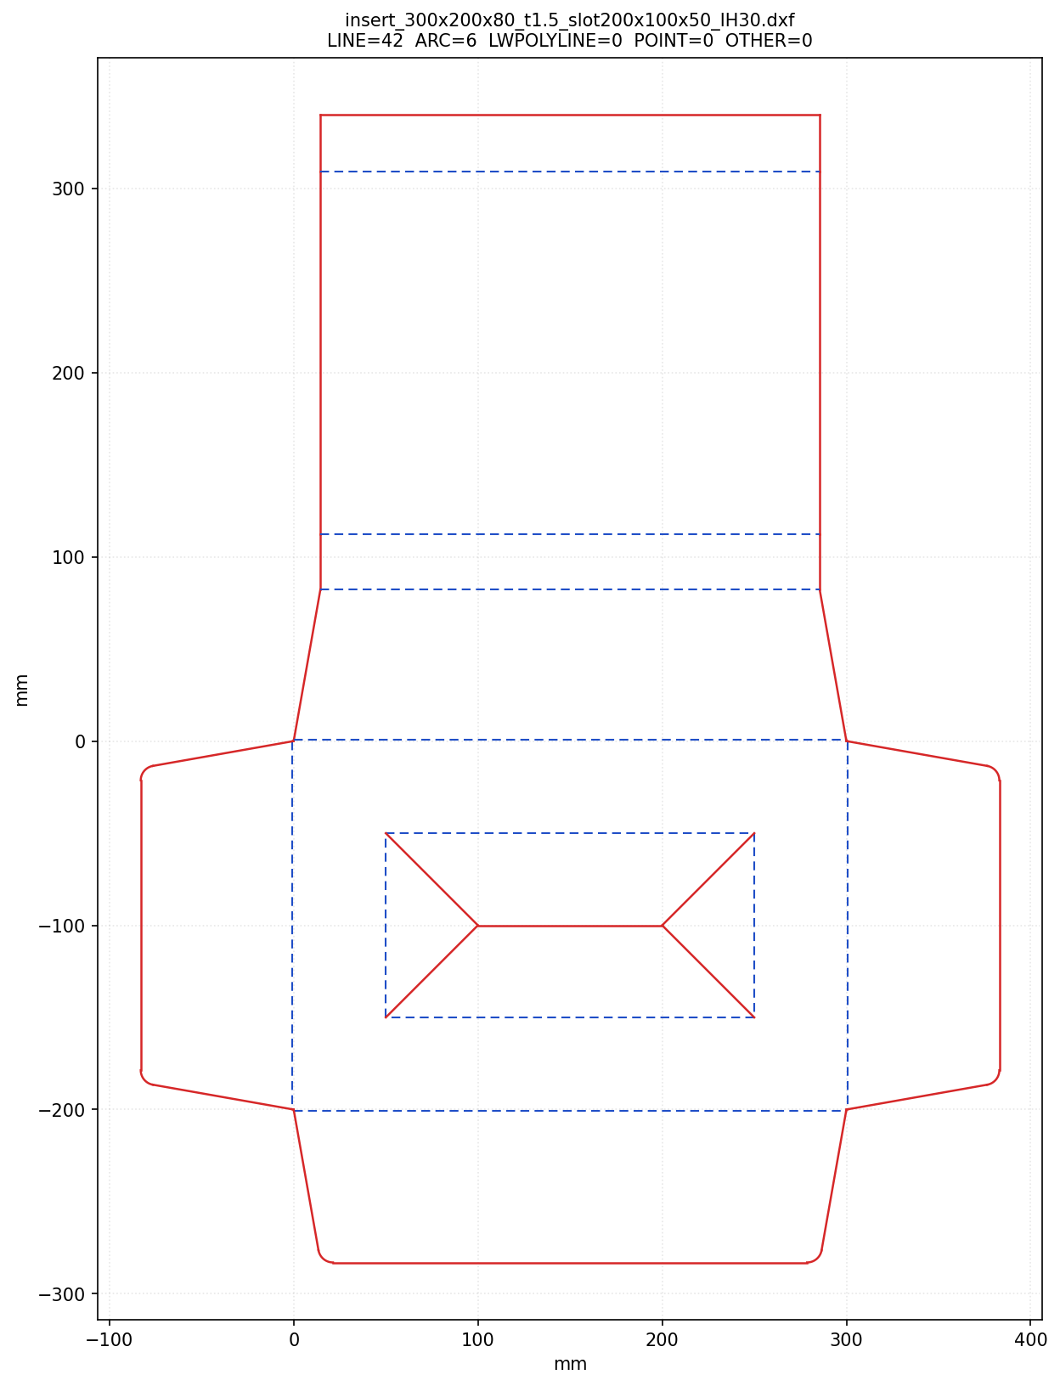
Assembly_docs/packaging/passthrough_insert_300x200x80_t1.5_slot200x100x50_IH30.png
