layered-logic/infinity-mirror/Assembly_docs/packaging/passthrough_insert_300x200x120_t1.5_slot150x150x25_IH95.png

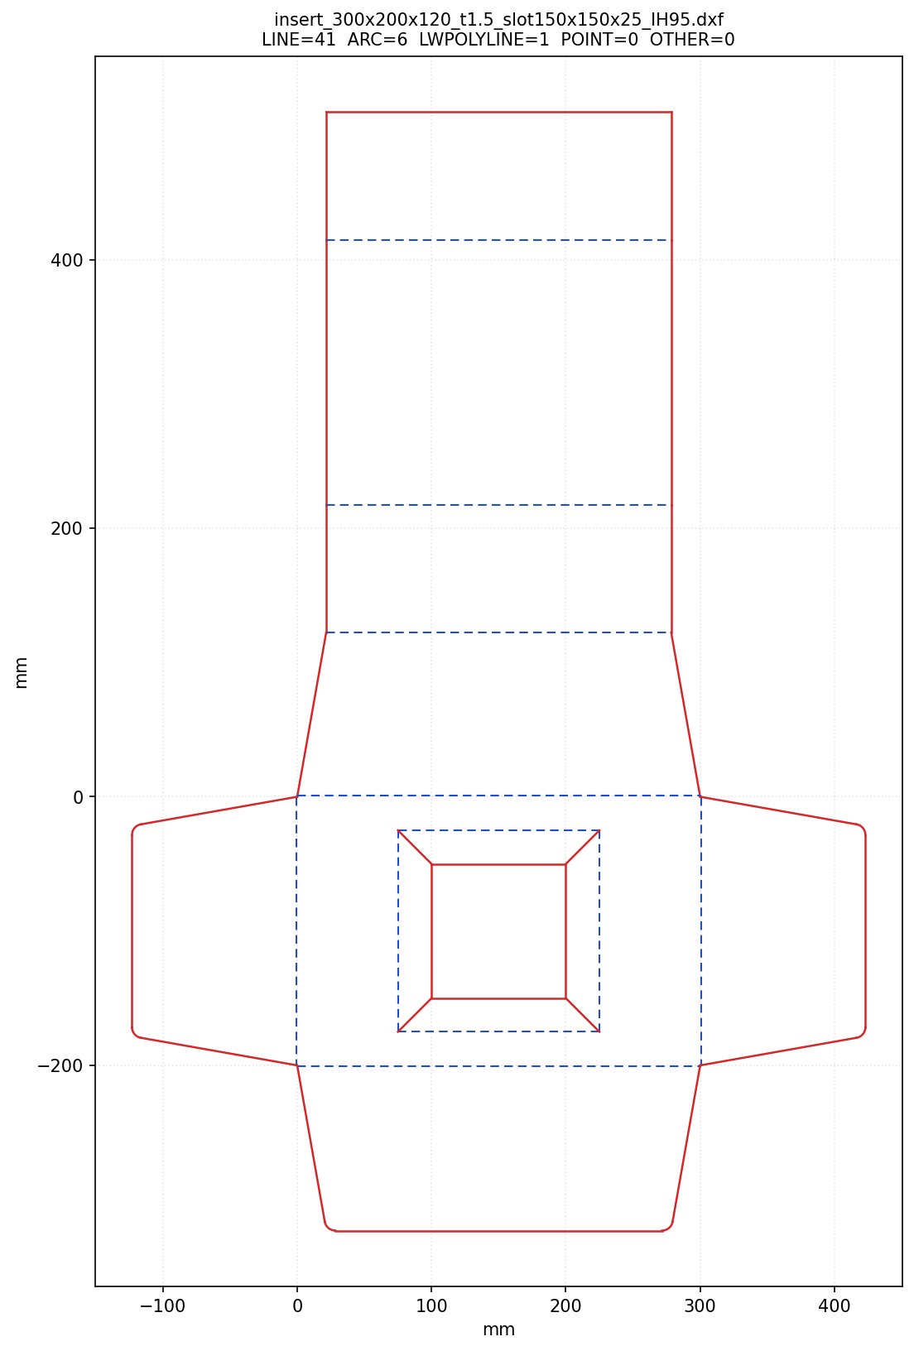
Assembly_docs/packaging/passthrough_insert_300x200x120_t1.5_slot150x150x25_IH95.png
