layered-logic/infinity-mirror/Assembly_docs/packaging/passthrough_insert_400x200x80_t1.5_slot150x150x25_IH55.png

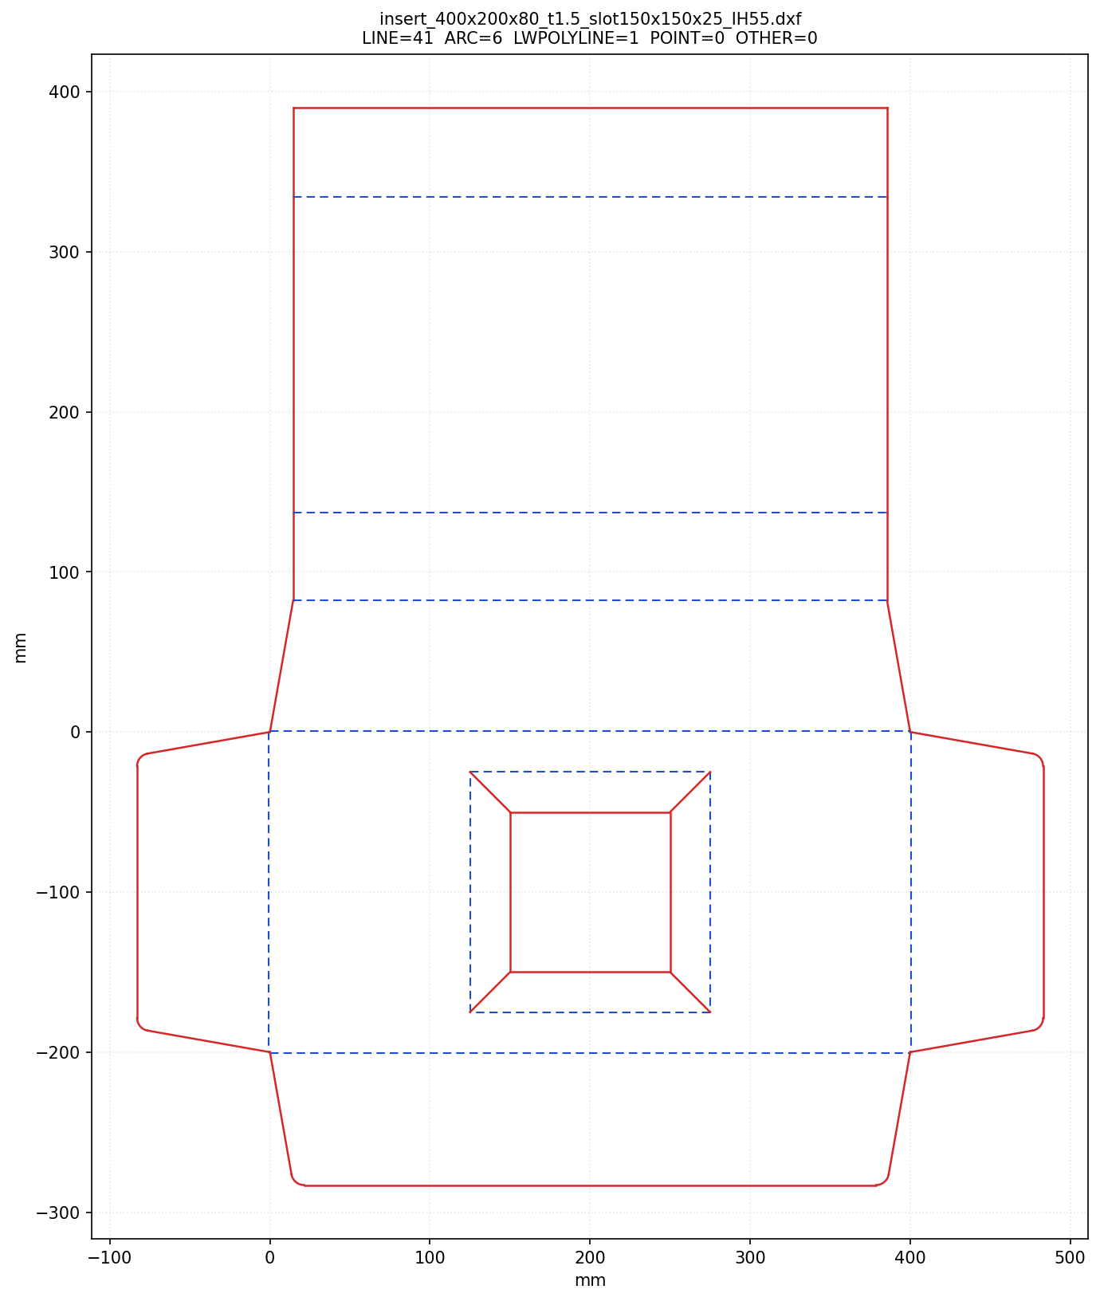
Assembly_docs/packaging/passthrough_insert_400x200x80_t1.5_slot150x150x25_IH55.png
