layered-logic/infinity-mirror/Assembly_docs/packaging/passthrough_mailer_300x200x80_t3.png

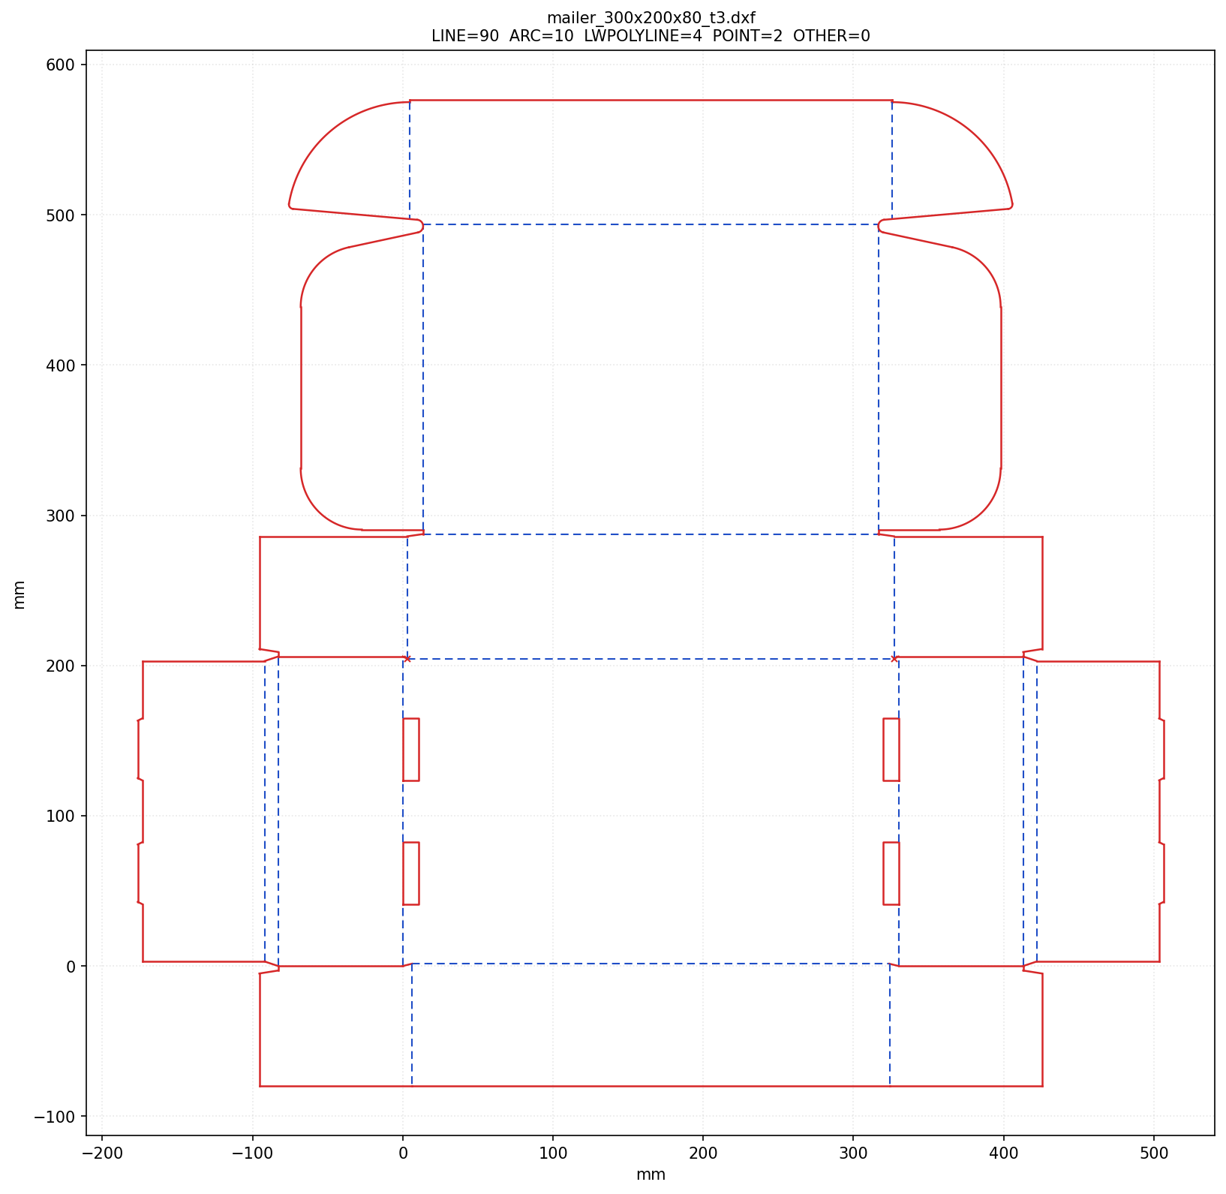
Assembly_docs/packaging/passthrough_mailer_300x200x80_t3.png
