layered-logic/infinity-mirror/Assembly_docs/packaging/passthrough_mailer_300x200x120_t1.5.png

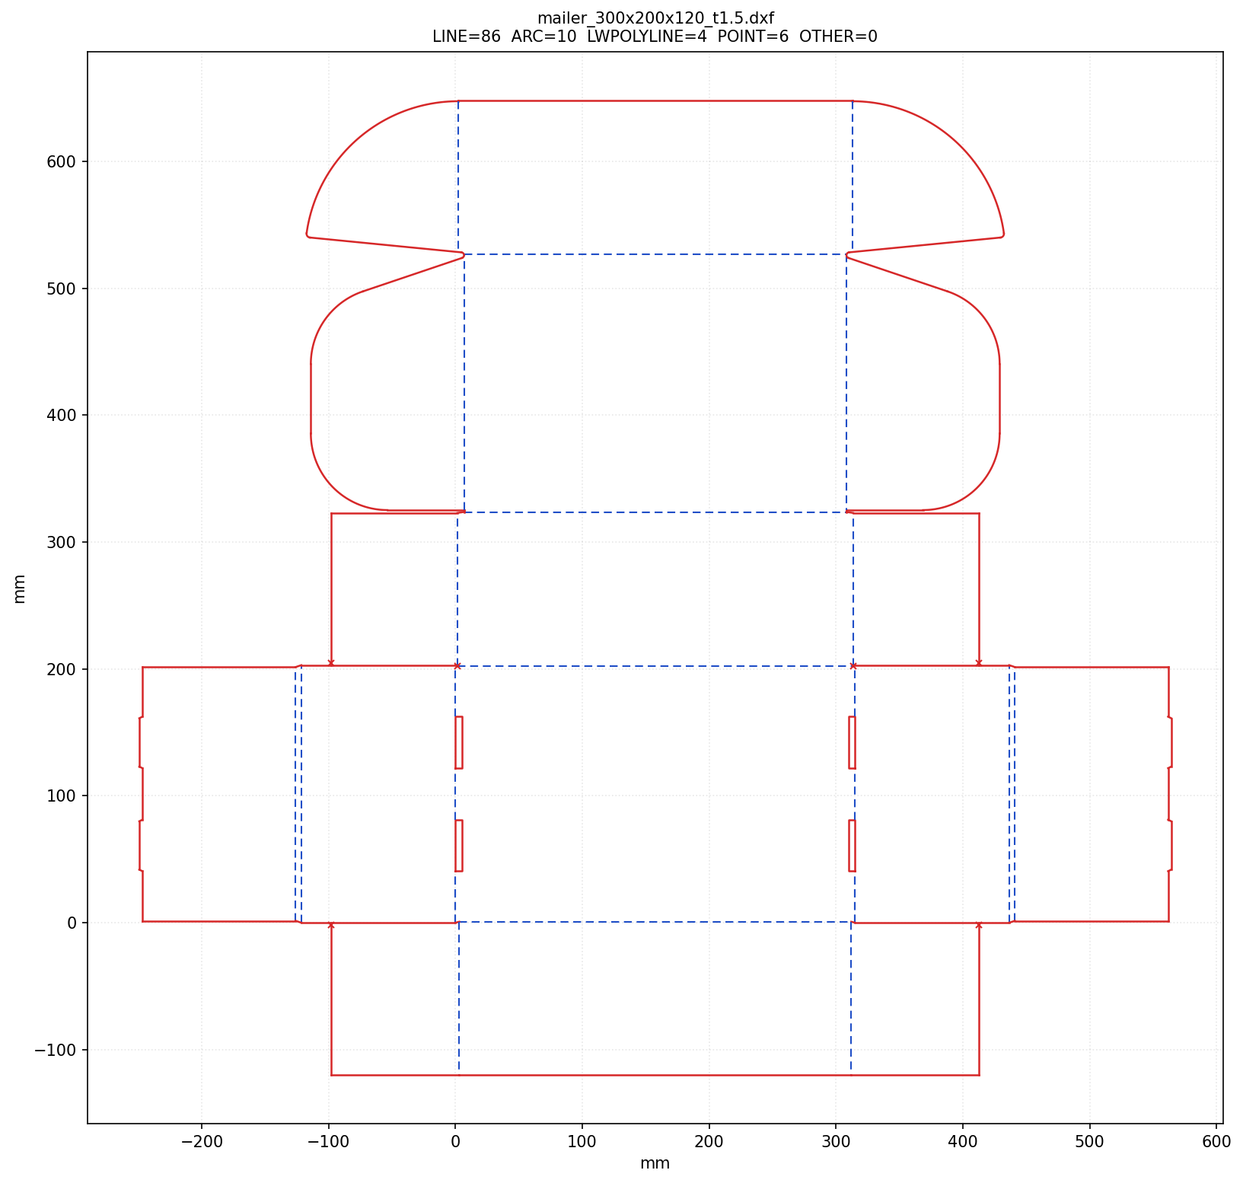
Assembly_docs/packaging/passthrough_mailer_300x200x120_t1.5.png
