layered-logic/infinity-mirror/Assembly_docs/IM_SVG_Maker/verify_laser.png

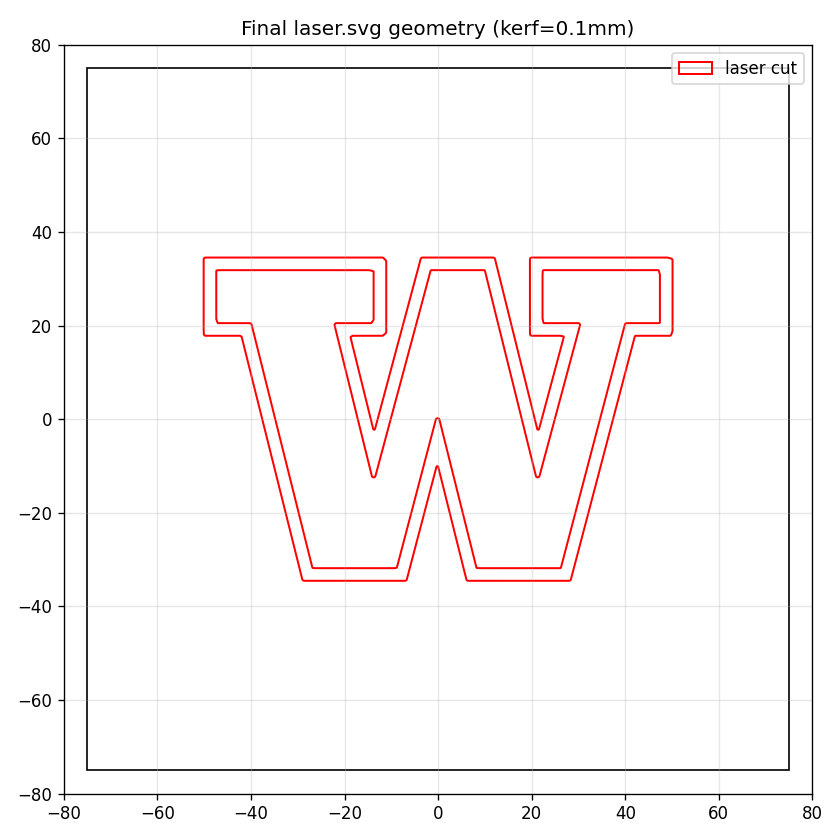
Assembly_docs/IM_SVG_Maker/verify_laser.png
